kuato781/spirit-wave-stand/documentation/product-images/01-components.jpg

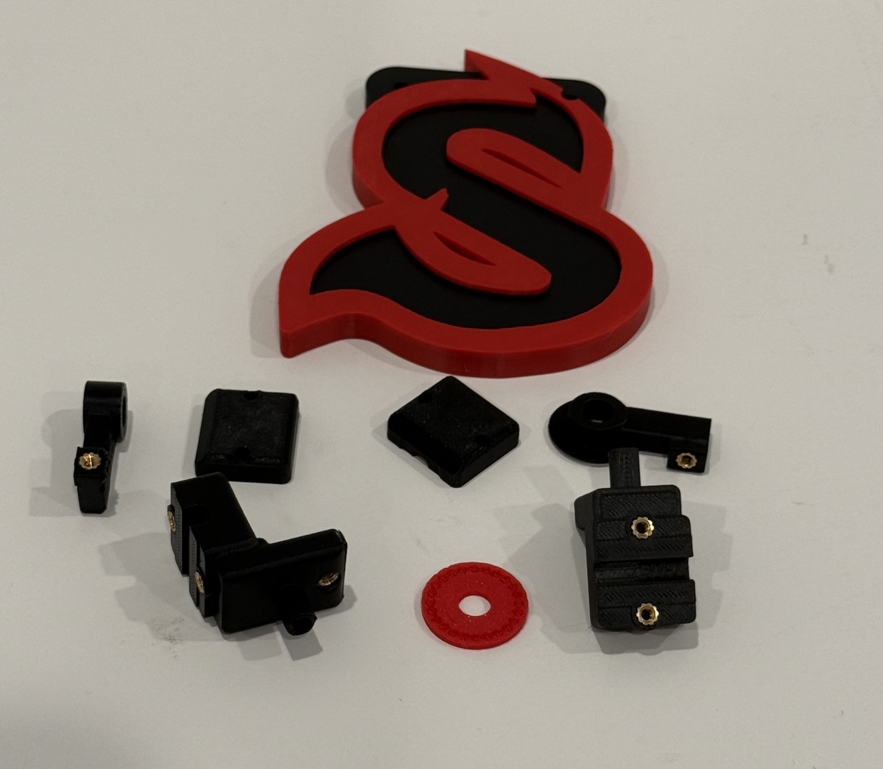
documentation/product-images/01-components.jpg
