kuato781/spirit-wave-stand/stl-scad/stand/SpiritWave-RED-LOWER.scad

module red_lower_2d() {
  union() {
    polygon(points=[[-44.12985,-99.23666], [-44.06508,-99.32389], [-43.99628,-99.40856], [-43.92369,-99.49047], [-43.84755,-99.56939], [-43.76811,-99.64512], [-43.68559,-99.71743], [-43.60024,-99.78611], [-43.51230,-99.85095], [-43.42201,-99.91172], [-43.32960,-99.96821], [-43.23531,-100.02021], [-43.13938,-100.06749], [-43.04206,-100.10985], [-42.94358,-100.14706], [-42.84417,-100.17892], [-42.74409,-100.20519], [-42.64356,-100.22568], [-42.54282,-100.24016], [-42.44212,-100.24841], [-42.34170,-100.25022], [-42.24178,-100.24537], [-42.14261,-100.23368], [-42.04425,-100.21529], [-41.94667,-100.19057], [-41.84984,-100.15990], [-41.75373,-100.12367], [-41.65830,-100.08225], [-41.56353,-100.03602], [-41.46937,-99.98537], [-41.37581,-99.93066], [-41.28280,-99.87229], [-41.19031,-99.81063], [-41.09831,-99.74607], [-41.00677,-99.67897], [-40.91565,-99.60973], [-40.82493,-99.53871], [-40.73457,-99.46631], [-40.64453,-99.39289], [-40.55479,-99.31885], [-40.46531,-99.24456], [-40.37606,-99.17039], [-40.28701,-99.09665], [-40.19815,-99.02337], [-40.10945,-98.95055], [-40.02092,-98.87817], [-39.93253,-98.80622], [-39.84426,-98.73471], [-39.75612,-98.66362], [-39.66807,-98.59294], [-39.58011,-98.52267], [-39.49223,-98.45280], [-39.40440,-98.38332], [-39.31662,-98.31422], [-39.22887,-98.24549], [-39.14114,-98.17713], [-39.05342,-98.10913], [-38.96568,-98.04148], [-38.87792,-97.97417], [-38.79012,-97.90719], [-38.70226,-97.84055], [-38.61435,-97.77422], [-38.52635,-97.70820], [-38.43826,-97.64248], [-38.35006,-97.57706], [-38.26173,-97.51193], [-38.17328,-97.44708], [-38.08467,-97.38249], [-37.99590,-97.31817], [-37.90695,-97.25411], [-37.81781,-97.19029], [-37.72846,-97.12671], [-37.63889,-97.06337], [-37.54909,-97.00024], [-37.45905,-96.93733], [-37.36874,-96.87463], [-37.27815,-96.81213], [-37.18728,-96.74983], [-37.09610,-96.68770], [-37.00461,-96.62575], [-36.91278,-96.56397], [-36.82063,-96.50235], [-36.72816,-96.44088], [-36.63539,-96.37957], [-36.54234,-96.31839], [-36.44901,-96.25735], [-36.35543,-96.19643], [-36.26160,-96.13564], [-36.16754,-96.07496], [-36.07326,-96.01439], [-35.97879,-95.95392], [-35.88412,-95.89355], [-35.78928,-95.83327], [-35.69429,-95.77307], [-35.59915,-95.71294], [-35.50387,-95.65289], [-35.40848,-95.59289], [-35.31299,-95.53295], [-35.21741,-95.47307], [-35.12176,-95.41322], [-35.02604,-95.35341], [-34.93028,-95.29363], [-34.83449,-95.23388], [-34.73867,-95.17414], [-34.64286,-95.11441], [-34.54705,-95.05469], [-34.45127,-94.99496], [-34.35553,-94.93522], [-34.25984,-94.87547], [-34.16422,-94.81569], [-34.06868,-94.75589], [-33.97323,-94.69605], [-33.87790,-94.63616], [-33.78268,-94.57623], [-33.68761,-94.51625], [-33.59268,-94.45620], [-33.49792,-94.39608], [-33.40335,-94.33589], [-33.30896,-94.27562], [-33.21476,-94.21528], [-33.12072,-94.15490], [-33.02681,-94.09452], [-32.93301,-94.03416], [-32.83930,-93.97386], [-32.74564,-93.91364], [-32.65202,-93.85353], [-32.55841,-93.79357], [-32.46477,-93.73377], [-32.37110,-93.67419], [-32.27736,-93.61483], [-32.18352,-93.55574], [-32.08957,-93.49694], [-31.99547,-93.43846], [-31.90120,-93.38034], [-31.80674,-93.32259], [-31.71206,-93.26527], [-31.61713,-93.20838], [-31.52194,-93.15197], [-31.42644,-93.09606], [-31.33063,-93.04068], [-31.23447,-92.98586], [-31.13794,-92.93164], [-31.04101,-92.87804], [-30.94366,-92.82509], [-30.84586,-92.77283], [-30.74759,-92.72127], [-30.64883,-92.67046], [-30.54953,-92.62042], [-30.44969,-92.57118], [-30.34928,-92.52278], [-30.24827,-92.47524], [-30.14663,-92.42859], [-30.04434,-92.38286], [-29.94138,-92.33808], [-29.83772,-92.29429], [-29.73333,-92.25150], [-29.62819,-92.20976], [-29.52232,-92.16908], [-29.41573,-92.12947], [-29.30846,-92.09093], [-29.20052,-92.05350], [-29.09196,-92.01717], [-28.98279,-91.98196], [-28.87303,-91.94788], [-28.76273,-91.91494], [-28.65189,-91.88315], [-28.54055,-91.85254], [-28.42874,-91.82310], [-28.31648,-91.79485], [-28.20379,-91.76780], [-28.09071,-91.74197], [-27.97726,-91.71736], [-27.86346,-91.69400], [-27.74935,-91.67188], [-27.63494,-91.65102], [-27.52027,-91.63144], [-27.40536,-91.61315], [-27.29024,-91.59615], [-27.17493,-91.58046], [-27.05946,-91.56610], [-26.94385,-91.55307], [-26.82814,-91.54138], [-26.71235,-91.53105], [-26.59650,-91.52210], [-26.48063,-91.51452], [-26.36475,-91.50834], [-26.24889,-91.50356], [-26.13309,-91.50021], [-26.01736,-91.49828], [-25.90173,-91.49779], [-25.78624,-91.49876], [-25.67090,-91.50120], [-25.55574,-91.50511], [-25.44078,-91.51051], [-25.32607,-91.51741], [-25.21161,-91.52583], [-25.09743,-91.53576], [-24.98354,-91.54718], [-24.86995,-91.56009], [-24.75667,-91.57446], [-24.64371,-91.59027], [-24.53108,-91.60750], [-24.41878,-91.62615], [-24.30683,-91.64618], [-24.19524,-91.66758], [-24.08401,-91.69034], [-23.97315,-91.71444], [-23.86268,-91.73985], [-23.75261,-91.76657], [-23.64294,-91.79457], [-23.53368,-91.82383], [-23.42485,-91.85434], [-23.31644,-91.88608], [-23.20848,-91.91904], [-23.10097,-91.95318], [-22.99392,-91.98851], [-22.88733,-92.02499], [-22.78123,-92.06261], [-22.67562,-92.10136], [-22.57050,-92.14121], [-22.46590,-92.18215], [-22.36181,-92.22415], [-22.25824,-92.26721], [-22.15522,-92.31130], [-22.05273,-92.35641], [-21.95081,-92.40252], [-21.84944,-92.44961], [-21.74866,-92.49766], [-21.64845,-92.54665], [-21.54884,-92.59657], [-21.44983,-92.64740], [-21.35143,-92.69913], [-21.25366,-92.75172], [-21.15651,-92.80517], [-21.06000,-92.85946], [-20.96413,-92.91457], [-20.86886,-92.97045], [-20.77416,-93.02709], [-20.68001,-93.08444], [-20.58639,-93.14249], [-20.49326,-93.20120], [-20.40061,-93.26053], [-20.30839,-93.32046], [-20.21659,-93.38096], [-20.12518,-93.44199], [-20.03413,-93.50352], [-19.94342,-93.56553], [-19.85301,-93.62799], [-19.76289,-93.69085], [-19.67302,-93.75409], [-19.58337,-93.81769], [-19.49393,-93.88160], [-19.40466,-93.94581], [-19.31554,-94.01026], [-19.22653,-94.07495], [-19.13763,-94.13983], [-19.04878,-94.20488], [-18.95998,-94.27006], [-18.87119,-94.33534], [-18.78238,-94.40069], [-18.69353,-94.46609], [-18.60462,-94.53150], [-18.51560,-94.59688], [-18.42647,-94.66221], [-18.33719,-94.72746], [-18.24773,-94.79260], [-18.15807,-94.85760], [-18.06818,-94.92241], [-17.97804,-94.98703], [-17.88761,-95.05140], [-17.79687,-95.11551], [-17.70579,-95.17932], [-17.61435,-95.24280], [-17.52253,-95.30592], [-17.43033,-95.36870], [-17.33777,-95.43112], [-17.24484,-95.49320], [-17.15157,-95.55494], [-17.05796,-95.61633], [-16.96402,-95.67739], [-16.86976,-95.73811], [-16.77518,-95.79850], [-16.68030,-95.85856], [-16.58513,-95.91829], [-16.48967,-95.97771], [-16.39394,-96.03680], [-16.29794,-96.09557], [-16.20169,-96.15403], [-16.10518,-96.21218], [-16.00844,-96.27002], [-15.91147,-96.32756], [-15.81427,-96.38479], [-15.71687,-96.44173], [-15.61927,-96.49837], [-15.52147,-96.55471], [-15.42348,-96.61077], [-15.32533,-96.66653], [-15.22701,-96.72202], [-15.12853,-96.77722], [-15.02990,-96.83214], [-14.93114,-96.88679], [-14.83225,-96.94117], [-14.73324,-96.99527], [-14.63411,-97.04911], [-14.53489,-97.10269], [-14.43558,-97.15600], [-14.33618,-97.20906], [-14.23671,-97.26186], [-14.13717,-97.31441], [-14.03758,-97.36671], [-13.93794,-97.41877], [-13.83827,-97.47058], [-13.73854,-97.52214], [-13.63877,-97.57346], [-13.53895,-97.62454], [-13.43908,-97.67536], [-13.33914,-97.72594], [-13.23915,-97.77627], [-13.13908,-97.82634], [-13.03895,-97.87617], [-12.93875,-97.92574], [-12.83847,-97.97506], [-12.73811,-98.02412], [-12.63767,-98.07293], [-12.53714,-98.12149], [-12.43652,-98.16978], [-12.33581,-98.21782], [-12.23500,-98.26560], [-12.13409,-98.31311], [-12.03307,-98.36037], [-11.93195,-98.40736], [-11.83071,-98.45410], [-11.72936,-98.50056], [-11.62789,-98.54677], [-11.52630,-98.59270], [-11.42458,-98.63837], [-11.32273,-98.68377], [-11.22075,-98.72891], [-11.11863,-98.77377], [-11.01638,-98.81836], [-10.91397,-98.86269], [-10.81143,-98.90673], [-10.70873,-98.95051], [-10.60587,-98.99401], [-10.50286,-99.03724], [-10.39969,-99.08019], [-10.29635,-99.12286], [-10.19284,-99.16525], [-10.08916,-99.20737], [-9.98531,-99.24920], [-9.88129,-99.29076], [-9.77710,-99.33203], [-9.67275,-99.37303], [-9.56824,-99.41374], [-9.46357,-99.45417], [-9.35875,-99.49433], [-9.25378,-99.53420], [-9.14866,-99.57379], [-9.04340,-99.61310], [-8.93799,-99.65212], [-8.83245,-99.69087], [-8.72677,-99.72933], [-8.62096,-99.76752], [-8.51503,-99.80542], [-8.40896,-99.84303], [-8.30278,-99.88037], [-8.19648,-99.91742], [-8.09006,-99.95419], [-7.98353,-99.99067], [-7.87688,-100.02688], [-7.77014,-100.06280], [-7.66329,-100.09843], [-7.55634,-100.13379], [-7.44929,-100.16885], [-7.34215,-100.20364], [-7.23492,-100.23814], [-7.12760,-100.27235], [-7.02019,-100.30628], [-6.91271,-100.33993], [-6.80515,-100.37329], [-6.69751,-100.40637], [-6.58980,-100.43916], [-6.48203,-100.47166], [-6.37419,-100.50388], [-6.26628,-100.53581], [-6.15832,-100.56746], [-6.05030,-100.59882], [-5.94223,-100.62989], [-5.83410,-100.66067], [-5.72590,-100.69115], [-5.61763,-100.72133], [-5.50929,-100.75120], [-5.40087,-100.78076], [-5.29237,-100.81000], [-5.18378,-100.83891], [-5.07509,-100.86750], [-4.96632,-100.89576], [-4.85744,-100.92367], [-4.74845,-100.95125], [-4.63936,-100.97847], [-4.53015,-101.00535], [-4.42083,-101.03186], [-4.31137,-101.05802], [-4.20180,-101.08380], [-4.09208,-101.10922], [-3.98224,-101.13425], [-3.87225,-101.15890], [-3.76211,-101.18317], [-3.65182,-101.20704], [-3.54138,-101.23052], [-3.43078,-101.25359], [-3.32001,-101.27626], [-3.20908,-101.29851], [-3.09797,-101.32035], [-2.98669,-101.34176], [-2.87522,-101.36275], [-2.76357,-101.38330], [-2.65172,-101.40342], [-2.53968,-101.42309], [-2.42744,-101.44232], [-2.31499,-101.46110], [-2.20233,-101.47942], [-2.08946,-101.49727], [-1.97637,-101.51467], [-1.86306,-101.53158], [-1.74952,-101.54803], [-1.63575,-101.56399], [-1.52177,-101.57949], [-1.40757,-101.59453], [-1.29316,-101.60912], [-1.17854,-101.62325], [-1.06373,-101.63695], [-0.94873,-101.65022], [-0.83354,-101.66307], [-0.71818,-101.67549], [-0.60264,-101.68751], [-0.48693,-101.69912], [-0.37106,-101.71034], [-0.25504,-101.72117], [-0.13887,-101.73162], [-0.02255,-101.74170], [0.09391,-101.75141], [0.21049,-101.76076], [0.32721,-101.76976], [0.44404,-101.77841], [0.56099,-101.78673], [0.67804,-101.79471], [0.79520,-101.80238], [0.91246,-101.80973], [1.02980,-101.81677], [1.14723,-101.82351], [1.26474,-101.82995], [1.38232,-101.83611], [1.49997,-101.84199], [1.61768,-101.84760], [1.73545,-101.85295], [1.85326,-101.85803], [1.97112,-101.86287], [2.08902,-101.86747], [2.20694,-101.87182], [2.32490,-101.87595], [2.44287,-101.87986], [2.56086,-101.88356], [2.67885,-101.88705], [2.79684,-101.89034], [2.91484,-101.89344], [3.03282,-101.89634], [3.15080,-101.89905], [3.26876,-101.90155], [3.38672,-101.90386], [3.50465,-101.90596], [3.62257,-101.90785], [3.74047,-101.90952], [3.85835,-101.91098], [3.97620,-101.91223], [4.09402,-101.91325], [4.21182,-101.91404], [4.32958,-101.91461], [4.44732,-101.91494], [4.56501,-101.91504], [4.68267,-101.91491], [4.80029,-101.91453], [4.91787,-101.91391], [5.03540,-101.91303], [5.15289,-101.91191], [5.27033,-101.91054], [5.38772,-101.90891], [5.50505,-101.90701], [5.62233,-101.90486], [5.73955,-101.90244], [5.85671,-101.89974], [5.97381,-101.89678], [6.09085,-101.89354], [6.20782,-101.89002], [6.32472,-101.88621], [6.44155,-101.88212], [6.55831,-101.87775], [6.67499,-101.87308], [6.79160,-101.86811], [6.90813,-101.86285], [7.02457,-101.85728], [7.14093,-101.85141], [7.25721,-101.84523], [7.37339,-101.83874], [7.48949,-101.83194], [7.60549,-101.82482], [7.72140,-101.81738], [7.83721,-101.80961], [7.95293,-101.80152], [8.06854,-101.79309], [8.18404,-101.78433], [8.29945,-101.77524], [8.41474,-101.76581], [8.52992,-101.75603], [8.64499,-101.74591], [8.75995,-101.73543], [8.87479,-101.72461], [8.98951,-101.71343], [9.10411,-101.70189], [9.21858,-101.68998], [9.33293,-101.67772], [9.44715,-101.66508], [9.56124,-101.65207], [9.67520,-101.63869], [9.78903,-101.62493], [9.90272,-101.61079], [10.01627,-101.59626], [10.12968,-101.58134], [10.24294,-101.56604], [10.35606,-101.55034], [10.46903,-101.53424], [10.58185,-101.51774], [10.69452,-101.50084], [10.80704,-101.48354], [10.91940,-101.46582], [11.03160,-101.44769], [11.14364,-101.42914], [11.25551,-101.41017], [11.36723,-101.39078], [11.47877,-101.37097], [11.59014,-101.35072], [11.70135,-101.33005], [11.81237,-101.30893], [11.92322,-101.28738], [12.03390,-101.26539], [12.14439,-101.24295], [12.25470,-101.22007], [12.36484,-101.19677], [12.47482,-101.17305], [12.58463,-101.14893], [12.69429,-101.12443], [12.80381,-101.09956], [12.91318,-101.07434], [13.02242,-101.04877], [13.13153,-101.02288], [13.24053,-100.99668], [13.34941,-100.97018], [13.45818,-100.94339], [13.56685,-100.91634], [13.67542,-100.88903], [13.78391,-100.86148], [13.89232,-100.83371], [14.00065,-100.80572], [14.10892,-100.77754], [14.21712,-100.74917], [14.32527,-100.72064], [14.43337,-100.69195], [14.54143,-100.66312], [14.64945,-100.63417], [14.75745,-100.60511], [14.86542,-100.57595], [14.97338,-100.54671], [15.08132,-100.51740], [15.18927,-100.48804], [15.29722,-100.45864], [15.40518,-100.42921], [15.51316,-100.39978], [15.62116,-100.37035], [15.72919,-100.34093], [15.83726,-100.31155], [15.94537,-100.28222], [16.05353,-100.25295], [16.16175,-100.22376], [16.27003,-100.19465], [16.37838,-100.16565], [16.48680,-100.13675], [16.59529,-100.10795], [16.70384,-100.07924], [16.81246,-100.05061], [16.92113,-100.02205], [17.02986,-99.99356], [17.13865,-99.96513], [17.24748,-99.93675], [17.35637,-99.90841], [17.46531,-99.88010], [17.57429,-99.85183], [17.68331,-99.82357], [17.79237,-99.79533], [17.90146,-99.76709], [18.01059,-99.73885], [18.11976,-99.71061], [18.22895,-99.68234], [18.33817,-99.65405], [18.44741,-99.62573], [18.55668,-99.59736], [18.66596,-99.56895], [18.77526,-99.54048], [18.88458,-99.51195], [18.99390,-99.48336], [19.10324,-99.45468], [19.21258,-99.42591], [19.32192,-99.39706], [19.43127,-99.36810], [19.54061,-99.33904], [19.64996,-99.30986], [19.75929,-99.28055], [19.86862,-99.25112], [19.97793,-99.22155], [20.08723,-99.19183], [20.19652,-99.16195], [20.30578,-99.13192], [20.41503,-99.10172], [20.52425,-99.07134], [20.63344,-99.04078], [20.74261,-99.01002], [20.85174,-98.97907], [20.96084,-98.94791], [21.06989,-98.91655], [21.17890,-98.88498], [21.28787,-98.85321], [21.39677,-98.82123], [21.50562,-98.78903], [21.61440,-98.75663], [21.72312,-98.72401], [21.83176,-98.69118], [21.94032,-98.65813], [22.04879,-98.62487], [22.15718,-98.59138], [22.26547,-98.55768], [22.37366,-98.52376], [22.48176,-98.48961], [22.58974,-98.45524], [22.69761,-98.42064], [22.80536,-98.38582], [22.91299,-98.35077], [23.02048,-98.31549], [23.12785,-98.27998], [23.23508,-98.24424], [23.34217,-98.20826], [23.44911,-98.17205], [23.55590,-98.13560], [23.66253,-98.09892], [23.76900,-98.06199], [23.87530,-98.02483], [23.98143,-97.98742], [24.08738,-97.94977], [24.19315,-97.91187], [24.29874,-97.87373], [24.40413,-97.83535], [24.50933,-97.79671], [24.61433,-97.75782], [24.71912,-97.71868], [24.82371,-97.67929], [24.92807,-97.63965], [25.03223,-97.59975], [25.13618,-97.55959], [25.23992,-97.51917], [25.34347,-97.47849], [25.44683,-97.43755], [25.55000,-97.39635], [25.65300,-97.35488], [25.75581,-97.31314], [25.85846,-97.27114], [25.96094,-97.22886], [26.06326,-97.18631], [26.16543,-97.14349], [26.26744,-97.10039], [26.36932,-97.05702], [26.47105,-97.01337], [26.57265,-96.96944], [26.67412,-96.92522], [26.77547,-96.88073], [26.87670,-96.83594], [26.97782,-96.79088], [27.07883,-96.74552], [27.17974,-96.69987], [27.28055,-96.65394], [27.38127,-96.60771], [27.48191,-96.56118], [27.58246,-96.51436], [27.68293,-96.46724], [27.78334,-96.41983], [27.88368,-96.37211], [27.98396,-96.32408], [28.08418,-96.27576], [28.18436,-96.22713], [28.28449,-96.17819], [28.38458,-96.12894], [28.48463,-96.07938], [28.58466,-96.02951], [28.68466,-95.97932], [28.78465,-95.92882], [28.88461,-95.87801], [28.98455,-95.82688], [29.08446,-95.77543], [29.18433,-95.72368], [29.28415,-95.67162], [29.38392,-95.61926], [29.48363,-95.56659], [29.58327,-95.51361], [29.68284,-95.46034], [29.78233,-95.40677], [29.88173,-95.35290], [29.98104,-95.29874], [30.08025,-95.24428], [30.17935,-95.18953], [30.27833,-95.13450], [30.37719,-95.07917], [30.47592,-95.02356], [30.57452,-94.96767], [30.67298,-94.91150], [30.77128,-94.85505], [30.86943,-94.79831], [30.96742,-94.74131], [31.06523,-94.68403], [31.16287,-94.62647], [31.26033,-94.56865], [31.35759,-94.51056], [31.45466,-94.45220], [31.55152,-94.39358], [31.64817,-94.33470], [31.74460,-94.27555], [31.84081,-94.21615], [31.93679,-94.15649], [32.03252,-94.09657], [32.12801,-94.03640], [32.22325,-93.97598], [32.31823,-93.91531], [32.41294,-93.85440], [32.50738,-93.79324], [32.60155,-93.73182], [32.69545,-93.67016], [32.78909,-93.60824], [32.88247,-93.54605], [32.97559,-93.48360], [33.06846,-93.42087], [33.16109,-93.35787], [33.25347,-93.29459], [33.34561,-93.23103], [33.43751,-93.16718], [33.52918,-93.10303], [33.62062,-93.03859], [33.71184,-92.97384], [33.80284,-92.90878], [33.89362,-92.84342], [33.98418,-92.77774], [34.07454,-92.71174], [34.16469,-92.64542], [34.25464,-92.57876], [34.34439,-92.51178], [34.43394,-92.44445], [34.52331,-92.37678], [34.61249,-92.30877], [34.70149,-92.24041], [34.79030,-92.17169], [34.87895,-92.10261], [34.96742,-92.03317], [35.05572,-91.96335], [35.14386,-91.89317], [35.23184,-91.82261], [35.31967,-91.75166], [35.40734,-91.68033], [35.49486,-91.60861], [35.58224,-91.53649], [35.66948,-91.46398], [35.75658,-91.39106], [35.84355,-91.31773], [35.93039,-91.24399], [36.01709,-91.16984], [36.10364,-91.09530], [36.19003,-91.02036], [36.27624,-90.94503], [36.36228,-90.86933], [36.44812,-90.79326], [36.53376,-90.71683], [36.61919,-90.64003], [36.70439,-90.56289], [36.78935,-90.48541], [36.87407,-90.40759], [36.95854,-90.32944], [37.04273,-90.25097], [37.12665,-90.17219], [37.21028,-90.09310], [37.29361,-90.01371], [37.37663,-89.93403], [37.45932,-89.85407], [37.54169,-89.77382], [37.62372,-89.69331], [37.70539,-89.61253], [37.78669,-89.53149], [37.86763,-89.45020], [37.94818,-89.36867], [38.02833,-89.28691], [38.10808,-89.20491], [38.18741,-89.12270], [38.26631,-89.04027], [38.34477,-88.95763], [38.42278,-88.87480], [38.50034,-88.79177], [38.57742,-88.70855], [38.65402,-88.62516], [38.73013,-88.54159], [38.80574,-88.45786], [38.88084,-88.37398], [38.95541,-88.28994], [39.02944,-88.20576], [39.10296,-88.12143], [39.17596,-88.03695], [39.24845,-87.95232], [39.32046,-87.86753], [39.39197,-87.78258], [39.46302,-87.69747], [39.53360,-87.61218], [39.60373,-87.52673], [39.67342,-87.44110], [39.74268,-87.35529], [39.81152,-87.26930], [39.87995,-87.18313], [39.94798,-87.09676], [40.01562,-87.01020], [40.08288,-86.92345], [40.14977,-86.83649], [40.21631,-86.74933], [40.28249,-86.66196], [40.34834,-86.57439], [40.41387,-86.48659], [40.47907,-86.39858], [40.54397,-86.31035], [40.60858,-86.22189], [40.67290,-86.13320], [40.73695,-86.04428], [40.80073,-85.95512], [40.86426,-85.86573], [40.92754,-85.77609], [40.99059,-85.68620], [41.05342,-85.59606], [41.11604,-85.50567], [41.17846,-85.41502], [41.24068,-85.32411], [41.30273,-85.23293], [41.36460,-85.14148], [41.42632,-85.04977], [41.48788,-84.95777], [41.54931,-84.86550], [41.61061,-84.77294], [41.67177,-84.68010], [41.73279,-84.58698], [41.79364,-84.49359], [41.85433,-84.39991], [41.91483,-84.30596], [41.97514,-84.21174], [42.03523,-84.11724], [42.09511,-84.02248], [42.15475,-83.92745], [42.21415,-83.83216], [42.27328,-83.73660], [42.33215,-83.64078], [42.39073,-83.54470], [42.44902,-83.44837], [42.50700,-83.35178], [42.56466,-83.25493], [42.62198,-83.15784], [42.67896,-83.06049], [42.73558,-82.96290], [42.79183,-82.86506], [42.84770,-82.76698], [42.90317,-82.66866], [42.95823,-82.57010], [43.01287,-82.47130], [43.06708,-82.37227], [43.12085,-82.27300], [43.17416,-82.17350], [43.22699,-82.07377], [43.27935,-81.97381], [43.33121,-81.87363], [43.38256,-81.77323], [43.43339,-81.67260], [43.48369,-81.57175], [43.53344,-81.47069], [43.58264,-81.36940], [43.63127,-81.26791], [43.67932,-81.16620], [43.72678,-81.06429], [43.77367,-80.96219], [43.82002,-80.85991], [43.86586,-80.75748], [43.91121,-80.65492], [43.95608,-80.55224], [44.00052,-80.44946], [44.04453,-80.34660], [44.08816,-80.24368], [44.13141,-80.14071], [44.17431,-80.03772], [44.21690,-79.93471], [44.25919,-79.83172], [44.30121,-79.72876], [44.34298,-79.62584], [44.38452,-79.52298], [44.42587,-79.42021], [44.46705,-79.31754], [44.50807,-79.21499], [44.54895,-79.11256], [44.58967,-79.01020], [44.63019,-78.90788], [44.67048,-78.80556], [44.71052,-78.70318], [44.75027,-78.60071], [44.78971,-78.49810], [44.82880,-78.39531], [44.86752,-78.29229], [44.90583,-78.18901], [44.94370,-78.08541], [44.98112,-77.98145], [45.01803,-77.87710], [45.05443,-77.77230], [45.09027,-77.66701], [45.12552,-77.56119], [45.16017,-77.45480], [45.19417,-77.34779], [45.22749,-77.24012], [45.26013,-77.13176], [45.29209,-77.02276], [45.32340,-76.91318], [45.35409,-76.80311], [45.38418,-76.69260], [45.41372,-76.58173], [45.44271,-76.47056], [45.47120,-76.35917], [45.49921,-76.24761], [45.52677,-76.13597], [45.55390,-76.02430], [45.58064,-75.91269], [45.60700,-75.80118], [45.63303,-75.68986], [45.65874,-75.57880], [45.68417,-75.46806], [45.70935,-75.35770], [45.73429,-75.24781], [45.75903,-75.13844], [45.78360,-75.02967], [45.80800,-74.92147], [45.83220,-74.81378], [45.85619,-74.70655], [45.87995,-74.59969], [45.90346,-74.49314], [45.92671,-74.38685], [45.94968,-74.28073], [45.97234,-74.17474], [45.99469,-74.06879], [46.01669,-73.96282], [46.03834,-73.85678], [46.05962,-73.75058], [46.08050,-73.64417], [46.10097,-73.53747], [46.12101,-73.43043], [46.14061,-73.32298], [46.15974,-73.21505], [46.17838,-73.10657], [46.19652,-72.99748], [46.21415,-72.88773], [46.23126,-72.77733], [46.24785,-72.66630], [46.26393,-72.55468], [46.27948,-72.44247], [46.29452,-72.32971], [46.30904,-72.21641], [46.32305,-72.10260], [46.33654,-71.98831], [46.34951,-71.87355], [46.36197,-71.75836], [46.37391,-71.64274], [46.38534,-71.52673], [46.39625,-71.41035], [46.40665,-71.29362], [46.41653,-71.17656], [46.42590,-71.05921], [46.43476,-70.94157], [46.44310,-70.82368], [46.45093,-70.70555], [46.45825,-70.58721], [46.46506,-70.46869], [46.47135,-70.35000], [46.47714,-70.23118], [46.48241,-70.11223], [46.48717,-69.99319], [46.49142,-69.87408], [46.49516,-69.75492], [46.49839,-69.63574], [46.50111,-69.51655], [46.50332,-69.39739], [46.50502,-69.27827], [46.50622,-69.15921], [46.50690,-69.04025], [46.50708,-68.92140], [46.50675,-68.80268], [46.50591,-68.68413], [46.50456,-68.56576], [46.50271,-68.44759], [46.50035,-68.32965], [46.49749,-68.21196], [46.49412,-68.09452], [46.49025,-67.97732], [46.48588,-67.86036], [46.48102,-67.74364], [46.47566,-67.62715], [46.46982,-67.51089], [46.46348,-67.39485], [46.45667,-67.27904], [46.44936,-67.16344], [46.44158,-67.04805], [46.43333,-66.93287], [46.42459,-66.81789], [46.41539,-66.70312], [46.40572,-66.58854], [46.39558,-66.47416], [46.38497,-66.35996], [46.37391,-66.24595], [46.36239,-66.13212], [46.35041,-66.01847], [46.33798,-65.90499], [46.32510,-65.79168], [46.31177,-65.67853], [46.29799,-65.56555], [46.28377,-65.45272], [46.26912,-65.34005], [46.25402,-65.22753], [46.23849,-65.11515], [46.22253,-65.00291], [46.20614,-64.89082], [46.18933,-64.77885], [46.17209,-64.66702], [46.15442,-64.55531], [46.13634,-64.44372], [46.11785,-64.33225], [46.09894,-64.22090], [46.07962,-64.10966], [46.05989,-63.99852], [46.03975,-63.88748], [46.01922,-63.77655], [45.99828,-63.66571], [45.97693,-63.55498], [45.95518,-63.44436], [45.93301,-63.33385], [45.91043,-63.22345], [45.88744,-63.11318], [45.86402,-63.00304], [45.84019,-62.89302], [45.81593,-62.78314], [45.79125,-62.67339], [45.76614,-62.56379], [45.74060,-62.45434], [45.71463,-62.34503], [45.68822,-62.23588], [45.66137,-62.12689], [45.63409,-62.01807], [45.60636,-61.90941], [45.57818,-61.80092], [45.54956,-61.69261], [45.52049,-61.58448], [45.49096,-61.47653], [45.46098,-61.36877], [45.43055,-61.26121], [45.39965,-61.15384], [45.36829,-61.04667], [45.33647,-60.93971], [45.30418,-60.83296], [45.27142,-60.72643], [45.23819,-60.62011], [45.20449,-60.51401], [45.17030,-60.40814], [45.13564,-60.30250], [45.10050,-60.19710], [45.06487,-60.09194], [45.02876,-59.98702], [44.99216,-59.88234], [44.95506,-59.77792], [44.91747,-59.67376], [44.87939,-59.56985], [44.84081,-59.46621], [44.80173,-59.36282], [44.76216,-59.25969], [44.72209,-59.15681], [44.68153,-59.05419], [44.64048,-58.95181], [44.59894,-58.84967], [44.55690,-58.74778], [44.51438,-58.64612], [44.47136,-58.54470], [44.42786,-58.44352], [44.38387,-58.34257], [44.33939,-58.24184], [44.29443,-58.14134], [44.24898,-58.04106], [44.20305,-57.94101], [44.15663,-57.84117], [44.10974,-57.74154], [44.06236,-57.64213], [44.01450,-57.54293], [43.96616,-57.44393], [43.91734,-57.34514], [43.86805,-57.24655], [43.81827,-57.14815], [43.76802,-57.04995], [43.71730,-56.95195], [43.66610,-56.85413], [43.61443,-56.75651], [43.56228,-56.65906], [43.50966,-56.56180], [43.45657,-56.46472], [43.40301,-56.36782], [43.34899,-56.27109], [43.29449,-56.17453], [43.23952,-56.07814], [43.18409,-55.98191], [43.12819,-55.88585], [43.07183,-55.78995], [43.01500,-55.69421], [42.95771,-55.59863], [42.89996,-55.50323], [42.84174,-55.40799], [42.78306,-55.31294], [42.72391,-55.21807], [42.66430,-55.12339], [42.60423,-55.02891], [42.54370,-54.93462], [42.48270,-54.84053], [42.42124,-54.74666], [42.35932,-54.65299], [42.29694,-54.55955], [42.23410,-54.46632], [42.17079,-54.37333], [42.10703,-54.28056], [42.04280,-54.18803], [41.97812,-54.09575], [41.91297,-54.00371], [41.84736,-53.91192], [41.78130,-53.82038], [41.71477,-53.72911], [41.64779,-53.63810], [41.58034,-53.54736], [41.51244,-53.45690], [41.44408,-53.36672], [41.37526,-53.27682], [41.30599,-53.18721], [41.23625,-53.09789], [41.16606,-53.00888], [41.09541,-52.92016], [41.02431,-52.83176], [40.95274,-52.74367], [40.88072,-52.65589], [40.80825,-52.56844], [40.73532,-52.48132], [40.66193,-52.39453], [40.58808,-52.30807], [40.51379,-52.22196], [40.43905,-52.13618], [40.36388,-52.05074], [40.28828,-51.96564], [40.21227,-51.88087], [40.13584,-51.79644], [40.05902,-51.71234], [39.98181,-51.62858], [39.90422,-51.54515], [39.82625,-51.46205], [39.74793,-51.37928], [39.66924,-51.29684], [39.59021,-51.21473], [39.51085,-51.13295], [39.43116,-51.05149], [39.35115,-50.97036], [39.27082,-50.88955], [39.19020,-50.80907], [39.10929,-50.72891], [39.02809,-50.64908], [38.94661,-50.56956], [38.86488,-50.49037], [38.78288,-50.41149], [38.70064,-50.33294], [38.61815,-50.25470], [38.53544,-50.17677], [38.45251,-50.09917], [38.36936,-50.02187], [38.28601,-49.94490], [38.20247,-49.86823], [38.11874,-49.79188], [38.03483,-49.71584], [37.95076,-49.64010], [37.86652,-49.56468], [37.78214,-49.48957], [37.69762,-49.41476], [37.61296,-49.34026], [37.52818,-49.26607], [37.44328,-49.19218], [37.35827,-49.11859], [37.27314,-49.04530], [37.18787,-48.97232], [37.10248,-48.89962], [37.01694,-48.82722], [36.93125,-48.75511], [36.84540,-48.68329], [36.75939,-48.61175], [36.67322,-48.54050], [36.58686,-48.46953], [36.50032,-48.39883], [36.41359,-48.32841], [36.32666,-48.25827], [36.23953,-48.18839], [36.15218,-48.11878], [36.06462,-48.04944], [35.97683,-47.98036], [35.88881,-47.91155], [35.80055,-47.84299], [35.71205,-47.77468], [35.62329,-47.70663], [35.53427,-47.63883], [35.44498,-47.57128], [35.35542,-47.50397], [35.26558,-47.43691], [35.17546,-47.37008], [35.08504,-47.30350], [34.99431,-47.23715], [34.90328,-47.17103], [34.81193,-47.10515], [34.72026,-47.03949], [34.62826,-46.97406], [34.53593,-46.90885], [34.44325,-46.84387], [34.35023,-46.77910], [34.25684,-46.71455], [34.16310,-46.65021], [34.06898,-46.58608], [33.97448,-46.52216], [33.87960,-46.45845], [33.78436,-46.39492], [33.68930,-46.33131], [33.59543,-46.26710], [33.50376,-46.20180], [33.41532,-46.13487], [33.33111,-46.06583], [33.25216,-45.99414], [33.17948,-45.91930], [33.11410,-45.84081], [33.05670,-45.75829], [33.00704,-45.67179], [32.96474,-45.58144], [32.92940,-45.48736], [32.90063,-45.38966], [32.87803,-45.28846], [32.86123,-45.18388], [32.84981,-45.07605], [32.84340,-44.96507], [32.84160,-44.85108], [32.84402,-44.73419], [32.85028,-44.61464], [32.86010,-44.49310], [32.87319,-44.37037], [32.88929,-44.24724], [32.90812,-44.12448], [32.92940,-44.00289], [32.95285,-43.88326], [32.97821,-43.76636], [33.00520,-43.65290], [33.03355,-43.54282], [33.06302,-43.43567], [33.09334,-43.33101], [33.12426,-43.22837], [33.15553,-43.12733], [33.18689,-43.02742], [33.21809,-42.92819], [33.24887,-42.82920], [33.27897,-42.73000], [33.30814,-42.63013], [33.33614,-42.52917], [33.36286,-42.42691], [33.38835,-42.32340], [33.41267,-42.21871], [33.43587,-42.11288], [33.45801,-42.00597], [33.47914,-41.89803], [33.49932,-41.78913], [33.51859,-41.67931], [33.53702,-41.56864], [33.55466,-41.45717], [33.57156,-41.34495], [33.58778,-41.23204], [33.60337,-41.11849], [33.61839,-41.00437], [33.63289,-40.88973], [33.64692,-40.77461], [33.66054,-40.65909], [33.67381,-40.54321], [33.68677,-40.42703], [33.69949,-40.31060], [33.71201,-40.19399], [33.72440,-40.07724], [33.73670,-39.96042], [33.74897,-39.84357], [33.76127,-39.72676], [33.77365,-39.61003], [33.78616,-39.49346], [33.79886,-39.37708], [33.81180,-39.26096], [33.82504,-39.14515], [33.83863,-39.02970], [33.85262,-38.91468], [33.86708,-38.80015], [33.88205,-38.68614], [33.89759,-38.57273], [33.91375,-38.45996], [33.93059,-38.34789], [33.94817,-38.23658], [33.96653,-38.12608], [33.98572,-38.01644], [34.00568,-37.90760], [34.02635,-37.79949], [34.04764,-37.69203], [34.06946,-37.58514], [34.09175,-37.47873], [34.11442,-37.37274], [34.13740,-37.26708], [34.16060,-37.16166], [34.18394,-37.05642], [34.20735,-36.95127], [34.23074,-36.84614], [34.25404,-36.74093], [34.27717,-36.63559], [34.30004,-36.53001], [34.32258,-36.42413], [34.34472,-36.31787], [34.36636,-36.21115], [34.38743,-36.10388], [34.40785,-35.99599], [34.42759,-35.88744], [34.44665,-35.77826], [34.46508,-35.66847], [34.48290,-35.55813], [34.50015,-35.44725], [34.51686,-35.33588], [34.53305,-35.22405], [34.54876,-35.11181], [34.56401,-34.99917], [34.57885,-34.88618], [34.59329,-34.77287], [34.60737,-34.65929], [34.62113,-34.54545], [34.63458,-34.43141], [34.64777,-34.31719], [34.66072,-34.20282], [34.67346,-34.08836], [34.68603,-33.97382], [34.69845,-33.85925], [34.71076,-33.74467], [34.72297,-33.63013], [34.73510,-33.51560], [34.74713,-33.40110], [34.75907,-33.28662], [34.77092,-33.17215], [34.78268,-33.05769], [34.79434,-32.94324], [34.80591,-32.82879], [34.81738,-32.71434], [34.82875,-32.59988], [34.84002,-32.48541], [34.85120,-32.37093], [34.86228,-32.25643], [34.87325,-32.14191], [34.88412,-32.02736], [34.89490,-31.91278], [34.90556,-31.79817], [34.91612,-31.68353], [34.92658,-31.56884], [34.93693,-31.45411], [34.94717,-31.33933], [34.95731,-31.22450], [34.96733,-31.10961], [34.97725,-30.99466], [34.98705,-30.87964], [34.99674,-30.76456], [35.00632,-30.64940], [35.01579,-30.53417], [35.02514,-30.41886], [35.03437,-30.30347], [35.04349,-30.18798], [35.05249,-30.07241], [35.06137,-29.95674], [35.07013,-29.84097], [35.07878,-29.72509], [35.08730,-29.60911], [35.09570,-29.49302], [35.10397,-29.37681], [35.11212,-29.26049], [35.12015,-29.14404], [35.12805,-29.02746], [35.13582,-28.91077], [35.14345,-28.79395], [35.15095,-28.67703], [35.15829,-28.55999], [35.16550,-28.44285], [35.17254,-28.32561], [35.17943,-28.20828], [35.18616,-28.09085], [35.19272,-27.97333], [35.19911,-27.85573], [35.20533,-27.73805], [35.21136,-27.62030], [35.21722,-27.50247], [35.22288,-27.38458], [35.22835,-27.26662], [35.23362,-27.14861], [35.23869,-27.03054], [35.24356,-26.91242], [35.24821,-26.79425], [35.25265,-26.67604], [35.25687,-26.55779], [35.26086,-26.43951], [35.26463,-26.32120], [35.26816,-26.20287], [35.27146,-26.08451], [35.27451,-25.96614], [35.27732,-25.84775], [35.27988,-25.72936], [35.28218,-25.61096], [35.28422,-25.49256], [35.28600,-25.37416], [35.28751,-25.25577], [35.28875,-25.13740], [35.28971,-25.01904], [35.29039,-24.90070], [35.29078,-24.78238], [35.29088,-24.66410], [35.29069,-24.54584], [35.29019,-24.42763], [35.28940,-24.30945], [35.28829,-24.19133], [35.28688,-24.07325], [35.28514,-23.95522], [35.28308,-23.83725], [35.28070,-23.71935], [35.27799,-23.60151], [35.27494,-23.48374], [35.27155,-23.36605], [35.26782,-23.24843], [35.26374,-23.13090], [35.25931,-23.01346], [35.25452,-22.89611], [35.24937,-22.77885], [35.24386,-22.66169], [35.23797,-22.54464], [35.23171,-22.42769], [35.22507,-22.31086], [35.21804,-22.19414], [35.21063,-22.07755], [35.20282,-21.96108], [35.19462,-21.84473], [35.18602,-21.72852], [35.17701,-21.61245], [35.16759,-21.49652], [35.15776,-21.38074], [35.14750,-21.26510], [35.13682,-21.14962], [35.12572,-21.03430], [35.11418,-20.91914], [35.10221,-20.80414], [35.08979,-20.68932], [35.07693,-20.57467], [35.06362,-20.46020], [35.04985,-20.34592], [35.03563,-20.23182], [35.02094,-20.11791], [35.00578,-20.00420], [34.99015,-19.89069], [34.97404,-19.77738], [34.95746,-19.66428], [34.94039,-19.55138], [34.92284,-19.43869], [34.90482,-19.32620], [34.88631,-19.21391], [34.86733,-19.10182], [34.84787,-18.98992], [34.82793,-18.87822], [34.80751,-18.76671], [34.78662,-18.65538], [34.76525,-18.54425], [34.74341,-18.43330], [34.72109,-18.32253], [34.69830,-18.21195], [34.67503,-18.10154], [34.65129,-17.99132], [34.62708,-17.88126], [34.60239,-17.77138], [34.57723,-17.66168], [34.55160,-17.55214], [34.52550,-17.44277], [34.49893,-17.33356], [34.47189,-17.22452], [34.44437,-17.11563], [34.41639,-17.00691], [34.38794,-16.89835], [34.35903,-16.78993], [34.32964,-16.68168], [34.29979,-16.57357], [34.26947,-16.46561], [34.23868,-16.35780], [34.20743,-16.25013], [34.17572,-16.14261], [34.14354,-16.03523], [34.11089,-15.92798], [34.07778,-15.82088], [34.04421,-15.71390], [34.01018,-15.60707], [33.97568,-15.50036], [33.94072,-15.39378], [33.90530,-15.28733], [33.86943,-15.18102], [33.83310,-15.07486], [33.79632,-14.96884], [33.75910,-14.86296], [33.72143,-14.75724], [33.68331,-14.65168], [33.64476,-14.54627], [33.60577,-14.44104], [33.56634,-14.33596], [33.52649,-14.23107], [33.48620,-14.12634], [33.44549,-14.02180], [33.40435,-13.91744], [33.36279,-13.81327], [33.32081,-13.70929], [33.27842,-13.60550], [33.23561,-13.50191], [33.19239,-13.39853], [33.14877,-13.29535], [33.10474,-13.19239], [33.06031,-13.08964], [33.01547,-12.98710], [32.97024,-12.88479], [32.92462,-12.78271], [32.87860,-12.68085], [32.83220,-12.57923], [32.78541,-12.47785], [32.73823,-12.37671], [32.69068,-12.27581], [32.64274,-12.17516], [32.59443,-12.07477], [32.54575,-11.97463], [32.49670,-11.87476], [32.44727,-11.77515], [32.39749,-11.67581], [32.34734,-11.57674], [32.29683,-11.47794], [32.24597,-11.37940], [32.19477,-11.28110], [32.14323,-11.18303], [32.09136,-11.08516], [32.03917,-10.98748], [31.98666,-10.88996], [31.93385,-10.79260], [31.88074,-10.69537], [31.82734,-10.59826], [31.77365,-10.50124], [31.71969,-10.40431], [31.66546,-10.30743], [31.61097,-10.21060], [31.55623,-10.11379], [31.50124,-10.01699], [31.44601,-9.92018], [31.39055,-9.82334], [31.33487,-9.72645], [31.27898,-9.62950], [31.22288,-9.53247], [31.16658,-9.43534], [31.11008,-9.33809], [31.05340,-9.24070], [30.99655,-9.14316], [30.93952,-9.04544], [30.88234,-8.94754], [30.82500,-8.84943], [30.76751,-8.75109], [30.70988,-8.65251], [30.65213,-8.55366], [30.59424,-8.45454], [30.53625,-8.35511], [30.47814,-8.25538], [30.41994,-8.15530], [30.36164,-8.05488], [30.30325,-7.95408], [30.24479,-7.85291], [30.18595,-7.75199], [30.12576,-7.65357], [30.06310,-7.56005], [29.99691,-7.47390], [29.92607,-7.39753], [29.84952,-7.33338], [29.76614,-7.28389], [29.67489,-7.25147], [29.57600,-7.23695], [29.47163,-7.23892], [29.36404,-7.25579], [29.25553,-7.28597], [29.14839,-7.32786], [29.04490,-7.37989], [28.94734,-7.44046], [28.85800,-7.50798], [28.77917,-7.58087], [28.71314,-7.65752], [28.66159,-7.73664], [28.62411,-7.81790], [28.59987,-7.90117], [28.58799,-7.98635], [28.58763,-8.07332], [28.59792,-8.16196], [28.61801,-8.25217], [28.64705,-8.34383], [28.68418,-8.43681], [28.72853,-8.53102], [28.77926,-8.62632], [28.83552,-8.72262], [28.89643,-8.81979], [28.96115,-8.91772], [29.02882,-9.01629], [29.09859,-9.11539], [29.16959,-9.21491], [29.24098,-9.31473], [29.31189,-9.41473], [29.38181,-9.51486], [29.45072,-9.61509], [29.51862,-9.71544], [29.58555,-9.81590], [29.65153,-9.91648], [29.71658,-10.01717], [29.78071,-10.11799], [29.84395,-10.21893], [29.90632,-10.31998], [29.96784,-10.42117], [30.02854,-10.52248], [30.08843,-10.62391], [30.14753,-10.72548], [30.20587,-10.82717], [30.26346,-10.92899], [30.32033,-11.03095], [30.37650,-11.13305], [30.43199,-11.23528], [30.48682,-11.33764], [30.54101,-11.44015], [30.59459,-11.54280], [30.64757,-11.64558], [30.69997,-11.74852], [30.75182,-11.85159], [30.80314,-11.95482], [30.85394,-12.05819], [30.90426,-12.16171], [30.95410,-12.26539], [31.00350,-12.36922], [31.05246,-12.47320], [31.10102,-12.57733], [31.14920,-12.68163], [31.19701,-12.78608], [31.24448,-12.89069], [31.29162,-12.99547], [31.33847,-13.10041], [31.38503,-13.20551], [31.43134,-13.31078], [31.47740,-13.41622], [31.52321,-13.52183], [31.56876,-13.62760], [31.61404,-13.73354], [31.65905,-13.83964], [31.70377,-13.94591], [31.74820,-14.05235], [31.79233,-14.15895], [31.83614,-14.26571], [31.87964,-14.37264], [31.92282,-14.47974], [31.96565,-14.58699], [32.00814,-14.69441], [32.05028,-14.80199], [32.09206,-14.90974], [32.13347,-15.01764], [32.17450,-15.12571], [32.21514,-15.23393], [32.25538,-15.34232], [32.29523,-15.45087], [32.33465,-15.55958], [32.37366,-15.66844], [32.41224,-15.77747], [32.45038,-15.88665], [32.48807,-15.99599], [32.52531,-16.10549], [32.56208,-16.21515], [32.59838,-16.32496], [32.63420,-16.43493], [32.66953,-16.54505], [32.70435,-16.65533], [32.73868,-16.76577], [32.77249,-16.87636], [32.80577,-16.98710], [32.83852,-17.09800], [32.87073,-17.20905], [32.90239,-17.32025], [32.93349,-17.43161], [32.96403,-17.54312], [32.99399,-17.65478], [33.02340,-17.76659], [33.05225,-17.87854], [33.08054,-17.99064], [33.10828,-18.10288], [33.13546,-18.21525], [33.16210,-18.32777], [33.18820,-18.44042], [33.21376,-18.55320], [33.23878,-18.66612], [33.26326,-18.77916], [33.28722,-18.89233], [33.31065,-19.00562], [33.33356,-19.11904], [33.35594,-19.23257], [33.37781,-19.34623], [33.39916,-19.46000], [33.42000,-19.57388], [33.44034,-19.68787], [33.46017,-19.80197], [33.47950,-19.91618], [33.49833,-20.03049], [33.51666,-20.14491], [33.53451,-20.25942], [33.55187,-20.37404], [33.56874,-20.48875], [33.58513,-20.60355], [33.60104,-20.71844], [33.61648,-20.83343], [33.63145,-20.94850], [33.64594,-21.06365], [33.65998,-21.17889], [33.67355,-21.29421], [33.68666,-21.40961], [33.69931,-21.52508], [33.71152,-21.64063], [33.72327,-21.75625], [33.73458,-21.87193], [33.74544,-21.98769], [33.75587,-22.10351], [33.76586,-22.21940], [33.77542,-22.33534], [33.78455,-22.45134], [33.79325,-22.56741], [33.80153,-22.68352], [33.80939,-22.79969], [33.81683,-22.91590], [33.82386,-23.03217], [33.83048,-23.14848], [33.83669,-23.26483], [33.84250,-23.38123], [33.84791,-23.49766], [33.85292,-23.61413], [33.85754,-23.73064], [33.86177,-23.84717], [33.86561,-23.96374], [33.86907,-24.08034], [33.87214,-24.19696], [33.87484,-24.31361], [33.87716,-24.43028], [33.87912,-24.54696], [33.88070,-24.66367], [33.88192,-24.78039], [33.88278,-24.89712], [33.88329,-25.01386], [33.88343,-25.13061], [33.88323,-25.24737], [33.88268,-25.36413], [33.88178,-25.48090], [33.88054,-25.59766], [33.87897,-25.71442], [33.87705,-25.83118], [33.87481,-25.94793], [33.87224,-26.06467], [33.86934,-26.18140], [33.86612,-26.29811], [33.86258,-26.41481], [33.85872,-26.53150], [33.85456,-26.64816], [33.85008,-26.76480], [33.84530,-26.88142], [33.84022,-26.99802], [33.83484,-27.11459], [33.82917,-27.23114], [33.82321,-27.34767], [33.81697,-27.46417], [33.81045,-27.58065], [33.80365,-27.69710], [33.79658,-27.81353], [33.78925,-27.92992], [33.78164,-28.04630], [33.77378,-28.16264], [33.76567,-28.27895], [33.75730,-28.39524], [33.74869,-28.51150], [33.73983,-28.62773], [33.73074,-28.74392], [33.72141,-28.86009], [33.71185,-28.97622], [33.70206,-29.09232], [33.69205,-29.20839], [33.68182,-29.32443], [33.67138,-29.44043], [33.66073,-29.55640], [33.64987,-29.67234], [33.63881,-29.78824], [33.62755,-29.90410], [33.61610,-30.01993], [33.60446,-30.13572], [33.59264,-30.25147], [33.58063,-30.36718], [33.56844,-30.48286], [33.55609,-30.59850], [33.54356,-30.71410], [33.53087,-30.82965], [33.51802,-30.94517], [33.50501,-31.06065], [33.49185,-31.17608], [33.47854,-31.29148], [33.46509,-31.40683], [33.45150,-31.52214], [33.43777,-31.63740], [33.42391,-31.75262], [33.40992,-31.86779], [33.39581,-31.98292], [33.38158,-32.09801], [33.36723,-32.21304], [33.35277,-32.32803], [33.33821,-32.44298], [33.32354,-32.55787], [33.30877,-32.67272], [33.29391,-32.78752], [33.27896,-32.90227], [33.26392,-33.01696], [33.24879,-33.13161], [33.23359,-33.24621], [33.21832,-33.36075], [33.20298,-33.47524], [33.18756,-33.58968], [33.17209,-33.70407], [33.15656,-33.81840], [33.14098,-33.93268], [33.12534,-34.04691], [33.10967,-34.16108], [33.09395,-34.27519], [33.07819,-34.38924], [33.06240,-34.50324], [33.04658,-34.61718], [33.03073,-34.73107], [33.01487,-34.84489], [32.99899,-34.95866], [32.98309,-35.07237], [32.96719,-35.18601], [32.95128,-35.29960], [32.93538,-35.41312], [32.91947,-35.52659], [32.90358,-35.63999], [32.88770,-35.75332], [32.87183,-35.86660], [32.85598,-35.97981], [32.84016,-36.09296], [32.82436,-36.20604], [32.80858,-36.31906], [32.79281,-36.43202], [32.77702,-36.54493], [32.76122,-36.65778], [32.74538,-36.77059], [32.72951,-36.88335], [32.71358,-36.99606], [32.69759,-37.10874], [32.68152,-37.22137], [32.66536,-37.33398], [32.64911,-37.44655], [32.63275,-37.55909], [32.61627,-37.67161], [32.59966,-37.78410], [32.58290,-37.89658], [32.56599,-38.00904], [32.54892,-38.12148], [32.53167,-38.23392], [32.51423,-38.34634], [32.49659,-38.45877], [32.47874,-38.57119], [32.46066,-38.68361], [32.44236,-38.79603], [32.42381,-38.90847], [32.40500,-39.02091], [32.38593,-39.13337], [32.36657,-39.24584], [32.34693,-39.35834], [32.32699,-39.47085], [32.30673,-39.58339], [32.28616,-39.69596], [32.26524,-39.80856], [32.24398,-39.92119], [32.22236,-40.03386], [32.20038,-40.14658], [32.17801,-40.25933], [32.15525,-40.37213], [32.13209,-40.48498], [32.10852,-40.59789], [32.08455,-40.71084], [32.06023,-40.82385], [32.03562,-40.93692], [32.01079,-41.05003], [31.98579,-41.16320], [31.96068,-41.27642], [31.93551,-41.38970], [31.91035,-41.50302], [31.88526,-41.61640], [31.86028,-41.72983], [31.83549,-41.84331], [31.81094,-41.95684], [31.78668,-42.07042], [31.76279,-42.18405], [31.73930,-42.29773], [31.71629,-42.41146], [31.69381,-42.52524], [31.67192,-42.63906], [31.65068,-42.75294], [31.63015,-42.86686], [31.61038,-42.98083], [31.59144,-43.09485], [31.57337,-43.20891], [31.55625,-43.32303], [31.54013,-43.43718], [31.52506,-43.55139], [31.51111,-43.66563], [31.49833,-43.77993], [31.48679,-43.89427], [31.47653,-44.00865], [31.46763,-44.12308], [31.46013,-44.23755], [31.45410,-44.35207], [31.44960,-44.46663], [31.44667,-44.58123], [31.44539,-44.69588], [31.44581,-44.81056], [31.44799,-44.92529], [31.45198,-45.04006], [31.45785,-45.15487], [31.46572,-45.26958], [31.47570,-45.38406], [31.48793,-45.49814], [31.50255,-45.61166], [31.51968,-45.72445], [31.53945,-45.83638], [31.56200,-45.94726], [31.58746,-46.05694], [31.61595,-46.16527], [31.64761,-46.27209], [31.68256,-46.37723], [31.72095,-46.48053], [31.76289,-46.58185], [31.80853,-46.68101], [31.85799,-46.77786], [31.91140,-46.87223], [31.96890,-46.96398], [32.03061,-47.05294], [32.09666,-47.13894], [32.16708,-47.22194], [32.24164,-47.30209], [32.32006,-47.37959], [32.40206,-47.45464], [32.48739,-47.52745], [32.57576,-47.59820], [32.66690,-47.66710], [32.76055,-47.73434], [32.85642,-47.80013], [32.95426,-47.86467], [33.05378,-47.92814], [33.15471,-47.99076], [33.25679,-48.05272], [33.35974,-48.11421], [33.46328,-48.17544], [33.56716,-48.23661], [33.67108,-48.29791], [33.77479,-48.35955], [33.87802,-48.42172], [33.98049,-48.48461], [34.08211,-48.54830], [34.18289,-48.61277], [34.28284,-48.67801], [34.38200,-48.74400], [34.48037,-48.81074], [34.57797,-48.87819], [34.67483,-48.94635], [34.77095,-49.01519], [34.86636,-49.08472], [34.96108,-49.15490], [35.05512,-49.22573], [35.14850,-49.29718], [35.24124,-49.36925], [35.33335,-49.44191], [35.42486,-49.51516], [35.51578,-49.58897], [35.60614,-49.66333], [35.69594,-49.73822], [35.78521,-49.81364], [35.87396,-49.88956], [35.96221,-49.96596], [36.04999,-50.04284], [36.13730,-50.12018], [36.22417,-50.19795], [36.31062,-50.27615], [36.39666,-50.35477], [36.48230,-50.43377], [36.56758,-50.51316], [36.65250,-50.59290], [36.73709,-50.67300], [36.82136,-50.75343], [36.90533,-50.83417], [36.98901,-50.91522], [37.07243,-50.99655], [37.15561,-51.07815], [37.23856,-51.16000], [37.32130,-51.24209], [37.40384,-51.32441], [37.48622,-51.40693], [37.56843,-51.48965], [37.65048,-51.57256], [37.73237,-51.65566], [37.81408,-51.73897], [37.89560,-51.82247], [37.97694,-51.90618], [38.05808,-51.99009], [38.13902,-52.07421], [38.21975,-52.15855], [38.30026,-52.24310], [38.38054,-52.32787], [38.46060,-52.41285], [38.54041,-52.49807], [38.61997,-52.58350], [38.69928,-52.66917], [38.77833,-52.75507], [38.85711,-52.84120], [38.93561,-52.92757], [39.01383,-53.01418], [39.09176,-53.10103], [39.16940,-53.18813], [39.24672,-53.27548], [39.32374,-53.36308], [39.40044,-53.45093], [39.47681,-53.53904], [39.55284,-53.62741], [39.62854,-53.71605], [39.70388,-53.80495], [39.77888,-53.89411], [39.85350,-53.98355], [39.92776,-54.07326], [40.00164,-54.16325], [40.07514,-54.25352], [40.14825,-54.34407], [40.22095,-54.43490], [40.29326,-54.52603], [40.36514,-54.61744], [40.43661,-54.70915], [40.50765,-54.80116], [40.57825,-54.89346], [40.64842,-54.98607], [40.71813,-55.07898], [40.78739,-55.17219], [40.85618,-55.26572], [40.92450,-55.35957], [40.99234,-55.45372], [41.05970,-55.54820], [41.12657,-55.64300], [41.19293,-55.73812], [41.25879,-55.83357], [41.32413,-55.92936], [41.38896,-56.02547], [41.45325,-56.12192], [41.51701,-56.21871], [41.58022,-56.31584], [41.64288,-56.41331], [41.70499,-56.51113], [41.76653,-56.60930], [41.82750,-56.70783], [41.88789,-56.80671], [41.94769,-56.90594], [42.00690,-57.00554], [42.06551,-57.10550], [42.12351,-57.20583], [42.18089,-57.30653], [42.23765,-57.40760], [42.29378,-57.50905], [42.34928,-57.61087], [42.40413,-57.71308], [42.45832,-57.81567], [42.51186,-57.91864], [42.56473,-58.02201], [42.61693,-58.12576], [42.66845,-58.22991], [42.71928,-58.33446], [42.76942,-58.43941], [42.81885,-58.54476], [42.86758,-58.65052], [42.91559,-58.75669], [42.96288,-58.86326], [43.00946,-58.97023], [43.05535,-59.07759], [43.10054,-59.18532], [43.14506,-59.29341], [43.18891,-59.40185], [43.23210,-59.51063], [43.27464,-59.61975], [43.31655,-59.72918], [43.35782,-59.83893], [43.39848,-59.94897], [43.43852,-60.05929], [43.47797,-60.16990], [43.51682,-60.28076], [43.55510,-60.39188], [43.59280,-60.50325], [43.62995,-60.61484], [43.66655,-60.72666], [43.70260,-60.83869], [43.73813,-60.95092], [43.77313,-61.06333], [43.80762,-61.17592], [43.84161,-61.28868], [43.87511,-61.40160], [43.90813,-61.51465], [43.94068,-61.62785], [43.97276,-61.74116], [44.00439,-61.85459], [44.03558,-61.96812], [44.06634,-62.08174], [44.09668,-62.19543], [44.12660,-62.30920], [44.15612,-62.42302], [44.18525,-62.53689], [44.21400,-62.65079], [44.24237,-62.76472], [44.27037,-62.87867], [44.29803,-62.99261], [44.32533,-63.10656], [44.35227,-63.22050], [44.37884,-63.33444], [44.40503,-63.44839], [44.43084,-63.56235], [44.45626,-63.67631], [44.48128,-63.79027], [44.50589,-63.90425], [44.53008,-64.01823], [44.55385,-64.13223], [44.57719,-64.24624], [44.60009,-64.36027], [44.62255,-64.47431], [44.64455,-64.58837], [44.66609,-64.70245], [44.68716,-64.81655], [44.70775,-64.93067], [44.72786,-65.04482], [44.74747,-65.15899], [44.76658,-65.27319], [44.78519,-65.38742], [44.80328,-65.50168], [44.82084,-65.61596], [44.83787,-65.73028], [44.85437,-65.84464], [44.87031,-65.95903], [44.88570,-66.07346], [44.90053,-66.18793], [44.91479,-66.30243], [44.92847,-66.41698], [44.94156,-66.53157], [44.95406,-66.64621], [44.96596,-66.76089], [44.97724,-66.87562], [44.98792,-66.99040], [44.99796,-67.10523], [45.00738,-67.22011], [45.01615,-67.33505], [45.02428,-67.45004], [45.03175,-67.56509], [45.03858,-67.68018], [45.04476,-67.79533], [45.05029,-67.91053], [45.05519,-68.02577], [45.05945,-68.14105], [45.06307,-68.25637], [45.06606,-68.37173], [45.06842,-68.48712], [45.07016,-68.60254], [45.07127,-68.71800], [45.07176,-68.83348], [45.07163,-68.94899], [45.07089,-69.06451], [45.06954,-69.18006], [45.06757,-69.29562], [45.06500,-69.41120], [45.06182,-69.52679], [45.05804,-69.64239], [45.05367,-69.75799], [45.04869,-69.87360], [45.04313,-69.98921], [45.03697,-70.10482], [45.03023,-70.22042], [45.02290,-70.33602], [45.01499,-70.45161], [45.00649,-70.56719], [44.99743,-70.68275], [44.98779,-70.79830], [44.97757,-70.91383], [44.96679,-71.02933], [44.95545,-71.14482], [44.94354,-71.26027], [44.93107,-71.37570], [44.91805,-71.49109], [44.90447,-71.60645], [44.89034,-71.72178], [44.87566,-71.83706], [44.86043,-71.95230], [44.84466,-72.06750], [44.82835,-72.18265], [44.81150,-72.29775], [44.79412,-72.41280], [44.77621,-72.52780], [44.75776,-72.64273], [44.73879,-72.75761], [44.71930,-72.87242], [44.69929,-72.98717], [44.67875,-73.10186], [44.65770,-73.21647], [44.63614,-73.33101], [44.61407,-73.44547], [44.59149,-73.55986], [44.56841,-73.67416], [44.54483,-73.78839], [44.52074,-73.90252], [44.49616,-74.01658], [44.47109,-74.13053], [44.44553,-74.24440], [44.41948,-74.35817], [44.39294,-74.47185], [44.36593,-74.58542], [44.33843,-74.69889], [44.31046,-74.81225], [44.28201,-74.92551], [44.25309,-75.03865], [44.22371,-75.15168], [44.19385,-75.26460], [44.16354,-75.37739], [44.13276,-75.49007], [44.10153,-75.60262], [44.06985,-75.71505], [44.03771,-75.82734], [44.00512,-75.93951], [43.97209,-76.05154], [43.93862,-76.16344], [43.90470,-76.27519], [43.87035,-76.38681], [43.83556,-76.49828], [43.80034,-76.60960], [43.76468,-76.72078], [43.72860,-76.83181], [43.69208,-76.94268], [43.65514,-77.05340], [43.61776,-77.16396], [43.57996,-77.27437], [43.54172,-77.38462], [43.50307,-77.49470], [43.46398,-77.60462], [43.42447,-77.71437], [43.38454,-77.82396], [43.34418,-77.93338], [43.30339,-78.04262], [43.26219,-78.15169], [43.22056,-78.26059], [43.17852,-78.36930], [43.13605,-78.47784], [43.09316,-78.58620], [43.04986,-78.69437], [43.00613,-78.80235], [42.96199,-78.91015], [42.91744,-79.01776], [42.87247,-79.12518], [42.82708,-79.23240], [42.78128,-79.33943], [42.73506,-79.44626], [42.68844,-79.55290], [42.64140,-79.65933], [42.59395,-79.76555], [42.54609,-79.87158], [42.49782,-79.97739], [42.44915,-80.08300], [42.40006,-80.18839], [42.35057,-80.29357], [42.30067,-80.39854], [42.25037,-80.50329], [42.19966,-80.60782], [42.14855,-80.71213], [42.09703,-80.81621], [42.04511,-80.92007], [41.99279,-81.02371], [41.94007,-81.12711], [41.88695,-81.23029], [41.83343,-81.33323], [41.77951,-81.43594], [41.72519,-81.53841], [41.67048,-81.64064], [41.61537,-81.74263], [41.55986,-81.84438], [41.50396,-81.94588], [41.44766,-82.04714], [41.39097,-82.14814], [41.33389,-82.24890], [41.27642,-82.34941], [41.21856,-82.44966], [41.16030,-82.54965], [41.10166,-82.64939], [41.04262,-82.74886], [40.98320,-82.84808], [40.92340,-82.94703], [40.86320,-83.04571], [40.80262,-83.14412], [40.74166,-83.24227], [40.68031,-83.34014], [40.61857,-83.43774], [40.55646,-83.53506], [40.49396,-83.63210], [40.43108,-83.72887], [40.36783,-83.82535], [40.30419,-83.92155], [40.24017,-84.01746], [40.17578,-84.11308], [40.11100,-84.20842], [40.04585,-84.30346], [39.98033,-84.39821], [39.91443,-84.49266], [39.84816,-84.58682], [39.78152,-84.68068], [39.71451,-84.77424], [39.64714,-84.86751], [39.57940,-84.96048], [39.51131,-85.05314], [39.44285,-85.14551], [39.37404,-85.23758], [39.30488,-85.32935], [39.23536,-85.42081], [39.16550,-85.51198], [39.09529,-85.60284], [39.02473,-85.69340], [38.95383,-85.78365], [38.88260,-85.87360], [38.81103,-85.96325], [38.73912,-86.05258], [38.66688,-86.14162], [38.59431,-86.23034], [38.52141,-86.31876], [38.44819,-86.40687], [38.37464,-86.49467], [38.30077,-86.58216], [38.22659,-86.66935], [38.15209,-86.75622], [38.07727,-86.84278], [38.00215,-86.92903], [37.92671,-87.01496], [37.85097,-87.10059], [37.77492,-87.18590], [37.69858,-87.27089], [37.62193,-87.35557], [37.54498,-87.43994], [37.46774,-87.52399], [37.39021,-87.60772], [37.31239,-87.69113], [37.23428,-87.77423], [37.15588,-87.85701], [37.07720,-87.93947], [36.99824,-88.02161], [36.91899,-88.10343], [36.83946,-88.18494], [36.75965,-88.26613], [36.67955,-88.34701], [36.59916,-88.42757], [36.51848,-88.50783], [36.43751,-88.58777], [36.35625,-88.66740], [36.27470,-88.74672], [36.19286,-88.82573], [36.11072,-88.90444], [36.02829,-88.98285], [35.94557,-89.06094], [35.86255,-89.13874], [35.77923,-89.21624], [35.69561,-89.29343], [35.61169,-89.37032], [35.52747,-89.44692], [35.44295,-89.52322], [35.35813,-89.59922], [35.27300,-89.67492], [35.18757,-89.75034], [35.10183,-89.82546], [35.01579,-89.90028], [34.92944,-89.97482], [34.84278,-90.04907], [34.75581,-90.12303], [34.66853,-90.19670], [34.58094,-90.27009], [34.49303,-90.34319], [34.40481,-90.41601], [34.31628,-90.48854], [34.22743,-90.56079], [34.13827,-90.63277], [34.04879,-90.70446], [33.95898,-90.77588], [33.86886,-90.84702], [33.77842,-90.91788], [33.68766,-90.98847], [33.59658,-91.05878], [33.50518,-91.12881], [33.41347,-91.19857], [33.32146,-91.26804], [33.22913,-91.33724], [33.13651,-91.40616], [33.04358,-91.47479], [32.95036,-91.54314], [32.85684,-91.61121], [32.76304,-91.67899], [32.66894,-91.74649], [32.57456,-91.81369], [32.47990,-91.88061], [32.38496,-91.94725], [32.28974,-92.01359], [32.19426,-92.07964], [32.09850,-92.14539], [32.00247,-92.21086], [31.90619,-92.27603], [31.80964,-92.34090], [31.71283,-92.40548], [31.61578,-92.46976], [31.51847,-92.53374], [31.42091,-92.59743], [31.32310,-92.66081], [31.22506,-92.72389], [31.12677,-92.78667], [31.02825,-92.84915], [30.92950,-92.91132], [30.83052,-92.97319], [30.73131,-93.03475], [30.63187,-93.09600], [30.53222,-93.15694], [30.43235,-93.21758], [30.33226,-93.27790], [30.23196,-93.33791], [30.13146,-93.39761], [30.03074,-93.45700], [29.92983,-93.51607], [29.82872,-93.57483], [29.72741,-93.63327], [29.62590,-93.69139], [29.52421,-93.74920], [29.42233,-93.80668], [29.32026,-93.86385], [29.21802,-93.92069], [29.11559,-93.97721], [29.01299,-94.03340], [28.91022,-94.08928], [28.80728,-94.14482], [28.70418,-94.20004], [28.60091,-94.25493], [28.49748,-94.30950], [28.39389,-94.36373], [28.29016,-94.41763], [28.18627,-94.47120], [28.08223,-94.52444], [27.97805,-94.57735], [27.87373,-94.62992], [27.76926,-94.68215], [27.66467,-94.73405], [27.55994,-94.78561], [27.45508,-94.83683], [27.35009,-94.88771], [27.24499,-94.93825], [27.13976,-94.98845], [27.03441,-95.03831], [26.92895,-95.08782], [26.82338,-95.13698], [26.71771,-95.18581], [26.61192,-95.23428], [26.50604,-95.28241], [26.40005,-95.33018], [26.29398,-95.37761], [26.18780,-95.42469], [26.08154,-95.47141], [25.97519,-95.51778], [25.86876,-95.56380], [25.76225,-95.60946], [25.65566,-95.65477], [25.54899,-95.69973], [25.44224,-95.74435], [25.33541,-95.78862], [25.22851,-95.83255], [25.12153,-95.87615], [25.01448,-95.91943], [24.90735,-95.96237], [24.80014,-96.00500], [24.69286,-96.04730], [24.58551,-96.08929], [24.47808,-96.13098], [24.37058,-96.17235], [24.26300,-96.21343], [24.15536,-96.25421], [24.04764,-96.29469], [23.93985,-96.33488], [23.83199,-96.37479], [23.72406,-96.41441], [23.61606,-96.45376], [23.50798,-96.49283], [23.39984,-96.53164], [23.29163,-96.57017], [23.18336,-96.60845], [23.07501,-96.64646], [22.96660,-96.68423], [22.85812,-96.72174], [22.74957,-96.75900], [22.64096,-96.79603], [22.53228,-96.83281], [22.42354,-96.86936], [22.31473,-96.90568], [22.20586,-96.94178], [22.09692,-96.97765], [21.98792,-97.01330], [21.87886,-97.04874], [21.76974,-97.08397], [21.66055,-97.11899], [21.55131,-97.15381], [21.44200,-97.18843], [21.33263,-97.22286], [21.22320,-97.25709], [21.11371,-97.29114], [21.00416,-97.32501], [20.89456,-97.35869], [20.78489,-97.39221], [20.67517,-97.42555], [20.56539,-97.45872], [20.45555,-97.49173], [20.34566,-97.52459], [20.23571,-97.55729], [20.12570,-97.58984], [20.01564,-97.62224], [19.90553,-97.65449], [19.79536,-97.68661], [19.68514,-97.71860], [19.57486,-97.75045], [19.46453,-97.78218], [19.35415,-97.81378], [19.24372,-97.84526], [19.13323,-97.87663], [19.02270,-97.90789], [18.91211,-97.93904], [18.80147,-97.97009], [18.69079,-98.00104], [18.58005,-98.03189], [18.46927,-98.06265], [18.35844,-98.09332], [18.24756,-98.12392], [18.13663,-98.15443], [18.02565,-98.18486], [17.91463,-98.21523], [17.80357,-98.24553], [17.69246,-98.27576], [17.58130,-98.30593], [17.47010,-98.33605], [17.35885,-98.36612], [17.24756,-98.39614], [17.13623,-98.42610], [17.02487,-98.45600], [16.91346,-98.48584], [16.80203,-98.51561], [16.69056,-98.54531], [16.57907,-98.57494], [16.46755,-98.60449], [16.35601,-98.63396], [16.24445,-98.66334], [16.13287,-98.69263], [16.02127,-98.72182], [15.90966,-98.75092], [15.79804,-98.77992], [15.68641,-98.80881], [15.57478,-98.83759], [15.46314,-98.86626], [15.35151,-98.89481], [15.23987,-98.92324], [15.12824,-98.95154], [15.01662,-98.97972], [14.90500,-99.00776], [14.79340,-99.03566], [14.68181,-99.06343], [14.57023,-99.09105], [14.45868,-99.11852], [14.34715,-99.14584], [14.23564,-99.17300], [14.12416,-99.20001], [14.01271,-99.22684], [13.90129,-99.25351], [13.78990,-99.28001], [13.67855,-99.30634], [13.56724,-99.33248], [13.45597,-99.35844], [13.34474,-99.38421], [13.23356,-99.40979], [13.12243,-99.43518], [13.01135,-99.46036], [12.90032,-99.48535], [12.78933,-99.51014], [12.67837,-99.53473], [12.56745,-99.55913], [12.45655,-99.58333], [12.34567,-99.60734], [12.23480,-99.63115], [12.12394,-99.65478], [12.01308,-99.67821], [11.90221,-99.70146], [11.79134,-99.72452], [11.68044,-99.74739], [11.56952,-99.77008], [11.45858,-99.79259], [11.34760,-99.81491], [11.23657,-99.83705], [11.12551,-99.85901], [11.01439,-99.88079], [10.90321,-99.90240], [10.79196,-99.92383], [10.68065,-99.94508], [10.56926,-99.96616], [10.45779,-99.98707], [10.34623,-100.00780], [10.23457,-100.02837], [10.12282,-100.04876], [10.01096,-100.06899], [9.89899,-100.08906], [9.78690,-100.10895], [9.67469,-100.12868], [9.56234,-100.14825], [9.44987,-100.16766], [9.33725,-100.18691], [9.22448,-100.20600], [9.11157,-100.22493], [8.99849,-100.24370], [8.88525,-100.26232], [8.77183,-100.28078], [8.65825,-100.29909], [8.54448,-100.31725], [8.43054,-100.33522], [8.31643,-100.35301], [8.20216,-100.37058], [8.08774,-100.38792], [7.97317,-100.40502], [7.85846,-100.42186], [7.74361,-100.43841], [7.62863,-100.45467], [7.51352,-100.47061], [7.39830,-100.48622], [7.28297,-100.50147], [7.16753,-100.51636], [7.05199,-100.53086], [6.93636,-100.54496], [6.82064,-100.55863], [6.70483,-100.57187], [6.58896,-100.58465], [6.47301,-100.59696], [6.35700,-100.60877], [6.24093,-100.62007], [6.12482,-100.63085], [6.00865,-100.64108], [5.89245,-100.65075], [5.77621,-100.65984], [5.65995,-100.66833], [5.54367,-100.67621], [5.42737,-100.68346], [5.31107,-100.69005], [5.19476,-100.69598], [5.07846,-100.70122], [4.96216,-100.70576], [4.84588,-100.70958], [4.72963,-100.71266], [4.61340,-100.71499], [4.49720,-100.71654], [4.38105,-100.71730], [4.26494,-100.71725], [4.14889,-100.71638], [4.03289,-100.71466], [3.91695,-100.71210], [3.80108,-100.70871], [3.68527,-100.70453], [3.56953,-100.69956], [3.45385,-100.69383], [3.33823,-100.68737], [3.22269,-100.68020], [3.10720,-100.67234], [2.99179,-100.66380], [2.87644,-100.65463], [2.76115,-100.64483], [2.64594,-100.63442], [2.53079,-100.62344], [2.41572,-100.61191], [2.30071,-100.59983], [2.18577,-100.58725], [2.07091,-100.57418], [1.95611,-100.56064], [1.84139,-100.54665], [1.72673,-100.53225], [1.61215,-100.51744], [1.49765,-100.50226], [1.38322,-100.48672], [1.26886,-100.47084], [1.15457,-100.45466], [1.04036,-100.43819], [0.92623,-100.42145], [0.81217,-100.40447], [0.69819,-100.38726], [0.58429,-100.36986], [0.47046,-100.35228], [0.35671,-100.33455], [0.24304,-100.31668], [0.12945,-100.29870], [0.01594,-100.28064], [-0.09749,-100.26251], [-0.21085,-100.24434], [-0.32412,-100.22615], [-0.43730,-100.20796], [-0.55041,-100.18979], [-0.66343,-100.17165], [-0.77638,-100.15352], [-0.88924,-100.13538], [-1.00201,-100.11723], [-1.11471,-100.09905], [-1.22732,-100.08082], [-1.33986,-100.06252], [-1.45231,-100.04415], [-1.56468,-100.02569], [-1.67696,-100.00712], [-1.78917,-99.98843], [-1.90129,-99.96960], [-2.01333,-99.95063], [-2.12529,-99.93149], [-2.23717,-99.91217], [-2.34897,-99.89265], [-2.46069,-99.87292], [-2.57232,-99.85297], [-2.68388,-99.83279], [-2.79535,-99.81234], [-2.90674,-99.79163], [-3.01806,-99.77064], [-3.12929,-99.74935], [-3.24044,-99.72775], [-3.35151,-99.70582], [-3.46249,-99.68354], [-3.57340,-99.66092], [-3.68423,-99.63792], [-3.79497,-99.61453], [-3.90564,-99.59074], [-4.01623,-99.56654], [-4.12673,-99.54191], [-4.23715,-99.51683], [-4.34750,-99.49129], [-4.45776,-99.46528], [-4.56795,-99.43878], [-4.67805,-99.41178], [-4.78808,-99.38426], [-4.89802,-99.35620], [-5.00788,-99.32760], [-5.11767,-99.29846], [-5.22737,-99.26880], [-5.33699,-99.23861], [-5.44652,-99.20791], [-5.55597,-99.17671], [-5.66533,-99.14501], [-5.77461,-99.11283], [-5.88379,-99.08017], [-5.99289,-99.04704], [-6.10190,-99.01346], [-6.21081,-98.97943], [-6.31964,-98.94496], [-6.42837,-98.91006], [-6.53700,-98.87473], [-6.64554,-98.83899], [-6.75398,-98.80285], [-6.86233,-98.76631], [-6.97057,-98.72939], [-7.07872,-98.69209], [-7.18676,-98.65442], [-7.29470,-98.61640], [-7.40254,-98.57802], [-7.51028,-98.53930], [-7.61791,-98.50025], [-7.72543,-98.46087], [-7.83285,-98.42118], [-7.94016,-98.38119], [-8.04735,-98.34090], [-8.15444,-98.30032], [-8.26142,-98.25946], [-8.36828,-98.21834], [-8.47503,-98.17695], [-8.58167,-98.13531], [-8.68819,-98.09343], [-8.79459,-98.05132], [-8.90088,-98.00898], [-9.00704,-97.96642], [-9.11309,-97.92366], [-9.21901,-97.88070], [-9.32482,-97.83754], [-9.43050,-97.79418], [-9.53606,-97.75061], [-9.64150,-97.70683], [-9.74681,-97.66284], [-9.85200,-97.61863], [-9.95707,-97.57421], [-10.06202,-97.52957], [-10.16684,-97.48470], [-10.27154,-97.43961], [-10.37612,-97.39429], [-10.48057,-97.34874], [-10.58489,-97.30295], [-10.68909,-97.25693], [-10.79317,-97.21066], [-10.89712,-97.16416], [-11.00094,-97.11740], [-11.10464,-97.07040], [-11.20821,-97.02315], [-11.31166,-96.97564], [-11.41498,-96.92788], [-11.51817,-96.87985], [-11.62123,-96.83156], [-11.72417,-96.78301], [-11.82698,-96.73418], [-11.92966,-96.68509], [-12.03221,-96.63572], [-12.13463,-96.58607], [-12.23693,-96.53615], [-12.33909,-96.48594], [-12.44113,-96.43544], [-12.54303,-96.38466], [-12.64480,-96.33358], [-12.74645,-96.28221], [-12.84796,-96.23055], [-12.94934,-96.17858], [-13.05060,-96.12631], [-13.15171,-96.07373], [-13.25270,-96.02085], [-13.35356,-95.96765], [-13.45428,-95.91414], [-13.55487,-95.86032], [-13.65533,-95.80617], [-13.75565,-95.75170], [-13.85584,-95.69690], [-13.95590,-95.64178], [-14.05582,-95.58632], [-14.15561,-95.53053], [-14.25527,-95.47441], [-14.35479,-95.41794], [-14.45417,-95.36113], [-14.55342,-95.30397], [-14.65253,-95.24647], [-14.75151,-95.18861], [-14.85035,-95.13040], [-14.94905,-95.07183], [-15.04762,-95.01291], [-15.14605,-94.95362], [-15.24434,-94.89396], [-15.34250,-94.83394], [-15.44051,-94.77354], [-15.53839,-94.71277], [-15.63613,-94.65162], [-15.73373,-94.59010], [-15.83120,-94.52819], [-15.92852,-94.46589], [-16.02570,-94.40321], [-16.12275,-94.34013], [-16.21965,-94.27666], [-16.31642,-94.21280], [-16.41304,-94.14853], [-16.50952,-94.08386], [-16.60586,-94.01879], [-16.70206,-93.95331], [-16.79812,-93.88741], [-16.89403,-93.82111], [-16.98981,-93.75438], [-17.08545,-93.68726], [-17.18097,-93.61980], [-17.27640,-93.55201], [-17.37174,-93.48396], [-17.46701,-93.41567], [-17.56223,-93.34720], [-17.65742,-93.27857], [-17.75259,-93.20983], [-17.84776,-93.14103], [-17.94294,-93.07219], [-18.03816,-93.00337], [-18.13342,-92.93460], [-18.22874,-92.86592], [-18.32414,-92.79737], [-18.41964,-92.72900], [-18.51525,-92.66084], [-18.61099,-92.59294], [-18.70688,-92.52533], [-18.80293,-92.45806], [-18.89915,-92.39117], [-18.99557,-92.32469], [-19.09220,-92.25867], [-19.18905,-92.19314], [-19.28615,-92.12816], [-19.38351,-92.06375], [-19.48114,-91.99997], [-19.57906,-91.93684], [-19.67730,-91.87442], [-19.77585,-91.81273], [-19.87475,-91.75183], [-19.97401,-91.69175], [-20.07363,-91.63253], [-20.17365,-91.57421], [-20.27408,-91.51684], [-20.37493,-91.46046], [-20.47621,-91.40509], [-20.57795,-91.35080], [-20.68017,-91.29760], [-20.78286,-91.24555], [-20.88604,-91.19465], [-20.98969,-91.14489], [-21.09381,-91.09626], [-21.19839,-91.04878], [-21.30343,-91.00243], [-21.40890,-90.95721], [-21.51481,-90.91312], [-21.62116,-90.87015], [-21.72792,-90.82831], [-21.83510,-90.78759], [-21.94269,-90.74799], [-22.05068,-90.70950], [-22.15906,-90.67212], [-22.26782,-90.63585], [-22.37696,-90.60069], [-22.48648,-90.56663], [-22.59635,-90.53367], [-22.70658,-90.50181], [-22.81716,-90.47104], [-22.92808,-90.44136], [-23.03933,-90.41278], [-23.15091,-90.38527], [-23.26281,-90.35886], [-23.37501,-90.33352], [-23.48753,-90.30926], [-23.60033,-90.28607], [-23.71343,-90.26396], [-23.82680,-90.24291], [-23.94045,-90.22293], [-24.05437,-90.20401], [-24.16854,-90.18616], [-24.28297,-90.16936], [-24.39764,-90.15362], [-24.51255,-90.13892], [-24.62768,-90.12528], [-24.74304,-90.11268], [-24.85861,-90.10113], [-24.97439,-90.09061], [-25.09037,-90.08114], [-25.20653,-90.07270], [-25.32285,-90.06531], [-25.43931,-90.05897], [-25.55590,-90.05369], [-25.67260,-90.04946], [-25.78938,-90.04629], [-25.90624,-90.04419], [-26.02315,-90.04316], [-26.14009,-90.04320], [-26.25705,-90.04432], [-26.37400,-90.04652], [-26.49093,-90.04980], [-26.60783,-90.05418], [-26.72466,-90.05965], [-26.84142,-90.06621], [-26.95808,-90.07388], [-27.07463,-90.08266], [-27.19104,-90.09254], [-27.30730,-90.10354], [-27.42340,-90.11565], [-27.53931,-90.12889], [-27.65501,-90.14325], [-27.77048,-90.15874], [-27.88572,-90.17537], [-28.00069,-90.19313], [-28.11538,-90.21204], [-28.22978,-90.23209], [-28.34386,-90.25329], [-28.45760,-90.27565], [-28.57099,-90.29916], [-28.68400,-90.32383], [-28.79663,-90.34967], [-28.90885,-90.37669], [-29.02064,-90.40487], [-29.13198,-90.43423], [-29.24286,-90.46478], [-29.35326,-90.49651], [-29.46316,-90.52943], [-29.57254,-90.56354], [-29.68139,-90.59885], [-29.78972,-90.63531], [-29.89755,-90.67290], [-30.00489,-90.71161], [-30.11176,-90.75138], [-30.21816,-90.79221], [-30.32411,-90.83405], [-30.42962,-90.87689], [-30.53471,-90.92068], [-30.63939,-90.96542], [-30.74368,-91.01106], [-30.84757,-91.05757], [-30.95110,-91.10494], [-31.05427,-91.15313], [-31.15710,-91.20211], [-31.25960,-91.25186], [-31.36177,-91.30234], [-31.46365,-91.35353], [-31.56523,-91.40540], [-31.66653,-91.45792], [-31.76757,-91.51107], [-31.86836,-91.56481], [-31.96891,-91.61911], [-32.06924,-91.67396], [-32.16935,-91.72931], [-32.26926,-91.78515], [-32.36899,-91.84144], [-32.46855,-91.89815], [-32.56795,-91.95527], [-32.66720,-92.01274], [-32.76632,-92.07056], [-32.86532,-92.12870], [-32.96421,-92.18711], [-33.06301,-92.24578], [-33.16173,-92.30468], [-33.26039,-92.36377], [-33.35899,-92.42304], [-33.45755,-92.48244], [-33.55609,-92.54196], [-33.65461,-92.60158], [-33.75310,-92.66129], [-33.85158,-92.72110], [-33.95003,-92.78101], [-34.04845,-92.84103], [-34.14684,-92.90114], [-34.24520,-92.96136], [-34.34352,-93.02169], [-34.44181,-93.08213], [-34.54005,-93.14269], [-34.63826,-93.20335], [-34.73641,-93.26414], [-34.83453,-93.32504], [-34.93259,-93.38606], [-35.03060,-93.44720], [-35.12855,-93.50847], [-35.22645,-93.56987], [-35.32429,-93.63139], [-35.42206,-93.69305], [-35.51977,-93.75484], [-35.61742,-93.81676], [-35.71499,-93.87882], [-35.81249,-93.94101], [-35.90992,-94.00335], [-36.00727,-94.06584], [-36.10454,-94.12846], [-36.20173,-94.19124], [-36.29884,-94.25416], [-36.39586,-94.31723], [-36.49279,-94.38046], [-36.58962,-94.44384], [-36.68637,-94.50738], [-36.78301,-94.57108], [-36.87956,-94.63494], [-36.97601,-94.69897], [-37.07235,-94.76316], [-37.16859,-94.82752], [-37.26471,-94.89204], [-37.36073,-94.95674], [-37.45663,-95.02161], [-37.55242,-95.08666], [-37.64808,-95.15189], [-37.74363,-95.21729], [-37.83905,-95.28288], [-37.93435,-95.34865], [-38.02951,-95.41461], [-38.12455,-95.48076], [-38.21945,-95.54709], [-38.31422,-95.61362], [-38.40884,-95.68034], [-38.50333,-95.74726], [-38.59767,-95.81438], [-38.69187,-95.88170], [-38.78592,-95.94922], [-38.87982,-96.01694], [-38.97356,-96.08487], [-39.06715,-96.15301], [-39.16058,-96.22136], [-39.25386,-96.28992], [-39.34696,-96.35870], [-39.43990,-96.42769], [-39.53268,-96.49691], [-39.62528,-96.56634], [-39.71771,-96.63600], [-39.80997,-96.70588], [-39.90204,-96.77599], [-39.99394,-96.84633], [-40.08565,-96.91689], [-40.17718,-96.98770], [-40.26852,-97.05873], [-40.35967,-97.13001], [-40.45063,-97.20152], [-40.54139,-97.27328], [-40.63196,-97.34527], [-40.72232,-97.41752], [-40.81249,-97.49001], [-40.90244,-97.56275], [-40.99219,-97.63574], [-41.08181,-97.70891], [-41.17150,-97.78203], [-41.26149,-97.85486], [-41.35201,-97.92719], [-41.44327,-97.99876], [-41.53549,-98.06934], [-41.62892,-98.13870], [-41.72375,-98.20661], [-41.82015,-98.27255], [-41.91762,-98.33405], [-42.01542,-98.38779], [-42.11281,-98.43043], [-42.20903,-98.45864], [-42.30334,-98.46909], [-42.39502,-98.46032], [-42.48339,-98.43462], [-42.56778,-98.39474], [-42.64752,-98.34339], [-42.72193,-98.28332], [-42.79061,-98.21665], [-42.85376,-98.14397], [-42.91170,-98.06562], [-42.96473,-97.98197], [-43.01316,-97.89337], [-43.05730,-97.80018], [-43.09746,-97.70277], [-43.13394,-97.60147], [-43.16705,-97.49666], [-43.19711,-97.38869], [-43.22442,-97.27791], [-43.24928,-97.16469], [-43.27201,-97.04937], [-43.29291,-96.93232], [-43.31230,-96.81389], [-43.33048,-96.69445], [-43.34776,-96.57434], [-43.36444,-96.45392], [-43.38084,-96.33355], [-43.39726,-96.21359], [-43.41384,-96.09419], [-43.43059,-95.97535], [-43.44751,-95.85704], [-43.46459,-95.73924], [-43.48181,-95.62194], [-43.49919,-95.50512], [-43.51670,-95.38875], [-43.53436,-95.27282], [-43.55214,-95.15730], [-43.57005,-95.04218], [-43.58808,-94.92743], [-43.60622,-94.81303], [-43.62448,-94.69897], [-43.64283,-94.58523], [-43.66129,-94.47178], [-43.67983,-94.35860], [-43.69847,-94.24568], [-43.71719,-94.13299], [-43.73598,-94.02052], [-43.75485,-93.90825], [-43.77378,-93.79614], [-43.79277,-93.68420], [-43.81182,-93.57238], [-43.83091,-93.46068], [-43.85005,-93.34908], [-43.86923,-93.23755], [-43.88844,-93.12607], [-43.90768,-93.01463], [-43.92694,-92.90320], [-43.94622,-92.79177], [-43.96551,-92.68031], [-43.98481,-92.56881], [-44.00410,-92.45724], [-44.02340,-92.34558], [-44.04268,-92.23382], [-44.06194,-92.12194], [-44.08119,-92.00990], [-44.10041,-91.89770], [-44.11959,-91.78532], [-44.13874,-91.67273], [-44.15784,-91.55995], [-44.17689,-91.44697], [-44.19586,-91.33381], [-44.21476,-91.22047], [-44.23357,-91.10695], [-44.25228,-90.99328], [-44.27089,-90.87945], [-44.28937,-90.76547], [-44.30773,-90.65134], [-44.32595,-90.53709], [-44.34402,-90.42270], [-44.36193,-90.30819], [-44.37967,-90.19357], [-44.39723,-90.07884], [-44.41461,-89.96401], [-44.43178,-89.84909], [-44.44875,-89.73409], [-44.46549,-89.61900], [-44.48201,-89.50384], [-44.49829,-89.38862], [-44.51431,-89.27334], [-44.53008,-89.15802], [-44.54558,-89.04264], [-44.56079,-88.92724], [-44.57572,-88.81180], [-44.59034,-88.69634], [-44.60466,-88.58087], [-44.61865,-88.46539], [-44.63231,-88.34991], [-44.64564,-88.23443], [-44.65861,-88.11897], [-44.67122,-88.00353], [-44.68345,-87.88812], [-44.69531,-87.77274], [-44.70677,-87.65740], [-44.71784,-87.54212], [-44.72849,-87.42689], [-44.73872,-87.31172], [-44.74852,-87.19663], [-44.75791,-87.08160], [-44.76698,-86.96664], [-44.77579,-86.85174], [-44.78441,-86.73690], [-44.79293,-86.62211], [-44.80140,-86.50737], [-44.80991,-86.39267], [-44.81854,-86.27800], [-44.82734,-86.16336], [-44.83640,-86.04875], [-44.84579,-85.93415], [-44.85558,-85.81957], [-44.86585,-85.70500], [-44.87667,-85.59043], [-44.88811,-85.47587], [-44.90024,-85.36129], [-44.91315,-85.24670], [-44.92689,-85.13210], [-44.94156,-85.01748], [-44.95720,-84.90282], [-44.97378,-84.78814], [-44.99116,-84.67344], [-45.00922,-84.55871], [-45.02782,-84.44396], [-45.04684,-84.32920], [-45.06615,-84.21442], [-45.08562,-84.09963], [-45.10511,-83.98484], [-45.12451,-83.87003], [-45.14368,-83.75523], [-45.16248,-83.64042], [-45.18080,-83.52562], [-45.19851,-83.41083], [-45.21546,-83.29604], [-45.23154,-83.18126], [-45.24661,-83.06650], [-45.26055,-82.95175], [-45.27323,-82.83703], [-45.28451,-82.72232], [-45.29429,-82.60764], [-45.30257,-82.49299], [-45.30939,-82.37836], [-45.31478,-82.26376], [-45.31877,-82.14918], [-45.32140,-82.03463], [-45.32270,-81.92010], [-45.32272,-81.80561], [-45.32148,-81.69113], [-45.31902,-81.57669], [-45.31538,-81.46227], [-45.31059,-81.34787], [-45.30469,-81.23351], [-45.29770,-81.11917], [-45.28967,-81.00486], [-45.28064,-80.89057], [-45.27063,-80.77632], [-45.25968,-80.66209], [-45.24782,-80.54788], [-45.23510,-80.43371], [-45.22155,-80.31956], [-45.20720,-80.20544], [-45.19208,-80.09135], [-45.17624,-79.97729], [-45.15970,-79.86326], [-45.14251,-79.74925], [-45.12469,-79.63527], [-45.10628,-79.52132], [-45.08733,-79.40741], [-45.06785,-79.29352], [-45.04790,-79.17965], [-45.02749,-79.06582], [-45.00668,-78.95202], [-44.98548,-78.83825], [-44.96395,-78.72450], [-44.94211,-78.61079], [-44.91999,-78.49711], [-44.89765,-78.38345], [-44.87509,-78.26983], [-44.85238,-78.15624], [-44.82952,-78.04268], [-44.80651,-77.92915], [-44.78335,-77.81566], [-44.76002,-77.70221], [-44.73652,-77.58881], [-44.71283,-77.47546], [-44.68895,-77.36216], [-44.66486,-77.24892], [-44.64056,-77.13574], [-44.61603,-77.02263], [-44.59126,-76.90958], [-44.56625,-76.79660], [-44.54099,-76.68370], [-44.51546,-76.57088], [-44.48966,-76.45815], [-44.46357,-76.34550], [-44.43719,-76.23294], [-44.41050,-76.12047], [-44.38351,-76.00811], [-44.35618,-75.89584], [-44.32853,-75.78368], [-44.30053,-75.67163], [-44.27218,-75.55970], [-44.24346,-75.44788], [-44.21437,-75.33618], [-44.18490,-75.22461], [-44.15504,-75.11316], [-44.12477,-75.00184], [-44.09409,-74.89067], [-44.06299,-74.77963], [-44.03146,-74.66873], [-43.99949,-74.55798], [-43.96706,-74.44738], [-43.93417,-74.33694], [-43.90081,-74.22665], [-43.86697,-74.11653], [-43.83264,-74.00657], [-43.79781,-73.89678], [-43.76247,-73.78716], [-43.72661,-73.67772], [-43.69024,-73.56845], [-43.65335,-73.45937], [-43.61596,-73.35046], [-43.57806,-73.24173], [-43.53966,-73.13318], [-43.50076,-73.02481], [-43.46137,-72.91662], [-43.42147,-72.80861], [-43.38109,-72.70079], [-43.34021,-72.59315], [-43.29885,-72.48570], [-43.25700,-72.37843], [-43.21467,-72.27135], [-43.17186,-72.16446], [-43.12857,-72.05775], [-43.08481,-71.95124], [-43.04057,-71.84491], [-42.99587,-71.73878], [-42.95070,-71.63284], [-42.90507,-71.52709], [-42.85897,-71.42153], [-42.81242,-71.31617], [-42.76541,-71.21100], [-42.71795,-71.10603], [-42.67004,-71.00126], [-42.62167,-70.89668], [-42.57286,-70.79231], [-42.52361,-70.68813], [-42.47392,-70.58415], [-42.42379,-70.48037], [-42.37323,-70.37680], [-42.32223,-70.27343], [-42.27080,-70.17026], [-42.21894,-70.06730], [-42.16666,-69.96454], [-42.11396,-69.86199], [-42.06084,-69.75965], [-42.00730,-69.65751], [-41.95334,-69.55558], [-41.89898,-69.45386], [-41.84420,-69.35236], [-41.78902,-69.25106], [-41.73343,-69.14998], [-41.67744,-69.04911], [-41.62106,-68.94845], [-41.56427,-68.84801], [-41.50710,-68.74778], [-41.44953,-68.64777], [-41.39157,-68.54798], [-41.33323,-68.44841], [-41.27450,-68.34905], [-41.21540,-68.24992], [-41.15591,-68.15100], [-41.09605,-68.05231], [-41.03582,-67.95384], [-40.97521,-67.85559], [-40.91424,-67.75757], [-40.85291,-67.65977], [-40.79121,-67.56220], [-40.72915,-67.46485], [-40.66673,-67.36773], [-40.60396,-67.27084], [-40.54084,-67.17418], [-40.47737,-67.07775], [-40.41355,-66.98155], [-40.34939,-66.88558], [-40.28488,-66.78985], [-40.22004,-66.69435], [-40.15486,-66.59908], [-40.08934,-66.50405], [-40.02350,-66.40925], [-39.95732,-66.31469], [-39.89082,-66.22037], [-39.82400,-66.12629], [-39.75685,-66.03244], [-39.68939,-65.93884], [-39.62161,-65.84548], [-39.55352,-65.75235], [-39.48511,-65.65947], [-39.41640,-65.56682], [-39.34737,-65.47441], [-39.27804,-65.38224], [-39.20841,-65.29030], [-39.13847,-65.19860], [-39.06823,-65.10713], [-38.99769,-65.01590], [-38.92685,-64.92489], [-38.85571,-64.83412], [-38.78428,-64.74358], [-38.71256,-64.65327], [-38.64055,-64.56318], [-38.56825,-64.47333], [-38.49566,-64.38370], [-38.42278,-64.29429], [-38.34963,-64.20511], [-38.27619,-64.11616], [-38.20247,-64.02743], [-38.12847,-63.93892], [-38.05419,-63.85063], [-37.97965,-63.76257], [-37.90482,-63.67472], [-37.82973,-63.58709], [-37.75437,-63.49969], [-37.67874,-63.41249], [-37.60284,-63.32552], [-37.52669,-63.23876], [-37.45026,-63.15222], [-37.37358,-63.06588], [-37.29664,-62.97977], [-37.21945,-62.89386], [-37.14199,-62.80817], [-37.06429,-62.72268], [-36.98633,-62.63741], [-36.90813,-62.55234], [-36.82967,-62.46748], [-36.75098,-62.38283], [-36.67203,-62.29839], [-36.59285,-62.21415], [-36.51342,-62.13011], [-36.43375,-62.04628], [-36.35385,-61.96265], [-36.27372,-61.87922], [-36.19334,-61.79600], [-36.11274,-61.71297], [-36.03191,-61.63014], [-35.95085,-61.54752], [-35.86956,-61.46508], [-35.78805,-61.38285], [-35.70632,-61.30081], [-35.62436,-61.21897], [-35.54219,-61.13731], [-35.45980,-61.05586], [-35.37719,-60.97459], [-35.29437,-60.89352], [-35.21134,-60.81264], [-35.12810,-60.73194], [-35.04465,-60.65144], [-34.96099,-60.57112], [-34.87713,-60.49099], [-34.79307,-60.41105], [-34.70880,-60.33129], [-34.62433,-60.25172], [-34.53967,-60.17233], [-34.45481,-60.09312], [-34.36976,-60.01409], [-34.28452,-59.93525], [-34.19908,-59.85658], [-34.11346,-59.77810], [-34.02765,-59.69979], [-33.94165,-59.62166], [-33.85547,-59.54371], [-33.76911,-59.46594], [-33.68257,-59.38833], [-33.59586,-59.31091], [-33.50896,-59.23365], [-33.42189,-59.15657], [-33.33465,-59.07966], [-33.24724,-59.00293], [-33.15965,-58.92638], [-33.07190,-58.85000], [-32.98397,-58.77381], [-32.89588,-58.69779], [-32.80762,-58.62196], [-32.71919,-58.54631], [-32.63060,-58.47084], [-32.54184,-58.39556], [-32.45292,-58.32047], [-32.36384,-58.24557], [-32.27460,-58.17086], [-32.18519,-58.09633], [-32.09563,-58.02201], [-32.00591,-57.94787], [-31.91603,-57.87393], [-31.82600,-57.80019], [-31.73581,-57.72665], [-31.64547,-57.65330], [-31.55497,-57.58016], [-31.46432,-57.50721], [-31.37352,-57.43447], [-31.28257,-57.36194], [-31.19147,-57.28961], [-31.10023,-57.21749], [-31.00883,-57.14558], [-30.91729,-57.07388], [-30.82561,-57.00239], [-30.73378,-56.93111], [-30.64181,-56.86004], [-30.54970,-56.78919], [-30.45745,-56.71856], [-30.36505,-56.64815], [-30.27252,-56.57795], [-30.17985,-56.50797], [-30.08704,-56.43822], [-29.99410,-56.36869], [-29.90102,-56.29939], [-29.80781,-56.23031], [-29.71447,-56.16145], [-29.62099,-56.09283], [-29.52739,-56.02443], [-29.43365,-55.95627], [-29.33979,-55.88834], [-29.24580,-55.82064], [-29.15168,-55.75318], [-29.05744,-55.68596], [-28.96307,-55.61897], [-28.86858,-55.55222], [-28.77396,-55.48571], [-28.67923,-55.41944], [-28.58437,-55.35342], [-28.48940,-55.28764], [-28.39430,-55.22211], [-28.29909,-55.15682], [-28.20376,-55.09178], [-28.10832,-55.02699], [-28.01276,-54.96246], [-27.91709,-54.89817],
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
