kuato781/spirit-wave-stand/stl-scad/stand/SpiritWave-RED-RAISED.scad

module red_raised_2d() {
  union() {
    polygon(points=[[-44.55184,-98.22127], [-44.53260,-98.29275], [-44.51286,-98.36372], [-44.49251,-98.43404], [-44.47145,-98.50357], [-44.44958,-98.57219], [-44.42679,-98.63975], [-44.40298,-98.70613], [-44.37805,-98.77118], [-44.35189,-98.83478], [-44.32440,-98.89678], [-44.29548,-98.95706], [-44.26503,-99.01552], [-44.23298,-99.07232], [-44.19929,-99.12768], [-44.16388,-99.18184], [-44.12670,-99.23502], [-44.08770,-99.28746], [-44.04682,-99.33938], [-44.00400,-99.39103], [-43.95918,-99.44262], [-43.91232,-99.49439], [-43.86334,-99.54657], [-43.81223,-99.59928], [-43.75908,-99.65230], [-43.70401,-99.70531], [-43.64711,-99.75803], [-43.58851,-99.81015], [-43.52832,-99.86136], [-43.46665,-99.91137], [-43.40362,-99.95987], [-43.33933,-100.00657], [-43.27391,-100.05115], [-43.20745,-100.09332], [-43.14008,-100.13278], [-43.07192,-100.16922], [-43.00306,-100.20234], [-42.93362,-100.23185], [-42.86372,-100.25743], [-42.79347,-100.27879], [-42.72299,-100.29563], [-42.65238,-100.30764], [-42.58174,-100.31460], [-42.51113,-100.31667], [-42.44059,-100.31410], [-42.37014,-100.30715], [-42.29983,-100.29607], [-42.22968,-100.28111], [-42.15975,-100.26253], [-42.09006,-100.24059], [-42.02065,-100.21554], [-41.95155,-100.18763], [-41.88280,-100.15712], [-41.81444,-100.12426], [-41.74651,-100.08931], [-41.67903,-100.05253], [-41.61205,-100.01416], [-41.54560,-99.97447], [-41.47972,-99.93370], [-41.41444,-99.89212], [-41.34980,-99.84997], [-41.28584,-99.80750], [-41.22253,-99.76483], [-41.15984,-99.72195], [-41.09772,-99.67888], [-41.03612,-99.63561], [-40.97499,-99.59215], [-40.91429,-99.54851], [-40.85396,-99.50469], [-40.79397,-99.46068], [-40.73426,-99.41651], [-40.67479,-99.37216], [-40.61551,-99.32764], [-40.55637,-99.28297], [-40.49733,-99.23813], [-40.43834,-99.19314], [-40.37935,-99.14800], [-40.32031,-99.10272], [-40.26119,-99.05729], [-40.20192,-99.01172], [-40.14246,-98.96601], [-40.08278,-98.92018], [-40.02288,-98.87422], [-39.96275,-98.82815], [-39.90242,-98.78197], [-39.84188,-98.73569], [-39.78116,-98.68931], [-39.72026,-98.64286], [-39.65920,-98.59633], [-39.59797,-98.54973], [-39.53660,-98.50307], [-39.47508,-98.45635], [-39.41344,-98.40960], [-39.35168,-98.36280], [-39.28982,-98.31598], [-39.22785,-98.26914], [-39.16580,-98.22229], [-39.10366,-98.17543], [-39.04146,-98.12857], [-38.97920,-98.08173], [-38.91689,-98.03490], [-38.85454,-97.98810], [-38.79216,-97.94134], [-38.72977,-97.89462], [-38.66736,-97.84795], [-38.60496,-97.80134], [-38.54256,-97.75480], [-38.48019,-97.70833], [-38.41785,-97.66194], [-38.35555,-97.61564], [-38.29330,-97.56944], [-38.23111,-97.52335], [-38.16899,-97.47737], [-38.10696,-97.43152], [-38.04501,-97.38579], [-37.98317,-97.34021], [-37.92143,-97.29476], [-37.85982,-97.24948], [-37.79833,-97.20435], [-37.73698,-97.15939], [-37.67576,-97.11460], [-37.61465,-97.06997], [-37.55364,-97.02549], [-37.49272,-96.98117], [-37.43188,-96.93700], [-37.37109,-96.89298], [-37.31036,-96.84910], [-37.24966,-96.80537], [-37.18900,-96.76177], [-37.12834,-96.71830], [-37.06768,-96.67496], [-37.00701,-96.63175], [-36.94632,-96.58867], [-36.88558,-96.54570], [-36.82480,-96.50285], [-36.76396,-96.46011], [-36.70304,-96.41748], [-36.64203,-96.37495], [-36.58092,-96.33253], [-36.51970,-96.29020], [-36.45835,-96.24797], [-36.39686,-96.20584], [-36.33523,-96.16379], [-36.27343,-96.12182], [-36.21145,-96.07994], [-36.14929,-96.03813], [-36.08693,-95.99640], [-36.02435,-95.95473], [-35.96154,-95.91314], [-35.89850,-95.87160], [-35.83521,-95.83013], [-35.77165,-95.78872], [-35.70781,-95.74735], [-35.64369,-95.70604], [-35.57927,-95.66477], [-35.51453,-95.62355], [-35.44946,-95.58236], [-35.38406,-95.54121], [-35.31833,-95.50010], [-35.25232,-95.45903], [-35.18604,-95.41803], [-35.11954,-95.37709], [-35.05285,-95.33623], [-34.98601,-95.29545], [-34.91904,-95.25477], [-34.85198,-95.21419], [-34.78486,-95.17372], [-34.71773,-95.13337], [-34.65061,-95.09316], [-34.58353,-95.05308], [-34.51653,-95.01316], [-34.44964,-94.97339], [-34.38290,-94.93379], [-34.31634,-94.89437], [-34.25000,-94.85513], [-34.18390,-94.81608], [-34.11808,-94.77724], [-34.05254,-94.73858], [-33.98726,-94.70007], [-33.92224,-94.66168], [-33.85745,-94.62337], [-33.79289,-94.58512], [-33.72854,-94.54689], [-33.66439,-94.50864], [-33.60042,-94.47036], [-33.53663,-94.43200], [-33.47299,-94.39354], [-33.40949,-94.35494], [-33.34613,-94.31617], [-33.28288,-94.27720], [-33.21974,-94.23799], [-33.15669,-94.19852], [-33.09371,-94.15875], [-33.03080,-94.11865], [-32.96794,-94.07819], [-32.90511,-94.03734], [-32.84230,-93.99612], [-32.77950,-93.95459], [-32.71669,-93.91279], [-32.65386,-93.87079], [-32.59098,-93.82864], [-32.52805,-93.78640], [-32.46504,-93.74413], [-32.40195,-93.70187], [-32.33875,-93.65969], [-32.27543,-93.61764], [-32.21197,-93.57578], [-32.14837,-93.53417], [-32.08459,-93.49285], [-32.02064,-93.45189], [-31.95648,-93.41134], [-31.89211,-93.37126], [-31.82751,-93.33170], [-31.76267,-93.29272], [-31.69756,-93.25437], [-31.63220,-93.21665], [-31.56658,-93.17954], [-31.50072,-93.14298], [-31.43462,-93.10697], [-31.36830,-93.07144], [-31.30177,-93.03638], [-31.23504,-93.00175], [-31.16811,-92.96752], [-31.10099,-92.93364], [-31.03370,-92.90009], [-30.96624,-92.86683], [-30.89862,-92.83383], [-30.83086,-92.80106], [-30.76296,-92.76847], [-30.69493,-92.73604], [-30.62678,-92.70373], [-30.55852,-92.67151], [-30.49016,-92.63934], [-30.42171,-92.60719], [-30.35317,-92.57504], [-30.28453,-92.54293], [-30.21580,-92.51086], [-30.14695,-92.47887], [-30.07799,-92.44699], [-30.00891,-92.41522], [-29.93969,-92.38361], [-29.87033,-92.35217], [-29.80082,-92.32092], [-29.73116,-92.28990], [-29.66134,-92.25912], [-29.59135,-92.22861], [-29.52119,-92.19839], [-29.45083,-92.16849], [-29.38029,-92.13893], [-29.30955,-92.10974], [-29.23860,-92.08094], [-29.16744,-92.05255], [-29.09605,-92.02460], [-29.02444,-91.99711], [-28.95259,-91.97010], [-28.88049,-91.94361], [-28.80814,-91.91765], [-28.73554,-91.89225], [-28.66267,-91.86743], [-28.58952,-91.84322], [-28.51609,-91.81964], [-28.44238,-91.79672], [-28.36836,-91.77447], [-28.29405,-91.75293], [-28.21942,-91.73211], [-28.14447,-91.71205], [-28.06920,-91.69276], [-27.99359,-91.67427], [-27.91764,-91.65660], [-27.84135,-91.63978], [-27.76469,-91.62383], [-27.68768,-91.60878], [-27.61029,-91.59465], [-27.53256,-91.58142], [-27.45448,-91.56909], [-27.37610,-91.55764], [-27.29741,-91.54707], [-27.21845,-91.53737], [-27.13922,-91.52851], [-27.05974,-91.52050], [-26.98004,-91.51333], [-26.90013,-91.50697], [-26.82004,-91.50143], [-26.73976,-91.49668], [-26.65934,-91.49272], [-26.57877,-91.48954], [-26.49809,-91.48712], [-26.41731,-91.48547], [-26.33644,-91.48455], [-26.25551,-91.48437], [-26.17453,-91.48491], [-26.09353,-91.48617], [-26.01251,-91.48813], [-25.93150,-91.49077], [-25.85052,-91.49410], [-25.76957,-91.49809], [-25.68869,-91.50274], [-25.60789,-91.50804], [-25.52718,-91.51398], [-25.44659,-91.52054], [-25.36614,-91.52771], [-25.28583,-91.53549], [-25.20569,-91.54386], [-25.12574,-91.55281], [-25.04600,-91.56233], [-24.96647,-91.57241], [-24.88719,-91.58304], [-24.80817,-91.59421], [-24.72942,-91.60590], [-24.65097,-91.61811], [-24.57283,-91.63083], [-24.49502,-91.64404], [-24.41755,-91.65774], [-24.34041,-91.67192], [-24.26360,-91.68658], [-24.18711,-91.70173], [-24.11094,-91.71736], [-24.03507,-91.73346], [-23.95952,-91.75003], [-23.88426,-91.76708], [-23.80931,-91.78460], [-23.73464,-91.80258], [-23.66026,-91.82104], [-23.58615,-91.83995], [-23.51233,-91.85932], [-23.43877,-91.87916], [-23.36547,-91.89945], [-23.29244,-91.92019], [-23.21966,-91.94138], [-23.14712,-91.96303], [-23.07483,-91.98512], [-23.00278,-92.00766], [-22.93096,-92.03064], [-22.85937,-92.05407], [-22.78800,-92.07793], [-22.71685,-92.10223], [-22.64591,-92.12696], [-22.57518,-92.15212], [-22.50465,-92.17772], [-22.43431,-92.20374], [-22.36416,-92.23019], [-22.29420,-92.25706], [-22.22442,-92.28435], [-22.15482,-92.31206], [-22.08538,-92.34019], [-22.01611,-92.36873], [-21.94700,-92.39768], [-21.87804,-92.42704], [-21.80923,-92.45682], [-21.74057,-92.48699], [-21.67204,-92.51757], [-21.60366,-92.54857], [-21.53544,-92.58000], [-21.46740,-92.61189], [-21.39957,-92.64428], [-21.33198,-92.67719], [-21.26463,-92.71066], [-21.19756,-92.74469], [-21.13079,-92.77934], [-21.06434,-92.81462], [-20.99823,-92.85056], [-20.93248,-92.88718], [-20.86712,-92.92453], [-20.80217,-92.96262], [-20.73765,-93.00148], [-20.67359,-93.04115], [-20.61000,-93.08164], [-20.54691,-93.12299], [-20.48433,-93.16522], [-20.42231,-93.20837], [-20.36082,-93.25242], [-20.29983,-93.29731], [-20.23929,-93.34295], [-20.17914,-93.38928], [-20.11935,-93.43621], [-20.05985,-93.48366], [-20.00060,-93.53157], [-19.94154,-93.57983], [-19.88264,-93.62839], [-19.82383,-93.67716], [-19.76508,-93.72607], [-19.70632,-93.77503], [-19.64750,-93.82397], [-19.58859,-93.87281], [-19.52953,-93.92147], [-19.47026,-93.96987], [-19.41074,-94.01794], [-19.35093,-94.06560], [-19.29076,-94.11277], [-19.23019,-94.15938], [-19.16924,-94.20544], [-19.10792,-94.25096], [-19.04625,-94.29598], [-18.98424,-94.34050], [-18.92191,-94.38456], [-18.85929,-94.42816], [-18.79637,-94.47135], [-18.73320,-94.51412], [-18.66977,-94.55652], [-18.60612,-94.59855], [-18.54225,-94.64024], [-18.47819,-94.68162], [-18.41395,-94.72269], [-18.34954,-94.76349], [-18.28500,-94.80403], [-18.22033,-94.84434], [-18.15555,-94.88444], [-18.09069,-94.92434], [-18.02575,-94.96408], [-17.96075,-95.00367], [-17.89572,-95.04313], [-17.83067,-95.08248], [-17.76561,-95.12175], [-17.70057,-95.16096], [-17.63556,-95.20012], [-17.57061,-95.23927], [-17.50572,-95.27841], [-17.44091,-95.31758], [-17.37621,-95.35679], [-17.31163,-95.39607], [-17.24718,-95.43543], [-17.18290,-95.47490], [-17.11878,-95.51450], [-17.05486,-95.55425], [-16.99114,-95.59418], [-16.92765,-95.63429], [-16.86440,-95.67462], [-16.80141,-95.71518], [-16.73867,-95.75597], [-16.67615,-95.79695], [-16.61383,-95.83810], [-16.55168,-95.87939], [-16.48968,-95.92080], [-16.42781,-95.96230], [-16.36604,-96.00386], [-16.30435,-96.04546], [-16.24271,-96.08707], [-16.18110,-96.12866], [-16.11950,-96.17021], [-16.05787,-96.21169], [-15.99620,-96.25307], [-15.93446,-96.29434], [-15.87263,-96.33545], [-15.81067,-96.37639], [-15.74858,-96.41712], [-15.68632,-96.45763], [-15.62387,-96.49788], [-15.56121,-96.53786], [-15.49835,-96.57757], [-15.43528,-96.61701], [-15.37200,-96.65618], [-15.30851,-96.69507], [-15.24480,-96.73369], [-15.18088,-96.77203], [-15.11675,-96.81011], [-15.05240,-96.84790], [-14.98783,-96.88542], [-14.92305,-96.92266], [-14.85804,-96.95963], [-14.79281,-96.99632], [-14.72736,-97.03273], [-14.66168,-97.06886], [-14.59578,-97.10471], [-14.52966,-97.14029], [-14.46330,-97.17558], [-14.39671,-97.21059], [-14.32990,-97.24533], [-14.26287,-97.27980], [-14.19564,-97.31402], [-14.12821,-97.34800], [-14.06059,-97.38176], [-13.99281,-97.41531], [-13.92486,-97.44865], [-13.85676,-97.48182], [-13.78852,-97.51481], [-13.72016,-97.54764], [-13.65167,-97.58033], [-13.58308,-97.61289], [-13.51440,-97.64533], [-13.44563,-97.67766], [-13.37678,-97.70990], [-13.30787,-97.74207], [-13.23892,-97.77417], [-13.16992,-97.80621], [-13.10089,-97.83822], [-13.03184,-97.87020], [-12.96279,-97.90217], [-12.89374,-97.93414], [-12.82470,-97.96613], [-12.75569,-97.99814], [-12.68672,-98.03020], [-12.61780,-98.06230], [-12.54893,-98.09448], [-12.48013,-98.12674], [-12.41141,-98.15909], [-12.34279,-98.19155], [-12.27427,-98.22412], [-12.20586,-98.25684], [-12.13758,-98.28970], [-12.06943,-98.32272], [-12.00143,-98.35591], [-11.93358,-98.38929], [-11.86591,-98.42288], [-11.79841,-98.45667], [-11.73110,-98.49068], [-11.66394,-98.52487], [-11.59689,-98.55918], [-11.52992,-98.59356], [-11.46299,-98.62797], [-11.39606,-98.66237], [-11.32910,-98.69669], [-11.26206,-98.73089], [-11.19492,-98.76493], [-11.12764,-98.79875], [-11.06017,-98.83230], [-10.99249,-98.86554], [-10.92454,-98.89841], [-10.85631,-98.93088], [-10.78775,-98.96288], [-10.71882,-98.99437], [-10.64949,-99.02531], [-10.57971,-99.05564], [-10.50946,-99.08531], [-10.43871,-99.11429], [-10.36747,-99.14259], [-10.29579,-99.17024], [-10.22367,-99.19727], [-10.15116,-99.22370], [-10.07828,-99.24956], [-10.00507,-99.27488], [-9.93155,-99.29967], [-9.85775,-99.32398], [-9.78370,-99.34781], [-9.70942,-99.37121], [-9.63496,-99.39420], [-9.56034,-99.41679], [-9.48558,-99.43903], [-9.41071,-99.46093], [-9.33577,-99.48253], [-9.26079,-99.50384], [-9.18579,-99.52489], [-9.11080,-99.54572], [-9.03587,-99.56637], [-8.96116,-99.58703], [-8.88691,-99.60798], [-8.81333,-99.62949], [-8.74066,-99.65183], [-8.66912,-99.67527], [-8.59893,-99.70009], [-8.53033,-99.72655], [-8.46352,-99.75491], [-8.39843,-99.78512], [-8.33474,-99.81681], [-8.27210,-99.84965], [-8.21018,-99.88325], [-8.14863,-99.91728], [-8.08712,-99.95137], [-8.02531,-99.98515], [-7.96286,-100.01828], [-7.89943,-100.05040], [-7.83467,-100.08114], [-7.76828,-100.11015], [-7.70016,-100.13737], [-7.63045,-100.16291], [-7.55928,-100.18692], [-7.48680,-100.20953], [-7.41314,-100.23090], [-7.33844,-100.25115], [-7.26284,-100.27044], [-7.18648,-100.28890], [-7.10949,-100.30667], [-7.03202,-100.32389], [-6.95419,-100.34071], [-6.87616,-100.35726], [-6.79806,-100.37368], [-6.72002,-100.39012], [-6.64219,-100.40672], [-6.56470,-100.42362], [-6.48769,-100.44095], [-6.41130,-100.45886], [-6.33567,-100.47749], [-6.26090,-100.49695], [-6.18696,-100.51719], [-6.11379,-100.53815], [-6.04131,-100.55974], [-5.96945,-100.58190], [-5.89816,-100.60455], [-5.82736,-100.62761], [-5.75699,-100.65102], [-5.68698,-100.67469], [-5.61725,-100.69855], [-5.54776,-100.72254], [-5.47841,-100.74657], [-5.40916,-100.77057], [-5.33993,-100.79447], [-5.27065,-100.81819], [-5.20126,-100.84166], [-5.13169,-100.86480], [-5.06188,-100.88754], [-4.99175,-100.90981], [-4.92124,-100.93153], [-4.85032,-100.95268], [-4.77903,-100.97329], [-4.70735,-100.99336], [-4.63532,-101.01293], [-4.56294,-101.03200], [-4.49022,-101.05060], [-4.41718,-101.06875], [-4.34384,-101.08646], [-4.27020,-101.10375], [-4.19629,-101.12065], [-4.12211,-101.13717], [-4.04767,-101.15332], [-3.97299,-101.16914], [-3.89809,-101.18464], [-3.82298,-101.19983], [-3.74767,-101.21474], [-3.67217,-101.22939], [-3.59650,-101.24379], [-3.52067,-101.25796], [-3.44470,-101.27192], [-3.36860,-101.28570], [-3.29238,-101.29930], [-3.21605,-101.31275], [-3.13961,-101.32604], [-3.06306,-101.33917], [-2.98641,-101.35214], [-2.90966,-101.36496], [-2.83281,-101.37763], [-2.75586,-101.39013], [-2.67880,-101.40249], [-2.60165,-101.41468], [-2.52441,-101.42673], [-2.44706,-101.43861], [-2.36963,-101.45035], [-2.29210,-101.46193], [-2.21448,-101.47336], [-2.13677,-101.48463], [-2.05897,-101.49576], [-1.98109,-101.50673], [-1.90312,-101.51754], [-1.82506,-101.52821], [-1.74693,-101.53873], [-1.66871,-101.54909], [-1.59041,-101.55931], [-1.51203,-101.56937], [-1.43357,-101.57929], [-1.35504,-101.58905], [-1.27643,-101.59867], [-1.19775,-101.60814], [-1.11900,-101.61746], [-1.04017,-101.62663], [-0.96128,-101.63566], [-0.88232,-101.64453], [-0.80329,-101.65326], [-0.72419,-101.66185], [-0.64504,-101.67028], [-0.56581,-101.67857], [-0.48653,-101.68672], [-0.40719,-101.69472], [-0.32778,-101.70258], [-0.24832,-101.71029], [-0.16881,-101.71785], [-0.08924,-101.72528], [-0.00961,-101.73256], [0.07006,-101.73969], [0.14979,-101.74669], [0.22957,-101.75354], [0.30939,-101.76025], [0.38926,-101.76681], [0.46918,-101.77324], [0.54914,-101.77953], [0.62915,-101.78567], [0.70919,-101.79167], [0.78928,-101.79754], [0.86940,-101.80326], [0.94957,-101.80885], [1.02976,-101.81429], [1.11000,-101.81960], [1.19026,-101.82477], [1.27056,-101.82980], [1.35089,-101.83469], [1.43125,-101.83945], [1.51163,-101.84407], [1.59205,-101.84855], [1.67249,-101.85289], [1.75295,-101.85710], [1.83343,-101.86118], [1.91394,-101.86512], [1.99447,-101.86892], [2.07501,-101.87259], [2.15557,-101.87613], [2.23615,-101.87953], [2.31674,-101.88280], [2.39735,-101.88593], [2.47797,-101.88894], [2.55860,-101.89181], [2.63923,-101.89454], [2.71988,-101.89715], [2.80053,-101.89963], [2.88119,-101.90197], [2.96185,-101.90418], [3.04252,-101.90627], [3.12318,-101.90822], [3.20385,-101.91004], [3.28452,-101.91173], [3.36519,-101.91329], [3.44586,-101.91473], [3.52652,-101.91603], [3.60719,-101.91720], [3.68785,-101.91824], [3.76852,-101.91915], [3.84917,-101.91993], [3.92983,-101.92059], [4.01048,-101.92111], [4.09112,-101.92150], [4.17176,-101.92177], [4.25240,-101.92190], [4.33302,-101.92191], [4.41364,-101.92178], [4.49425,-101.92153], [4.57486,-101.92115], [4.65545,-101.92064], [4.73604,-101.91999], [4.81661,-101.91922], [4.89717,-101.91833], [4.97773,-101.91730], [5.05827,-101.91614], [5.13879,-101.91486], [5.21931,-101.91344], [5.29981,-101.91190], [5.38030,-101.91023], [5.46077,-101.90843], [5.54122,-101.90650], [5.62166,-101.90445], [5.70209,-101.90226], [5.78249,-101.89995], [5.86288,-101.89751], [5.94325,-101.89494], [6.02360,-101.89225], [6.10394,-101.88942], [6.18425,-101.88647], [6.26454,-101.88339], [6.34481,-101.88018], [6.42505,-101.87684], [6.50528,-101.87338], [6.58548,-101.86979], [6.66566,-101.86607], [6.74581,-101.86223], [6.82594,-101.85825], [6.90605,-101.85415], [6.98612,-101.84992], [7.06618,-101.84557], [7.14620,-101.84109], [7.22620,-101.83648], [7.30617,-101.83174], [7.38610,-101.82688], [7.46601,-101.82189], [7.54589,-101.81677], [7.62574,-101.81153], [7.70556,-101.80616], [7.78535,-101.80066], [7.86510,-101.79504], [7.94482,-101.78929], [8.02451,-101.78342], [8.10416,-101.77741], [8.18378,-101.77129], [8.26336,-101.76503], [8.34291,-101.75865], [8.42242,-101.75214], [8.50189,-101.74551], [8.58133,-101.73875], [8.66073,-101.73187], [8.74009,-101.72486], [8.81941,-101.71772], [8.89869,-101.71046], [8.97793,-101.70307], [9.05712,-101.69556], [9.13628,-101.68792], [9.21539,-101.68016], [9.29446,-101.67227], [9.37349,-101.66425], [9.45247,-101.65611], [9.53141,-101.64784], [9.61029,-101.63944], [9.68913,-101.63090], [9.76790,-101.62222], [9.84662,-101.61339], [9.92527,-101.60442], [10.00386,-101.59529], [10.08237,-101.58600], [10.16082,-101.57656], [10.23919,-101.56695], [10.31748,-101.55717], [10.39569,-101.54721], [10.47382,-101.53709], [10.55185,-101.52678], [10.62980,-101.51628], [10.70766,-101.50560], [10.78541,-101.49473], [10.86307,-101.48366], [10.94062,-101.47238], [11.01807,-101.46091], [11.09541,-101.44923], [11.17263,-101.43733], [11.24974,-101.42522], [11.32673,-101.41289], [11.40360,-101.40033], [11.48034,-101.38755], [11.55696,-101.37453], [11.63344,-101.36128], [11.70979,-101.34779], [11.78601,-101.33406], [11.86208,-101.32008], [11.93801,-101.30585], [12.01379,-101.29136], [12.08942,-101.27661], [12.16490,-101.26160], [12.24022,-101.24632], [12.31539,-101.23077], [12.39039,-101.21495], [12.46522,-101.19884], [12.53989,-101.18246], [12.61438,-101.16579], [12.68869,-101.14883], [12.76282,-101.13157], [12.83675,-101.11402], [12.91050,-101.09617], [12.98404,-101.07802], [13.05737,-101.05956], [13.13050,-101.04080], [13.20340,-101.02172], [13.27609,-101.00232], [13.34856,-100.98260], [13.42079,-100.96257], [13.49278,-100.94220], [13.56454,-100.92151], [13.63605,-100.90048], [13.70731,-100.87911], [13.77831,-100.85741], [13.84905,-100.83536], [13.91955,-100.81300], [13.98985,-100.79037], [14.06000,-100.76754], [14.13006,-100.74458], [14.20007,-100.72155], [14.27009,-100.69852], [14.34017,-100.67554], [14.41037,-100.65268], [14.48072,-100.63002], [14.55128,-100.60760], [14.62211,-100.58549], [14.69325,-100.56377], [14.76476,-100.54248], [14.83669,-100.52170], [14.90908,-100.50149], [14.98200,-100.48192], [15.05548,-100.46304], [15.12959,-100.44493], [15.20437,-100.42763], [15.27987,-100.41123], [15.35606,-100.39568], [15.43288,-100.38088], [15.51022,-100.36673], [15.58800,-100.35312], [15.66614,-100.33995], [15.74456,-100.32711], [15.82316,-100.31449], [15.90186,-100.30200], [15.98059,-100.28952], [16.05924,-100.27695], [16.13774,-100.26418], [16.21600,-100.25111], [16.29394,-100.23763], [16.37147,-100.22364], [16.44851,-100.20903], [16.52497,-100.19369], [16.60076,-100.17753], [16.67580,-100.16043], [16.75001,-100.14229], [16.82334,-100.12306], [16.89585,-100.10280], [16.96761,-100.08160], [17.03870,-100.05956], [17.10919,-100.03677], [17.17916,-100.01332], [17.24869,-99.98930], [17.31784,-99.96480], [17.38670,-99.93992], [17.45534,-99.91474], [17.52383,-99.88936], [17.59225,-99.86387], [17.66068,-99.83835], [17.72919,-99.81291], [17.79785,-99.78762], [17.86674,-99.76259], [17.93594,-99.73791], [18.00552,-99.71366], [18.07555,-99.68993], [18.14611,-99.66682], [18.21719,-99.64432], [18.28877,-99.62241], [18.36082,-99.60105], [18.43332,-99.58022], [18.50623,-99.55989], [18.57954,-99.54003], [18.65320,-99.52061], [18.72721,-99.50161], [18.80152,-99.48298], [18.87612,-99.46470], [18.95098,-99.44675], [19.02606,-99.42910], [19.10134,-99.41170], [19.17680,-99.39455], [19.25240,-99.37760], [19.32813,-99.36083], [19.40395,-99.34420], [19.47983,-99.32769], [19.55576,-99.31128], [19.63169,-99.29492], [19.70762,-99.27860], [19.78350,-99.26227], [19.85931,-99.24592], [19.93503,-99.22952], [20.01062,-99.21303], [20.08606,-99.19642], [20.16133,-99.17967], [20.23639,-99.16274], [20.31122,-99.14561], [20.38580,-99.12826], [20.46009,-99.11063], [20.53407,-99.09272], [20.60770,-99.07449], [20.68098,-99.05592], [20.75386,-99.03696], [20.82632,-99.01759], [20.89833,-98.99779], [20.96987,-98.97753], [21.04091,-98.95677], [21.11148,-98.93554], [21.18162,-98.91387], [21.25139,-98.89179], [21.32082,-98.86935], [21.38997,-98.84658], [21.45889,-98.82350], [21.52761,-98.80017], [21.59620,-98.77662], [21.66469,-98.75287], [21.73313,-98.72897], [21.80158,-98.70496], [21.87007,-98.68087], [21.93866,-98.65673], [22.00740,-98.63258], [22.07632,-98.60846], [22.14548,-98.58441], [22.21493,-98.56045], [22.28471,-98.53663], [22.35487,-98.51297], [22.42544,-98.48951], [22.49639,-98.46623], [22.56770,-98.44310], [22.63933,-98.42009], [22.71126,-98.39720], [22.78346,-98.37438], [22.85589,-98.35163], [22.92853,-98.32892], [23.00134,-98.30623], [23.07431,-98.28353], [23.14739,-98.26079], [23.22055,-98.23801], [23.29378,-98.21515], [23.36703,-98.19220], [23.44028,-98.16913], [23.51350,-98.14591], [23.58666,-98.12253], [23.65972,-98.09896], [23.73267,-98.07518], [23.80546,-98.05117], [23.87809,-98.02691], [23.95055,-98.00242], [24.02286,-97.97769], [24.09501,-97.95274], [24.16700,-97.92756], [24.23885,-97.90216], [24.31055,-97.87655], [24.38210,-97.85073], [24.45351,-97.82470], [24.52478,-97.79847], [24.59592,-97.77205], [24.66693,-97.74544], [24.73781,-97.71864], [24.80856,-97.69167], [24.87919,-97.66452], [24.94970,-97.63719], [25.02009,-97.60971], [25.09037,-97.58206], [25.16054,-97.55425], [25.23061,-97.52629], [25.30057,-97.49819], [25.37043,-97.46995], [25.44019,-97.44157], [25.50986,-97.41306], [25.57943,-97.38442], [25.64892,-97.35566], [25.71832,-97.32678], [25.78764,-97.29779], [25.85689,-97.26869], [25.92605,-97.23949], [25.99515,-97.21019], [26.06417,-97.18080], [26.13313,-97.15132], [26.20202,-97.12176], [26.27086,-97.09212], [26.33963,-97.06241], [26.40836,-97.03263], [26.47703,-97.00278], [26.54565,-96.97288], [26.61423,-96.94291], [26.68275,-96.91287], [26.75123,-96.88277], [26.81966,-96.85260], [26.88804,-96.82236], [26.95637,-96.79205], [27.02465,-96.76166], [27.09288,-96.73119], [27.16106,-96.70064], [27.22919,-96.67001], [27.29726,-96.63929], [27.36529,-96.60848], [27.43326,-96.57759], [27.50119,-96.54660], [27.56906,-96.51552], [27.63688,-96.48434], [27.70464,-96.45306], [27.77236,-96.42169], [27.84002,-96.39020], [27.90763,-96.35862], [27.97518,-96.32692], [28.04268,-96.29512], [28.11013,-96.26320], [28.17753,-96.23116], [28.24486,-96.19901], [28.31215,-96.16674], [28.37938,-96.13435], [28.44655,-96.10183], [28.51367,-96.06919], [28.58074,-96.03642], [28.64775,-96.00352], [28.71470,-95.97048], [28.78160,-95.93731], [28.84844,-95.90400], [28.91522,-95.87055], [28.98195,-95.83696], [29.04861,-95.80322], [29.11523,-95.76934], [29.18178,-95.73531], [29.24827,-95.70113], [29.31471,-95.66681], [29.38108,-95.63234], [29.44739,-95.59772], [29.51364,-95.56296], [29.57983,-95.52805], [29.64595,-95.49300], [29.71200,-95.45781], [29.77798,-95.42248], [29.84390,-95.38701], [29.90975,-95.35139], [29.97553,-95.31563], [30.04123,-95.27974], [30.10687,-95.24370], [30.17243,-95.20753], [30.23791,-95.17122], [30.30332,-95.13477], [30.36866,-95.09819], [30.43391,-95.06147], [30.49909,-95.02462], [30.56419,-94.98763], [30.62921,-94.95051], [30.69415,-94.91325], [30.75900,-94.87587], [30.82377,-94.83835], [30.88846,-94.80070], [30.95306,-94.76292], [31.01757,-94.72501], [31.08199,-94.68697], [31.14633,-94.64880], [31.21058,-94.61050], [31.27473,-94.57208], [31.33880,-94.53353], [31.40277,-94.49485], [31.46665,-94.45605], [31.53043,-94.41712], [31.59412,-94.37808], [31.65770,-94.33890], [31.72120,-94.29961], [31.78459,-94.26019], [31.84789,-94.22064], [31.91109,-94.18098], [31.97420,-94.14119], [32.03720,-94.10129], [32.10011,-94.06126], [32.16292,-94.02110], [32.22564,-93.98083], [32.28825,-93.94044], [32.35077,-93.89992], [32.41319,-93.85929], [32.47552,-93.81854], [32.53774,-93.77766], [32.59987,-93.73667], [32.66190,-93.69555], [32.72383,-93.65432], [32.78566,-93.61297], [32.84739,-93.57150], [32.90903,-93.52991], [32.97056,-93.48820], [33.03200,-93.44637], [33.09334,-93.40443], [33.15458,-93.36237], [33.21572,-93.32019], [33.27676,-93.27790], [33.33770,-93.23549], [33.39855,-93.19296], [33.45929,-93.15031], [33.51994,-93.10755], [33.58048,-93.06468], [33.64093,-93.02168], [33.70128,-92.97858], [33.76153,-92.93535], [33.82167,-92.89202], [33.88172,-92.84857], [33.94167,-92.80500], [34.00152,-92.76132], [34.06127,-92.71752], [34.12092,-92.67361], [34.18049,-92.62956], [34.23997,-92.58538], [34.29937,-92.54105], [34.35870,-92.49657], [34.41797,-92.45193], [34.47717,-92.40712], [34.53632,-92.36213], [34.59542,-92.31697], [34.65447,-92.27160], [34.71349,-92.22604], [34.77247,-92.18027], [34.83142,-92.13429], [34.89035,-92.08808], [34.94927,-92.04164], [35.00817,-91.99497], [35.06707,-91.94804], [35.12596,-91.90086], [35.18487,-91.85342], [35.24378,-91.80572], [35.30269,-91.75777], [35.36160,-91.70958], [35.42050,-91.66117], [35.47938,-91.61255], [35.53824,-91.56374], [35.59708,-91.51474], [35.65589,-91.46557], [35.71466,-91.41625], [35.77339,-91.36678], [35.83208,-91.31719], [35.89071,-91.26747], [35.94928,-91.21766], [36.00779,-91.16775], [36.06623,-91.11776], [36.12460,-91.06772], [36.18289,-91.01762], [36.24109,-90.96749], [36.29921,-90.91733], [36.35722,-90.86716], [36.41514,-90.81697], [36.47295,-90.76676], [36.53065,-90.71652], [36.58823,-90.66623], [36.64568,-90.61589], [36.70301,-90.56548], [36.76021,-90.51500], [36.81727,-90.46443], [36.87418,-90.41377], [36.93095,-90.36300], [36.98756,-90.31212], [37.04401,-90.26111], [37.10029,-90.20996], [37.15640,-90.15867], [37.21234,-90.10722], [37.26809,-90.05561], [37.32366,-90.00382], [37.37903,-89.95184], [37.43421,-89.89967], [37.48918,-89.84729], [37.54395,-89.79469], [37.59850,-89.74187], [37.65283,-89.68880], [37.70694,-89.63549], [37.76081,-89.58192], [37.81445,-89.52809], [37.86785,-89.47398], [37.92101,-89.41957], [37.97391,-89.36487], [38.02655,-89.30987], [38.07894,-89.25454], [38.13105,-89.19888], [38.18289,-89.14289], [38.23445,-89.08654], [38.28573,-89.02984], [38.33672,-88.97277], [38.38741,-88.91532], [38.43781,-88.85748], [38.48790,-88.79924], [38.53773,-88.74066], [38.58731,-88.68178], [38.63669,-88.62264], [38.68589,-88.56329], [38.73495,-88.50378], [38.78391,-88.44416], [38.83279,-88.38448], [38.88163,-88.32478], [38.93046,-88.26511], [38.97931,-88.20553], [39.02821,-88.14607], [39.07721,-88.08678], [39.12633,-88.02772], [39.17560,-87.96893], [39.22506,-87.91046], [39.27474,-87.85235], [39.32467,-87.79466], [39.37489,-87.73744], [39.42542,-87.68071], [39.47624,-87.62445], [39.52729,-87.56861], [39.57852,-87.51313], [39.62989,-87.45795], [39.68135,-87.40301], [39.73284,-87.34825], [39.78432,-87.29362], [39.83574,-87.23906], [39.88705,-87.18450], [39.93819,-87.12991], [39.98913,-87.07521], [40.03980,-87.02034], [40.09017,-86.96526], [40.14017,-86.90990], [40.18977,-86.85421], [40.23890,-86.79812], [40.28753,-86.74159], [40.33560,-86.68454], [40.38306,-86.62694], [40.42987,-86.56870], [40.47597,-86.50979], [40.52131,-86.45015], [40.56590,-86.38975], [40.60976,-86.32865], [40.65297,-86.26691], [40.69557,-86.20458], [40.73761,-86.14172], [40.77915,-86.07838], [40.82025,-86.01462], [40.86095,-85.95048], [40.90131,-85.88604], [40.94138,-85.82134], [40.98121,-85.75643], [41.02087,-85.69137], [41.06039,-85.62623], [41.09984,-85.56104], [41.13927,-85.49587], [41.17872,-85.43078], [41.21827,-85.36581], [41.25795,-85.30102], [41.29782,-85.23648], [41.33792,-85.17221], [41.37825,-85.10821], [41.41877,-85.04445], [41.45947,-84.98090], [41.50032,-84.91753], [41.54129,-84.85430], [41.58236,-84.79119], [41.62350,-84.72817], [41.66468,-84.66520], [41.70589,-84.60226], [41.74709,-84.53932], [41.78826,-84.47634], [41.82938,-84.41330], [41.87041,-84.35017], [41.91134,-84.28691], [41.95214,-84.22349], [41.99278,-84.15989], [42.03324,-84.09607], [42.07349,-84.03201], [42.11351,-83.96768], [42.15330,-83.90308], [42.19288,-83.83822], [42.23224,-83.77313], [42.27141,-83.70781], [42.31039,-83.64227], [42.34918,-83.57654], [42.38780,-83.51063], [42.42626,-83.44454], [42.46456,-83.37829], [42.50272,-83.31190], [42.54074,-83.24538], [42.57863,-83.17874], [42.61641,-83.11199], [42.65407,-83.04516], [42.69164,-82.97825], [42.72912,-82.91127], [42.76651,-82.84425], [42.80384,-82.77719], [42.84110,-82.71010], [42.87830,-82.64301], [42.91546,-82.57592], [42.95259,-82.50886], [42.98968,-82.44182], [43.02676,-82.37483], [43.06384,-82.30790], [43.10091,-82.24104], [43.13799,-82.17426], [43.17509,-82.10759], [43.21222,-82.04103], [43.24939,-81.97459], [43.28660,-81.90830], [43.32386,-81.84216], [43.36120,-81.77619], [43.39860,-81.71040], [43.43609,-81.64480], [43.47367,-81.57941], [43.51135,-81.51425], [43.54912,-81.44930], [43.58692,-81.38451], [43.62467,-81.31983], [43.66231,-81.25518], [43.69976,-81.19052], [43.73697,-81.12578], [43.77384,-81.06090], [43.81032,-80.99581], [43.84634,-80.93047], [43.88183,-80.86480], [43.91670,-80.79875], [43.95091,-80.73226], [43.98437,-80.66527], [44.01701,-80.59771], [44.04877,-80.52952], [44.07957,-80.46066], [44.10935,-80.39104], [44.13803,-80.32062], [44.16554,-80.24933], [44.19188,-80.17717], [44.21713,-80.10420], [44.24141,-80.03053], [44.26483,-79.95624], [44.28751,-79.88144], [44.30955,-79.80620], [44.33106,-79.73062], [44.35216,-79.65481], [44.37296,-79.57883], [44.39357,-79.50280], [44.41410,-79.42680], [44.43467,-79.35093], [44.45538,-79.27528], [44.47635,-79.19993], [44.49768,-79.12499], [44.51950,-79.05054], [44.54190,-78.97667], [44.56501,-78.90349], [44.58893,-78.83108], [44.61376,-78.75951], [44.63943,-78.68875], [44.66590,-78.61872], [44.69306,-78.54935], [44.72085,-78.48059], [44.74918,-78.41235], [44.77799,-78.34457], [44.80719,-78.27718], [44.83671,-78.21011], [44.86646,-78.14330], [44.89637,-78.07667], [44.92637,-78.01015], [44.95637,-77.94368], [44.98629,-77.87719], [45.01607,-77.81060], [45.04562,-77.74386], [45.07487,-77.67689], [45.10373,-77.60961], [45.13213,-77.54197], [45.16000,-77.47390], [45.18730,-77.40536], [45.21402,-77.33636], [45.24016,-77.26690], [45.26571,-77.19698], [45.29068,-77.12659], [45.31506,-77.05574], [45.33884,-76.98443], [45.36203,-76.91266], [45.38460,-76.84042], [45.40658,-76.76773], [45.42794,-76.69458], [45.44868,-76.62097], [45.46881,-76.54689], [45.48831,-76.47236], [45.50719,-76.39738], [45.52543,-76.32193], [45.54304,-76.24603], [45.56001,-76.16967], [45.57634,-76.09285], [45.59203,-76.01559], [45.60714,-75.93795], [45.62173,-75.85997], [45.63586,-75.78173], [45.64958,-75.70328], [45.66295,-75.62470], [45.67603,-75.54603], [45.68889,-75.46733], [45.70157,-75.38868], [45.71415,-75.31014], [45.72667,-75.23175], [45.73920,-75.15359], [45.75179,-75.07572], [45.76451,-74.99819], [45.77741,-74.92107], [45.79055,-74.84443], [45.80399,-74.76831], [45.81779,-74.69279], [45.83201,-74.61792], [45.84670,-74.54377], [45.86190,-74.47034], [45.87757,-74.39758], [45.89371,-74.32542], [45.91027,-74.25382], [45.92725,-74.18271], [45.94462,-74.11203], [45.96235,-74.04173], [45.98043,-73.97173], [45.99882,-73.90199], [46.01746,-73.83242], [46.03624,-73.76296], [46.05509,-73.69353], [46.07390,-73.62406], [46.09259,-73.55446], [46.11107,-73.48467], [46.12924,-73.41461], [46.14701,-73.34419], [46.16429,-73.27336], [46.18099,-73.20202], [46.19703,-73.13013], [46.21241,-73.05766], [46.22713,-72.98465], [46.24122,-72.91110], [46.25468,-72.83704], [46.26754,-72.76248], [46.27982,-72.68743], [46.29151,-72.61192], [46.30266,-72.53597], [46.31326,-72.45958], [46.32333,-72.38278], [46.33290,-72.30558], [46.34197,-72.22800], [46.35056,-72.15006], [46.35869,-72.07177], [46.36637,-71.99316], [46.37362,-71.91423], [46.38046,-71.83501], [46.38690,-71.75551], [46.39295,-71.67575], [46.39863,-71.59575], [46.40397,-71.51551], [46.40897,-71.43507], [46.41364,-71.35444], [46.41802,-71.27363], [46.42210,-71.19266], [46.42591,-71.11156], [46.42946,-71.03032], [46.43278,-70.94898], [46.43586,-70.86755], [46.43874,-70.78605], [46.44142,-70.70448], [46.44393,-70.62288], [46.44627,-70.54126], [46.44846,-70.45963], [46.45053,-70.37801], [46.45248,-70.29642], [46.45433,-70.21488], [46.45609,-70.13340], [46.45779,-70.05200], [46.45944,-69.97069], [46.46102,-69.88947], [46.46254,-69.80833], [46.46400,-69.72728], [46.46540,-69.64630], [46.46672,-69.56538], [46.46796,-69.48454], [46.46913,-69.40375], [46.47022,-69.32302], [46.47122,-69.24233], [46.47214,-69.16170], [46.47296,-69.08110], [46.47369,-69.00054], [46.47432,-68.92001], [46.47485,-68.83950], [46.47527,-68.75902], [46.47559,-68.67855], [46.47579,-68.59809], [46.47588,-68.51764], [46.47585,-68.43719], [46.47570,-68.35674], [46.47542,-68.27627], [46.47501,-68.19580], [46.47447,-68.11530], [46.47380,-68.03478], [46.47299,-67.95424], [46.47203,-67.87366], [46.47093,-67.79304], [46.46968,-67.71238], [46.46828,-67.63167], [46.46672,-67.55091], [46.46500,-67.47010], [46.46312,-67.38922], [46.46107,-67.30827], [46.45885,-67.22725], [46.45646,-67.14615], [46.45390,-67.06497], [46.45115,-66.98371], [46.44822,-66.90235], [46.44511,-66.82090], [46.44180,-66.73935], [46.43827,-66.65774], [46.43450,-66.57611], [46.43046,-66.49449], [46.42613,-66.41293], [46.42147,-66.33147], [46.41645,-66.25014], [46.41106,-66.16899], [46.40526,-66.08805], [46.39903,-66.00737], [46.39234,-65.92698], [46.38517,-65.84692], [46.37748,-65.76724], [46.36925,-65.68797], [46.36046,-65.60915], [46.35107,-65.53082], [46.34106,-65.45302], [46.33040,-65.37580], [46.31907,-65.29918], [46.30703,-65.22322], [46.29430,-65.14791], [46.28090,-65.07322], [46.26689,-64.99911], [46.25231,-64.92553], [46.23721,-64.85244], [46.22164,-64.77979], [46.20563,-64.70756], [46.18923,-64.63568], [46.17250,-64.56412], [46.15547,-64.49283], [46.13819,-64.42178], [46.12070,-64.35091], [46.10306,-64.28020], [46.08531,-64.20958], [46.06749,-64.13902], [46.04964,-64.06848], [46.03182,-63.99791], [46.01408,-63.92728], [45.99644,-63.85653], [45.97896,-63.78563], [45.96165,-63.71454], [45.94452,-63.64326], [45.92757,-63.57176], [45.91080,-63.50002], [45.89421,-63.42802], [45.87783,-63.35573], [45.86164,-63.28314], [45.84565,-63.21023], [45.82987,-63.13697], [45.81431,-63.06335], [45.79896,-62.98934], [45.78383,-62.91493], [45.76893,-62.84009], [45.75427,-62.76480], [45.73984,-62.68904], [45.72565,-62.61280], [45.71170,-62.53604], [45.69801,-62.45875], [45.68457,-62.38092], [45.67138,-62.30252], [45.65837,-62.22365], [45.64545,-62.14440], [45.63255,-62.06486], [45.61959,-61.98512], [45.60647,-61.90527], [45.59313,-61.82542], [45.57947,-61.74566], [45.56542,-61.66608], [45.55089,-61.58677], [45.53581,-61.50783], [45.52009,-61.42936], [45.50364,-61.35144], [45.48639,-61.27418], [45.46826,-61.19766], [45.44916,-61.12198], [45.42901,-61.04724], [45.40773,-60.97352], [45.38524,-60.90093], [45.36145,-60.82955], [45.33640,-60.75937], [45.31021,-60.69027], [45.28299,-60.62213], [45.25488,-60.55483], [45.22601,-60.48824], [45.19649,-60.42225], [45.16645,-60.35672], [45.13602,-60.29155], [45.10533,-60.22661], [45.07449,-60.16178], [45.04364,-60.09693], [45.01291,-60.03195], [44.98241,-59.96671], [44.95228,-59.90109], [44.92263,-59.83497], [44.89360,-59.76822], [44.86531,-59.70074], [44.83788,-59.63238], [44.81145,-59.56305], [44.78603,-59.49269], [44.76151,-59.42141], [44.73777,-59.34930], [44.71469,-59.27646], [44.69214,-59.20300], [44.67000,-59.12900], [44.64814,-59.05458], [44.62645,-58.97983], [44.60481,-58.90485], [44.58307,-58.82974], [44.56114,-58.75461], [44.53887,-58.67954], [44.51615,-58.60464], [44.49286,-58.53001], [44.46887,-58.45575], [44.44407,-58.38195], [44.41831,-58.30873], [44.39149,-58.23617], [44.36349,-58.16439], [44.33419,-58.09345], [44.30364,-58.02334], [44.27192,-57.95401], [44.23914,-57.88539], [44.20537,-57.81743], [44.17071,-57.75006], [44.13524,-57.68324], [44.09906,-57.61691], [44.06225,-57.55099], [44.02491,-57.48545], [43.98713,-57.42021], [43.94898,-57.35523], [43.91058,-57.29044], [43.87199,-57.22579], [43.83332,-57.16121], [43.79466,-57.09665], [43.75608,-57.03206], [43.71769,-56.96737], [43.67957,-56.90252], [43.64180,-56.83747], [43.60437,-56.77222], [43.56725,-56.70680], [43.53040,-56.64122], [43.49378,-56.57551], [43.45736,-56.50969], [43.42109,-56.44379], [43.38495,-56.37783], [43.34888,-56.31183], [43.31287,-56.24582], [43.27686,-56.17983], [43.24083,-56.11386], [43.20473,-56.04796], [43.16853,-55.98213], [43.13219,-55.91641], [43.09567,-55.85082], [43.05894,-55.78538], [43.02196,-55.72012], [42.98469,-55.65505], [42.94710,-55.59020], [42.90918,-55.52559], [42.87093,-55.46119], [42.83235,-55.39700], [42.79346,-55.33303], [42.75426,-55.26926], [42.71476,-55.20568], [42.67496,-55.14230], [42.63487,-55.07910], [42.59449,-55.01608], [42.55383,-54.95324], [42.51289,-54.89056], [42.47169,-54.82805], [42.43022,-54.76570], [42.38850,-54.70349], [42.34652,-54.64143], [42.30430,-54.57951], [42.26184,-54.51772], [42.21915,-54.45606], [42.17623,-54.39452], [42.13309,-54.33310], [42.08973,-54.27179], [42.04616,-54.21058], [42.00239,-54.14948], [41.95842,-54.08846], [41.91426,-54.02753], [41.86991,-53.96669], [41.82538,-53.90591], [41.78068,-53.84521], [41.73580,-53.78457], [41.69077,-53.72400], [41.64558,-53.66347], [41.60024,-53.60299], [41.55475,-53.54255], [41.50912,-53.48214], [41.46336,-53.42176], [41.41747,-53.36141], [41.37146,-53.30108], [41.32534,-53.24075], [41.27910,-53.18044], [41.23274,-53.12013], [41.18626,-53.05985], [41.13965,-52.99959], [41.09290,-52.93937], [41.04601,-52.87918], [40.99896,-52.81905], [40.95175,-52.75896], [40.90436,-52.69894], [40.85681,-52.63899], [40.80907,-52.57911], [40.76113,-52.51932], [40.71300,-52.45961], [40.66466,-52.40000], [40.61611,-52.34049], [40.56734,-52.28110], [40.51834,-52.22182], [40.46910,-52.16266], [40.41962,-52.10364], [40.36989,-52.04475], [40.31990,-51.98601], [40.26965,-51.92742], [40.21912,-51.86899], [40.16831,-51.81072], [40.11721,-51.75263], [40.06582,-51.69472], [40.01413,-51.63699], [39.96212,-51.57946], [39.90980,-51.52213], [39.85715,-51.46501], [39.80417,-51.40810], [39.75085,-51.35141], [39.69718,-51.29495], [39.64315,-51.23873], [39.58877,-51.18275], [39.53401,-51.12702], [39.47888,-51.07155], [39.42336,-51.01634], [39.36745,-50.96140], [39.31117,-50.90673], [39.25454,-50.85232], [39.19762,-50.79816], [39.14044,-50.74424], [39.08303,-50.69056], [39.02543,-50.63710], [38.96769,-50.58386], [38.90983,-50.53083], [38.85189,-50.47801], [38.79392,-50.42537], [38.73595,-50.37291], [38.67801,-50.32063], [38.62015,-50.26852], [38.56240,-50.21656], [38.50480,-50.16475], [38.44739,-50.11308], [38.39021,-50.06155], [38.33328,-50.01013], [38.27665,-49.95883], [38.22035,-49.90764], [38.16432,-49.85655], [38.10855,-49.80557], [38.05300,-49.75468], [37.99762,-49.70389], [37.94238,-49.65319], [37.88725,-49.60258], [37.83218,-49.55206], [37.77715,-49.50162], [37.72211,-49.45127], [37.66704,-49.40099], [37.61189,-49.35079], [37.55662,-49.30067], [37.50120,-49.25062], [37.44560,-49.20063], [37.38977,-49.15072], [37.33369,-49.10086], [37.27731,-49.05107], [37.22060,-49.00133], [37.16352,-48.95165], [37.10607,-48.90202], [37.04826,-48.85246], [36.99011,-48.80295], [36.93163,-48.75352], [36.87283,-48.70416], [36.81374,-48.65487], [36.75437,-48.60566], [36.69473,-48.55654], [36.63483,-48.50750], [36.57471,-48.45855], [36.51436,-48.40970], [36.45380,-48.36095], [36.39306,-48.31229], [36.33214,-48.26375], [36.27106,-48.21532], [36.20983,-48.16700], [36.14848,-48.11879], [36.08701,-48.07071], [36.02545,-48.02276], [35.96380,-47.97494], [35.90209,-47.92724], [35.84032,-47.87969], [35.77852,-47.83228], [35.71669,-47.78501], [35.65486,-47.73789], [35.59304,-47.69093], [35.53124,-47.64412], [35.46948,-47.59747], [35.40778,-47.55099], [35.34615,-47.50468], [35.28460,-47.45853], [35.22316,-47.41257], [35.16183,-47.36678], [35.10063,-47.32118], [35.03958,-47.27577], [34.97869,-47.23054], [34.91798,-47.18552], [34.85746,-47.14069], [34.79714,-47.09606], [34.73697,-47.05163], [34.67692,-47.00738], [34.61695,-46.96332], [34.55702,-46.91944], [34.49709,-46.87572], [34.43713,-46.83217], [34.37710,-46.78878], [34.31696,-46.74554], [34.25666,-46.70244], [34.19618,-46.65949], [34.13548,-46.61666], [34.07450,-46.57397], [34.01323,-46.53140], [33.95162,-46.48894], [33.88962,-46.44659], [33.82721,-46.40434], [33.76434,-46.36219], [33.70098,-46.32014], [33.63716,-46.27813], [33.57326,-46.23598], [33.50972,-46.19346], [33.44699,-46.15035], [33.38553,-46.10641], [33.32578,-46.06142], [33.26821,-46.01515], [33.21325,-45.96737], [33.16137,-45.91785], [33.11301,-45.86636], [33.06863,-45.81269], [33.02864,-45.75661], [32.99305,-45.69812], [32.96168,-45.63732], [32.93433,-45.57434], [32.91080,-45.50926], [32.89089,-45.44221], [32.87440,-45.37328], [32.86113,-45.30259], [32.85089,-45.23024], [32.84348,-45.15634], [32.83870,-45.08100], [32.83636,-45.00432], [32.83628,-44.92644], [32.83833,-44.84749], [32.84238,-44.76762], [32.84828,-44.68698], [32.85590,-44.60570], [32.86511,-44.52394], [32.87577,-44.44184], [32.88773,-44.35953], [32.90087,-44.27717], [32.91505,-44.19491], [32.93013,-44.11287], [32.94598,-44.03122], [32.96245,-43.95009], [32.97941,-43.86962], [32.99673,-43.78997], [33.01427,-43.71127], [33.03189,-43.63367], [33.04945,-43.55732], [33.06683,-43.48235], [33.08390,-43.40889], [33.10069,-43.33681], [33.11732,-43.26593], [33.13386,-43.19604], [33.15042,-43.12696], [33.16710,-43.05847], [33.18398,-42.99039], [33.20117,-42.92251], [33.21876,-42.85464], [33.23678,-42.78663], [33.25515,-42.71844], [33.27380,-42.65004], [33.29263,-42.58137], [33.31155,-42.51241], [33.33048,-42.44312], [33.34933,-42.37346], [33.36801,-42.30339], [33.38645,-42.23287], [33.40454,-42.16187], [33.42220,-42.09035], [33.43938,-42.01829], [33.45609,-41.94570], [33.47233,-41.87260], [33.48812,-41.79901], [33.50347,-41.72494], [33.51839,-41.65042], [33.53289,-41.57545], [33.54699,-41.50006], [33.56070,-41.42427], [33.57403,-41.34809], [33.58699,-41.27153], [33.59960,-41.19462], [33.61186,-41.11738], [33.62379,-41.03982], [33.63540,-40.96195], [33.64671,-40.88380], [33.65772,-40.80539], [33.66844,-40.72672], [33.67890,-40.64782], [33.68909,-40.56871], [33.69904,-40.48940], [33.70875,-40.40990], [33.71824,-40.33025], [33.72752,-40.25045], [33.73660,-40.17052], [33.74550,-40.09048], [33.75422,-40.01035], [33.76278,-39.93014], [33.77118,-39.84987], [33.77945,-39.76956], [33.78760,-39.68923], [33.79563,-39.60888], [33.80355,-39.52855], [33.81139,-39.44825], [33.81915,-39.36799], [33.82684,-39.28780], [33.83448,-39.20768], [33.84208,-39.12766], [33.84965,-39.04776], [33.85720,-38.96799], [33.86478,-38.88837], [33.87242,-38.80892], [33.88018,-38.72966], [33.88809,-38.65061], [33.89621,-38.57178], [33.90457,-38.49321], [33.91322,-38.41490], [33.92221,-38.33688], [33.93159,-38.25917], [33.94138,-38.18178], [33.95166,-38.10473], [33.96244,-38.02806], [33.97379,-37.95176], [33.98575,-37.87587], [33.99835,-37.80040], [34.01166,-37.72537], [34.02570,-37.65081], [34.04053,-37.57672], [34.05620,-37.50314], [34.07270,-37.43006], [34.08992,-37.35746], [34.10773,-37.28529], [34.12599,-37.21351], [34.14457,-37.14208], [34.16331,-37.07096], [34.18209,-37.00010], [34.20077,-36.92947], [34.21921,-36.85902], [34.23734,-36.78871], [34.25514,-36.71847], [34.27263,-36.64824], [34.28977,-36.57798], [34.30659,-36.50762], [34.32306,-36.43711], [34.33918,-36.36638], [34.35495,-36.29537], [34.37035,-36.22404], [34.38540,-36.15232], [34.40007,-36.08016], [34.41437,-36.00753], [34.42832,-35.93445], [34.44192,-35.86094], [34.45517,-35.78700], [34.46810,-35.71267], [34.48071,-35.63793], [34.49301,-35.56283], [34.50500,-35.48736], [34.51671,-35.41154], [34.52813,-35.33539], [34.53928,-35.25892], [34.55017,-35.18215], [34.56080,-35.10508], [34.57119,-35.02774], [34.58135,-34.95014], [34.59128,-34.87230], [34.60100,-34.79422], [34.61051,-34.71592], [34.61982,-34.63743], [34.62895,-34.55874], [34.63790,-34.47988], [34.64669,-34.40087], [34.65531,-34.32170], [34.66379,-34.24241], [34.67213,-34.16300], [34.68034,-34.08350], [34.68843,-34.00390], [34.69641,-33.92423], [34.70429,-33.84451], [34.71208,-33.76474], [34.71978,-33.68495], [34.72742,-33.60514], [34.73499,-33.52533], [34.74251,-33.44554], [34.74999,-33.36578], [34.75743,-33.28606], [34.76485,-33.20640], [34.77225,-33.12682], [34.77965,-33.04732], [34.78705,-32.96792], [34.79446,-32.88862], [34.80187,-32.80942], [34.80928,-32.73030], [34.81668,-32.65127], [34.82409,-32.57232], [34.83150,-32.49344], [34.83890,-32.41464], [34.84629,-32.33590], [34.85368,-32.25722], [34.86106,-32.17860], [34.86843,-32.10003], [34.87578,-32.02151], [34.88313,-31.94303], [34.89046,-31.86459], [34.89778,-31.78618], [34.90508,-31.70780], [34.91236,-31.62944], [34.91962,-31.55110], [34.92687,-31.47278], [34.93409,-31.39446], [34.94129,-31.31615], [34.94846,-31.23784], [34.95561,-31.15952], [34.96273,-31.08120], [34.96982,-31.00286], [34.97688,-30.92450], [34.98392,-30.84612], [34.99091,-30.76770], [34.99788,-30.68926], [35.00481,-30.61078], [35.01170,-30.53226], [35.01856,-30.45369], [35.02537,-30.37506], [35.03215,-30.29638], [35.03888,-30.21764], [35.04557,-30.13884], [35.05221,-30.05996], [35.05881,-29.98101], [35.06536,-29.90197], [35.07187,-29.82286], [35.07832,-29.74366], [35.08472,-29.66438], [35.09106,-29.58502], [35.09735,-29.50559], [35.10357,-29.42608], [35.10973,-29.34650], [35.11583,-29.26685], [35.12186,-29.18714], [35.12782,-29.10735], [35.13371,-29.02751], [35.13952,-28.94761], [35.14526,-28.86764], [35.15092,-28.78762], [35.15650,-28.70755], [35.16199,-28.62743], [35.16740,-28.54725], [35.17272,-28.46703], [35.17795,-28.38676], [35.18308,-28.30645], [35.18812,-28.22610], [35.19307,-28.14571], [35.19791,-28.06528], [35.20265,-27.98482], [35.20729,-27.90432], [35.21182,-27.82380], [35.21624,-27.74325], [35.22056,-27.66267], [35.22475,-27.58206], [35.22883,-27.50144], [35.23279,-27.42080], [35.23664,-27.34014], [35.24036,-27.25946], [35.24395,-27.17878], [35.24741,-27.09808], [35.25075,-27.01737], [35.25395,-26.93666], [35.25702,-26.85594], [35.25995,-26.77523], [35.26275,-26.69451], [35.26540,-26.61379], [35.26791,-26.53308], [35.27028,-26.45237], [35.27251,-26.37166], [35.27460,-26.29096], [35.27655,-26.21026], [35.27835,-26.12956], [35.28002,-26.04887], [35.28155,-25.96818], [35.28294,-25.88750], [35.28418,-25.80682], [35.28529,-25.72615], [35.28625,-25.64549], [35.28708,-25.56483], [35.28777,-25.48417], [35.28831,-25.40353], [35.28872,-25.32289], [35.28899,-25.24226], [35.28911,-25.16164], [35.28910,-25.08102], [35.28895,-25.00042], [35.28866,-24.91982], [35.28823,-24.83923], [35.28766,-24.75865], [35.28695,-24.67809], [35.28610,-24.59753], [35.28511,-24.51698], [35.28399,-24.43644], [35.28272,-24.35592], [35.28132,-24.27540], [35.27978,-24.19490], [35.27810,-24.11441], [35.27628,-24.03393], [35.27432,-23.95346], [35.27222,-23.87301], [35.26999,-23.79257], [35.26762,-23.71215], [35.26510,-23.63174], [35.26245,-23.55134], [35.25967,-23.47096], [35.25674,-23.39059], [35.25368,-23.31024], [35.25048,-23.22990], [35.24714,-23.14958], [35.24366,-23.06928], [35.24005,-22.98899], [35.23629,-22.90872], [35.23240,-22.82846], [35.22838,-22.74823], [35.22421,-22.66801], [35.21991,-22.58781], [35.21547,-22.50763], [35.21090,-22.42747], [35.20619,-22.34732], [35.20134,-22.26720], [35.19635,-22.18709], [35.19123,-22.10701], [35.18597,-22.02695], [35.18057,-21.94690], [35.17504,-21.86688], [35.16937,-21.78688], [35.16356,-21.70690], [35.15762,-21.62695], [35.15154,-21.54701], [35.14532,-21.46710], [35.13897,-21.38721], [35.13249,-21.30735], [35.12586,-21.22751], [35.11910,-21.14769], [35.11221,-21.06790], [35.10518,-20.98813], [35.09801,-20.90839], [35.09071,-20.82867], [35.08327,-20.74898], [35.07570,-20.66931], [35.06799,-20.58967], [35.06015,-20.51006], [35.05217,-20.43047], [35.04406,-20.35091], [35.03581,-20.27138], [35.02742,-20.19188], [35.01888,-20.11242], [35.01019,-20.03301], [35.00134,-19.95366], [34.99230,-19.87438], [34.98309,-19.79518], [34.97368,-19.71606], [34.96408,-19.63705], [34.95426,-19.55814], [34.94422,-19.47935], [34.93396,-19.40069], [34.92345,-19.32216], [34.91270,-19.24378], [34.90170,-19.16556], [34.89043,-19.08750], [34.87889,-19.00961], [34.86706,-18.93191], [34.85494,-18.85441], [34.84253,-18.77710], [34.82980,-18.70001], [34.81675,-18.62314], [34.80338,-18.54651], [34.78967,-18.47011], [34.77562,-18.39397], [34.76121,-18.31809], [34.74644,-18.24248], [34.73129,-18.16714], [34.71576,-18.09210], [34.69984,-18.01736], [34.68353,-17.94292], [34.66680,-17.86881], [34.64966,-17.79502], [34.63209,-17.72157], [34.61408,-17.64846], [34.59563,-17.57572], [34.57672,-17.50333], [34.55736,-17.43133], [34.53752,-17.35971], [34.51720,-17.28848], [34.49639,-17.21765], [34.47514,-17.14718], [34.45348,-17.07700], [34.43146,-17.00708], [34.40912,-16.93735], [34.38650,-16.86777], [34.36365,-16.79827], [34.34061,-16.72881], [34.31742,-16.65934], [34.29413,-16.58980], [34.27078,-16.52014], [34.24741,-16.45030], [34.22407,-16.38023], [34.20080,-16.30989], [34.17764,-16.23921], [34.15464,-16.16814], [34.13183,-16.09664], [34.10927,-16.02464], [34.08699,-15.95210], [34.06504,-15.87896], [34.04339,-15.80526], [34.02198,-15.73105], [34.00073,-15.65643], [33.97958,-15.58147], [33.95844,-15.50625], [33.93725,-15.43085], [33.91595,-15.35535], [33.89445,-15.27982], [33.87269,-15.20435], [33.85059,-15.12900], [33.82809,-15.05387], [33.80511,-14.97903], [33.78159,-14.90456], [33.75744,-14.83053], [33.73261,-14.75703], [33.70701,-14.68413], [33.68059,-14.61192], [33.65326,-14.54046], [33.62496,-14.46984], [33.59568,-14.40008], [33.56553,-14.33110], [33.53462,-14.26280], [33.50306,-14.19511], [33.47096,-14.12793], [33.43844,-14.06118], [33.40560,-13.99477], [33.37256,-13.92861], [33.33943,-13.86263], [33.30632,-13.79672], [33.27335,-13.73081], [33.24062,-13.66480], [33.20824,-13.59861], [33.17634,-13.53216], [33.14502,-13.46535], [33.11438,-13.39810], [33.08456,-13.33032], [33.05564,-13.26193], [33.02776,-13.19283], [33.00092,-13.12302], [32.97501,-13.05255], [32.94992,-12.98152], [32.92550,-12.91001], [32.90164,-12.83810], [32.87821,-12.76587], [32.85508,-12.69342], [32.83212,-12.62082], [32.80921,-12.54815], [32.78623,-12.47551], [32.76304,-12.40297], [32.73952,-12.33062], [32.71555,-12.25854], [32.69099,-12.18682], [32.66573,-12.11553], [32.63962,-12.04477], [32.61256,-11.97462], [32.58441,-11.90515], [32.55504,-11.83646], [32.52435,-11.76862], [32.49235,-11.70161], [32.45914,-11.63537], [32.42483,-11.56984], [32.38950,-11.50496], [32.35326,-11.44066], [32.31621,-11.37688], [32.27844,-11.31356], [32.24006,-11.25062], [32.20116,-11.18802], [32.16183,-11.12568], [32.12219,-11.06354], [32.08232,-11.00154], [32.04233,-10.93962], [32.00232,-10.87771], [31.96237,-10.81575], [31.92260,-10.75367], [31.88309,-10.69141], [31.84396,-10.62892], [31.80528,-10.56612], [31.76710,-10.50300], [31.72937,-10.43957], [31.69205,-10.37588], [31.65510,-10.31193], [31.61847,-10.24775], [31.58213,-10.18337], [31.54604,-10.11881], [31.51015,-10.05409], [31.47442,-9.98924], [31.43881,-9.92428], [31.40327,-9.85924], [31.36778,-9.79413], [31.33228,-9.72899], [31.29673,-9.66384], [31.26109,-9.59870], [31.22533,-9.53359], [31.18940,-9.46855], [31.15325,-9.40358], [31.11685,-9.33872], [31.08016,-9.27399], [31.04320,-9.20938], [31.00595,-9.14489], [30.96842,-9.08051], [30.93063,-9.01626], [30.89256,-8.95212], [30.85423,-8.88808], [30.81564,-8.82416], [30.77678,-8.76034], [30.73768,-8.69662], [30.69832,-8.63301], [30.65872,-8.56949], [30.61888,-8.50606], [30.57879,-8.44273], [30.53847,-8.37949], [30.49792,-8.31633], [30.45714,-8.25326], [30.41614,-8.19027], [30.37491,-8.12736], [30.33347,-8.06453], [30.29181,-8.00177], [30.24995,-7.93908], [30.20788,-7.87646], [30.16561,-7.81391], [30.12314,-7.75142], [30.08047,-7.68899], [30.03761,-7.62662], [29.99457,-7.56430], [29.95134,-7.50204], [29.90793,-7.43983], [29.86435,-7.37766], [29.82060,-7.31555], [29.77667,-7.25347], [29.73258,-7.19143], [29.68833,-7.12943], [29.64392,-7.06747], [29.59936,-7.00554], [29.55465,-6.94363], [29.50979,-6.88176], [29.46479,-6.81991], [29.41965,-6.75810], [29.37436,-6.69632], [29.32894,-6.63459], [29.28339,-6.57291], [29.23770,-6.51128], [29.19189,-6.44972], [29.14594,-6.38822], [29.09987,-6.32678], [29.05367,-6.26543], [29.00735,-6.20415], [28.96091,-6.14297], [28.91436,-6.08187], [28.86769,-6.02087], [28.82090,-5.95997], [28.77400,-5.89918], [28.72700,-5.83851], [28.67989,-5.77795], [28.63267,-5.71751], [28.58535,-5.65720], [28.53793,-5.59703], [28.49041,-5.53699], [28.44279,-5.47710], [28.39508,-5.41736], [28.34728,-5.35777], [28.29938,-5.29834], [28.25140,-5.23908], [28.20334,-5.17999], [28.15519,-5.12108], [28.10696,-5.06234], [28.05865,-5.00380], [28.01026,-4.94544], [27.96180,-4.88728], [27.91327,-4.82932], [27.86466,-4.77157], [27.81599,-4.71404], [27.76725,-4.65672], [27.71844,-4.59962], [27.66958,-4.54275], [27.62065,-4.48607], [27.57166,-4.42956], [27.52262,-4.37319], [27.47352,-4.31692], [27.42436,-4.26073], [27.37515,-4.20458], [27.32589,-4.14846], [27.27658,-4.09232], [27.22722,-4.03613], [27.17782,-3.97988], [27.12836,-3.92352], [27.07887,-3.86703], [27.02932,-3.81037], [26.97974,-3.75352], [26.93012,-3.69645], [26.88046,-3.63913], [26.83076,-3.58152], [26.78103,-3.52360], [26.73126,-3.46533], [26.68145,-3.40673], [26.63158,-3.34783], [26.58163,-3.28867], [26.53157,-3.22931], [26.48140,-3.16977], [26.43109,-3.11011], [26.38062,-3.05037], [26.32997,-2.99059], [26.27912,-2.93081], [26.22806,-2.87108], [26.17676,-2.81144], [26.12520,-2.75194], [26.07336,-2.69261], [26.02123,-2.63351], [25.96878,-2.57466], [25.91600,-2.51613], [25.86287,-2.45795], [25.80936,-2.40015], [25.75546,-2.34280], [25.70116,-2.28603], [25.64654,-2.23063], [25.59172,-2.17760], [25.53681,-2.12796], [25.48193,-2.08272], [25.42718,-2.04291], [25.37269,-2.00952], [25.31857,-1.98359], [25.26493,-1.96608], [25.21172,-1.95719], [25.15871,-1.95618], [25.10567,-1.96227], [25.05237,-1.97468], [24.99856,-1.99263], [24.94403,-2.01533], [24.88853,-2.04200], [24.83183,-2.07186], [24.77369,-2.10413], [24.71388,-2.13803], [24.65218,-2.17281], [24.58858,-2.20807], [24.52315,-2.24365], [24.45601,-2.27938], [24.38725,-2.31508], [24.31696,-2.35059], [24.24525,-2.38574], [24.17220,-2.42036], [24.09792,-2.45428], [24.02250,-2.48734], [23.94604,-2.51936], [23.86864,-2.55017], [23.79039,-2.57962], [23.71140,-2.60752], [23.63174,-2.63371], [23.55154,-2.65802], [23.47087,-2.68028], [23.38985,-2.70033], [23.30855,-2.71799], [23.22709,-2.73310], [23.14556,-2.74548], [23.06406,-2.75498], [22.98267,-2.76141], [22.90151,-2.76463], [22.82062,-2.76463], [22.74006,-2.76148], [22.65988,-2.75524], [22.58014,-2.74598], [22.50087,-2.73376], [22.42213,-2.71864], [22.34397,-2.70070], [22.26643,-2.68000], [22.18958,-2.65659], [22.11345,-2.63056], [22.03810,-2.60196], [21.96358,-2.57086], [21.88993,-2.53732], [21.81722,-2.50141], [21.74547,-2.46319], [21.67476,-2.42273], [21.60512,-2.38009], [21.53660,-2.33535], [21.46926,-2.28856], [21.40315,-2.23978], [21.33831,-2.18910], [21.27479,-2.13656], [21.21265,-2.08223], [21.15193,-2.02619], [21.09269,-1.96849], [21.03497,-1.90921], [20.97882,-1.84839], [20.92429,-1.78612], [20.87144,-1.72246], [20.82031,-1.65746], [20.77095,-1.59121], [20.72342,-1.52375], [20.67775,-1.45516], [20.63401,-1.38550], [20.59223,-1.31484], [20.55248,-1.24324], [20.51480,-1.17077], [20.47924,-1.09749], [20.44584,-1.02347], [20.41467,-0.94877], [20.38577,-0.87343], [20.35921,-0.79750], [20.33503,-0.72100], [20.31330,-0.64398], [20.29408,-0.56645], [20.27742,-0.48846], [20.26338,-0.41005], [20.25201,-0.33123], [20.24339,-0.25206], [20.23755,-0.17256], [20.23457,-0.09277], [20.23450,-0.01272], [20.23739,0.06756], [20.24331,0.14802], [20.25231,0.22865], [20.26445,0.30940], [20.27979,0.39023], [20.29838,0.47113], [20.32029,0.55204], [20.34554,0.63293], [20.37383,0.71366], [20.40459,0.79398], [20.43723,0.87367], [20.47120,0.95250], [20.50589,1.03022], [20.54075,1.10662], [20.57519,1.18144], [20.60864,1.25447], [20.64052,1.32551], [20.67026,1.39454], [20.69730,1.46157], [20.72107,1.52664], [20.74101,1.58974], [20.75655,1.65091], [20.76711,1.71016], [20.77215,1.76751], [20.77109,1.82297], [20.76336,1.87657], [20.74841,1.92832], [20.72604,1.97833], [20.69685,2.02688], [20.66154,2.07425], [20.62080,2.12075], [20.57533,2.16669], [20.52582,2.21234], [20.47297,2.25802], [20.41748,2.30402], [20.35995,2.35058], [20.30070,2.39766], [20.23998,2.44520], [20.17802,2.49310], [20.11507,2.54130], [20.05137,2.58970], [19.98717,2.63823], [19.92271,2.68681], [19.85822,2.73535], [19.79396,2.78378], [19.73017,2.83202], [19.66707,2.87998], [19.60471,2.92765], [19.54305,2.97503], [19.48201,3.02214], [19.42155,3.06897], [19.36159,3.11555], [19.30207,3.16187], [19.24294,3.20795], [19.18413,3.25380], [19.12559,3.29942], [19.06725,3.34482], [19.00905,3.39002], [18.95093,3.43503], [18.89283,3.47984], [18.83469,3.52447], [18.77645,3.56893], [18.71804,3.61323], [18.65941,3.65738], [18.60050,3.70138], [18.54124,3.74525], [18.48160,3.78899], [18.42158,3.83260], [18.36121,3.87610], [18.30049,3.91948], [18.23946,3.96276], [18.17811,4.00592], [18.11648,4.04899], [18.05457,4.09195], [17.99241,4.13483], [17.93001,4.17761], [17.86739,4.22031], [17.80456,4.26293], [17.74154,4.30548], [17.67835,4.34795], [17.61500,4.39035], [17.55152,4.43269], [17.48791,4.47497], [17.42420,4.51720], [17.36039,4.55937], [17.29652,4.60150], [17.23259,4.64359], [17.16863,4.68563], [17.10464,4.72765], [17.04064,4.76963], [16.97666,4.81159], [16.91271,4.85353], [16.84880,4.89545], [16.78496,4.93736], [16.72119,4.97926], [16.65752,5.02116], [16.59396,5.06306], [16.53053,5.10496], [16.46725,5.14687], [16.40413,5.18879], [16.34119,5.23073], [16.27844,5.27269], [16.21591,5.31468], [16.15361,5.35670], [16.09155,5.39875], [16.02971,5.44083], [15.96808,5.48292], [15.90663,5.52501], [15.84532,5.56710], [15.78414,5.60916], [15.72306,5.65120], [15.66206,5.69319], [15.60111,5.73513], [15.54018,5.77701], [15.47925,5.81881], [15.41829,5.86052], [15.35728,5.90214], [15.29620,5.94365], [15.23501,5.98504], [15.17369,6.02630], [15.11222,6.06741], [15.05057,6.10837], [14.98872,6.14917], [14.92664,6.18980], [14.86433,6.23024], [14.80179,6.27052], [14.73905,6.31064], [14.67612,6.35061], [14.61301,6.39043], [14.54975,6.43013], [14.48634,6.46970], [14.42279,6.50917], [14.35914,6.54852], [14.29538,6.58778], [14.23153,6.62696], [14.16762,6.66606], [14.10365,6.70509], [14.03964,6.74406], [13.97561,6.78298], [13.91157,6.82186], [13.84753,6.86071], [13.78351,6.89954], [13.71953,6.93835], [13.65559,6.97716], [13.59170,7.01596], [13.52784,7.05474], [13.46401,7.09351], [13.40022,7.13225], [13.33644,7.17096], [13.27268,7.20964], [13.20894,7.24828], [13.14520,7.28689], [13.08147,7.32544], [13.01773,7.36395], [12.95399,7.40240], [12.89023,7.44079], [12.82646,7.47912], [12.76267,7.51738], [12.69884,7.55557], [12.63499,7.59368], [12.57109,7.63171], [12.50716,7.66965], [12.44318,7.70751], [12.37914,7.74526], [12.31505,7.78292], [12.25090,7.82048], [12.18667,7.85793], [12.12238,7.89526], [12.05801,7.93248], [11.99356,7.96957], [11.92902,8.00654], [11.86438,8.04338], [11.79965,8.08008], [11.73482,8.11665], [11.66988,8.15307], [11.60483,8.18934], [11.53966,8.22546], [11.47436,8.26142], [11.40895,8.29722], [11.34339,8.33285], [11.27771,8.36832], [11.21187,8.40361], [11.14590,8.43872], [11.07979,8.47366], [11.01354,8.50844], [10.94717,8.54307], [10.88068,8.57754], [10.81408,8.61188], [10.74737,8.64609], [10.68057,8.68017], [10.61367,8.71413], [10.54668,8.74798], [10.47962,8.78174], [10.41248,8.81539], [10.34527,8.84896], [10.27801,8.88244], [10.21069,8.91586], [10.14332,8.94921], [10.07591,8.98249], [10.00847,9.01573], [9.94100,9.04893], [9.87351,9.08209], [9.80600,9.11522], [9.73849,9.14833], [9.67097,9.18143], [9.60346,9.21452], [9.53596,9.24761], [9.46848,9.28071], [9.40102,9.31382], [9.33359,9.34696], [9.26620,9.38013], [9.19885,9.41334], [9.13155,9.44659], [9.06431,9.47990], [8.99713,9.51327], [8.93002,9.54670], [8.86299,9.58021], [8.79604,9.61381], [8.72918,9.64749], [8.66241,9.68127], [8.59575,9.71516], [8.52918,9.74915], [8.46271,9.78323], [8.39633,9.81741], [8.33004,9.85166], [8.26381,9.88598], [8.19766,9.92036], [8.13158,9.95480], [8.06555,9.98929], [7.99957,10.02382], [7.93364,10.05838], [7.86775,10.09296], [7.80190,10.12756], [7.73607,10.16216], [7.67026,10.19676], [7.60447,10.23136], [7.53869,10.26594], [7.47291,10.30049], [7.40713,10.33501], [7.34134,10.36949], [7.27553,10.40393], [7.20970,10.43830], [7.14385,10.47261], [7.07796,10.50685], [7.01204,10.54101], [6.94607,10.57508], [6.88004,10.60905], [6.81396,10.64292], [6.74782,10.67667], [6.68160,10.71031], [6.61531,10.74382], [6.54894,10.77719], [6.48248,10.81041], [6.41592,10.84348], [6.34927,10.87640], [6.28251,10.90914], [6.21563,10.94171], [6.14864,10.97409], [6.08153,11.00628], [6.01428,11.03828], [5.94693,11.07011], [5.87949,11.10178], [5.81197,11.13332], [5.74439,11.16475], [5.67677,11.19608], [5.60911,11.22734], [5.54145,11.25855], [5.47379,11.28973], [5.40616,11.32090], [5.33856,11.35208], [5.27101,11.38329], [5.20354,11.41454], [5.13615,11.44587], [5.06887,11.47729], [5.00171,11.50882], [4.93468,11.54048], [4.86781,11.57229], [4.80110,11.60427], [4.73458,11.63645], [4.66822,11.66880], [4.60200,11.70131], [4.53587,11.73393], [4.46979,11.76664], [4.40373,11.79939], [4.33764,11.83217], [4.27149,11.86493], [4.20523,11.89764], [4.13884,11.93027], [4.07226,11.96279], [4.00546,11.99516], [3.93840,12.02736], [3.87105,12.05934], [3.80336,12.09107], [3.73530,12.12253], [3.66682,12.15368], [3.59788,12.18449], [3.52846,12.21492], [3.45850,12.24494], [3.38803,12.27456], [3.31709,12.30380], [3.24573,12.33268], [3.17398,12.36124], [3.10191,12.38950], [3.02956,12.41748], [2.95698,12.44522], [2.88420,12.47274], [2.81129,12.50006], [2.73829,12.52722], [2.66525,12.55423], [2.59220,12.58113], [2.51921,12.60795], [2.44632,12.63470], [2.37357,12.66142], [2.30102,12.68812], [2.22870,12.71485], [2.15668,12.74162], [2.08499,12.76846], [2.01366,12.79540], [1.94269,12.82243], [1.87205,12.84955], [1.80172,12.87677], [1.73169,12.90409], [1.66193,12.93150], [1.59241,12.95901], [1.52313,12.98662], [1.45406,13.01433], [1.38518,13.04214], [1.31647,13.07006], [1.24791,13.09807], [1.17947,13.12618], [1.11115,13.15440], [1.04291,13.18272], [0.97474,13.21115], [0.90662,13.23968], [0.83853,13.26832], [0.77044,13.29706], [0.70234,13.32591], [0.63423,13.35485], [0.56609,13.38388], [0.49793,13.41300], [0.42975,13.44217], [0.36153,13.47141], [0.29328,13.50070], [0.22499,13.53002], [0.15666,13.55938], [0.08828,13.58875], [0.01986,13.61814], [-0.04861,13.64752], [-0.11714,13.67690], [-0.18573,13.70626], [-0.25438,13.73559], [-0.32310,13.76488], [-0.39189,13.79412], [-0.46075,13.82331], [-0.52968,13.85243], [-0.59870,13.88147], [-0.66780,13.91043], [-0.73698,13.93929], [-0.80626,13.96804], [-0.87563,13.99668], [-0.94509,14.02520], [-1.01466,14.05358], [-1.08433,14.08181], [-1.15411,14.10990], [-1.22400,14.13782], [-1.29401,14.16556], [-1.36413,14.19313], [-1.43438,14.22050], [-1.50475,14.24767], [-1.57525,14.27462], [-1.64588,14.30136], [-1.71665,14.32786], [-1.78756,14.35413], [-1.85861,14.38014], [-1.92980,14.40589], [-2.00113,14.43141], [-2.07256,14.45672], [-2.14405,14.48188], [-2.21559,14.50692], [-2.28713,14.53190], [-2.35865,14.55684], [-2.43011,14.58180], [-2.50149,14.60682], [-2.57275,14.63194], [-2.64385,14.65721], [-2.71478,14.68266], [-2.78550,14.70835], [-2.85598,14.73430], [-2.92618,14.76058], [-2.99608,14.78721], [-3.06564,14.81425], [-3.13483,14.84173], [-3.20362,14.86970], [-3.27199,14.89820], [-3.33991,14.92724], [-3.40745,14.95677], [-3.47466,14.98669], [-3.54160,15.01691], [-3.60835,15.04736], [-3.67496,15.07795], [-3.74150,15.10859], [-3.80803,15.13920], [-3.87461,15.16970], [-3.94131,15.19999], [-4.00819,15.23000], [-4.07531,15.25964], [-4.14274,15.28882], [-4.21054,15.31747], [-4.27877,15.34549], [-4.34750,15.37280], [-4.41679,15.39931], [-4.48670,15.42495], [-4.55730,15.44962], [-4.62862,15.47327], [-4.70064,15.49600], [-4.77329,15.51795], [-4.84651,15.53923], [-4.92023,15.55999], [-4.99440,15.58036], [-5.06895,15.60048], [-5.14382,15.62047], [-5.21895,15.64048], [-5.29427,15.66063], [-5.36973,15.68106], [-5.44526,15.70190], [-5.52080,15.72329], [-5.59629,15.74536], [-5.67167,15.76824], [-5.74687,15.79207], [-5.82183,15.81697], [-5.89650,15.84309], [-5.97080,15.87056], [-6.04468,15.89951], [-6.11802,15.92975], [-6.19065,15.96061], [-6.26238,15.99135], [-6.33301,16.02125], [-6.40235,16.04958], [-6.47023,16.07561], [-6.53644,16.09862], [-6.60080,16.11786], [-6.66304,16.13276], [-6.72264,16.14313], [-6.77905,16.14890], [-6.83168,16.14999], [-6.87997,16.14633], [-6.92335,16.13785], [-6.96124,16.12445], [-6.99309,16.10607], [-7.01832,16.08264], [-7.03637,16.05406], [-7.04698,16.02040], [-7.05055,15.98193], [-7.04753,15.93898], [-7.03838,15.89186], [-7.02356,15.84088], [-7.00353,15.78636], [-6.97874,15.72861], [-6.94965,15.66796], [-6.91672,15.60471], [-6.88041,15.53918], [-6.84118,15.47168], [-6.79948,15.40254], [-6.75578,15.33206], [-6.71052,15.26056], [-6.66418,15.18836], [-6.61720,15.11577], [-6.57004,15.04311], [-6.52317,14.97069], [-6.47704,14.89883], [-6.43209,14.82783], [-6.38845,14.75779], [-6.34604,14.68865], [-6.30474,14.62037], [-6.26447,14.55289], [-6.22512,14.48615], [-6.18659,14.42009], [-6.14879,14.35466], [-6.11160,14.28980], [-6.07494,14.22547], [-6.03871,14.16159], [-6.00279,14.09812], [-5.96710,14.03500], [-5.93154,13.97217], [-5.89600,13.90958], [-5.86038,13.84718], [-5.82459,13.78490], [-5.78853,13.72269], [-5.75209,13.66049], [-5.71517,13.59825], [-5.67773,13.53594], [-5.63976,13.47355], [-5.60130,13.41109], [-5.56235,13.34856], [-5.52294,13.28597], [-5.48309,13.22332], [-5.44282,13.16060], [-5.40214,13.09784], [-5.36107,13.03502], [-5.31964,12.97216], [-5.27786,12.90925], [-5.23575,12.84630], [-5.19333,12.78332], [-5.15063,12.72031], [-5.10765,12.65727], [-5.06442,12.59420], [-5.02095,12.53111], [-4.97727,12.46800], [-4.93340,12.40488], [-4.88935,12.34175], [-4.84515,12.27861], [-4.80080,12.21547], [-4.75634,12.15233], [-4.71178,12.08920], [-4.66714,12.02607], [-4.62243,11.96295], [-4.57769,11.89985], [-4.53292,11.83676], [-4.48815,11.77370], [-4.44339,11.71066], [-4.39866,11.64766], [-4.35399,11.58469], [-4.30939,11.52175], [-4.26489,11.45885], [-4.22049,11.39600], [-4.17622,11.33320], [-4.13210,11.27044], [-4.08815,11.20774], [-4.04438,11.14510], [-4.00079,11.08251], [-3.95737,11.01997], [-3.91412,10.95748], [-3.87103,10.89502], [-3.82810,10.83260], [-3.78532,10.77021], [-3.74267,10.70784], [-3.70017,10.64550], [-3.65780,10.58316], [-3.61555,10.52085], [-3.57342,10.45853], [-3.53141,10.39622], [-3.48950,10.33391], [-3.44769,10.27158], [-3.40598,10.20925], [-3.36436,10.14690], [-3.32282,10.08452], [-3.28136,10.02212], [-3.23998,9.95969], [-3.19865,9.89722], [-3.15739,9.83472], [-3.11618,9.77216], [-3.07501,9.70956], [-3.03389,9.64690], [-2.99281,9.58418], [-2.95175,9.52140], [-2.91072,9.45855], [-2.86970,9.39563], [-2.82870,9.33263], [-2.78770,9.26954], [-2.74670,9.20637], [-2.70570,9.14311], [-2.66468,9.07975], [-2.62364,9.01628], [-2.58258,8.95271], [-2.54149,8.88903], [-2.50037,8.82524], [-2.45920,8.76132], [-2.41800,8.69730], [-2.37678,8.63318], [-2.33554,8.56898], [-2.29431,8.50471], [-2.25308,8.44038], [-2.21188,8.37600], [-2.17070,8.31160], [-2.12957,8.24718], [-2.08850,8.18276], [-2.04748,8.11835], [-2.00655,8.05396], [-1.96569,7.98960], [-1.92494,7.92530], [-1.88429,7.86106], [-1.84376,7.79689], [-1.80337,7.73281], [-1.76311,7.66883], [-1.72300,7.60497], [-1.68305,7.54124], [-1.64325,7.47764], [-1.60356,7.41416], [-1.56395,7.35082], [-1.52439,7.28760], [-1.48485,7.22451], [-1.44530,7.16154], [-1.40571,7.09869], [-1.36605,7.03596], [-1.32629,6.97335], [-1.28638,6.91085], [-1.24632,6.84847], [-1.20606,6.78620], [-1.16557,6.72405], [-1.12482,6.66200], [-1.08378,6.60006], [-1.04242,6.53823], [-1.00071,6.47651], [-0.95862,6.41488], [-0.91611,6.35336], [-0.87320,6.29193], [-0.82990,6.23059], [-0.78625,6.16931], [-0.74230,6.10809], [-0.69806,6.04692], [-0.65358,5.98578], [-0.60889,5.92466], [-0.56402,5.86355], [-0.51902,5.80243], [-0.47390,5.74129], [-0.42871,5.68012], [-0.38349,5.61892], [-0.33825,5.55765], [-0.29305,5.49632], [-0.24791,5.43491], [-0.20286,5.37340], [-0.15795,5.31179], [-0.11321,5.25007], [-0.06866,5.18821], [-0.02435,5.12621], [0.01970,5.06405], [0.06344,5.00173], [0.10685,4.93923], [0.14988,4.87653], [0.19251,4.81363], [0.23471,4.75051], [0.27642,4.68716], [0.31764,4.62357], [0.35831,4.55973], [0.39840,4.49561], [0.43789,4.43122], [0.47673,4.36653], [0.51489,4.30154], [0.55234,4.23623], [0.58905,4.17059], [0.62498,4.10461], [0.66009,4.03827], [0.69435,3.97156], [0.72763,3.90455], [0.75916,3.83777], [0.78786,3.77198], [0.81268,3.70794], [0.83256,3.64640], [0.84642,3.58811], [0.85322,3.53384], [0.85188,3.48433], [0.84136,3.44033], [0.82132,3.40212], [0.79231,3.36941], [0.75493,3.34186], [0.70979,3.31913], [0.65749,3.30089], [0.59864,3.28680], [0.53385,3.27653], [0.46372,3.26974], [0.38886,3.26610], [0.30987,3.26526], [0.22736,3.26689], [0.14193,3.27059], [0.05418,3.27586], [-0.03531,3.28223], [-0.12592,3.28922], [-0.21708,3.29635], [-0.30817,3.30313], [-0.39862,3.30909], [-0.48781,3.31373], [-0.57525,3.31667], [-0.66097,3.31793], [-0.74512,3.31767], [-0.82790,3.31606], [-0.90947,3.31326], [-0.99002,3.30944], [-1.06972,3.30477], [-1.14875,3.29940], [-1.22729,3.29351], [-1.30552,3.28725], [-1.38361,3.28081], [-1.46174,3.27432], [-1.54000,3.26789], [-1.61840,3.26152], [-1.69691,3.25520], [-1.77555,3.24892], [-1.85429,3.24269], [-1.93314,3.23651], [-2.01209,3.23036], [-2.09114,3.22424], [-2.17027,3.21815], [-2.24948,3.21210], [-2.32877,3.20606], [-2.40813,3.20005], [-2.48755,3.19405], [-2.56703,3.18807], [-2.64656,3.18210], [-2.72614,3.17614], [-2.80575,3.17017], [-2.88539,3.16421], [-2.96507,3.15825], [-3.04476,3.15228], [-3.12447,3.14629], [-3.20418,3.14030], [-3.28390,3.13428], [-3.36361,3.12825], [-3.44332,3.12219], [-3.52300,3.11611], [-3.60267,3.10999], [-3.68231,3.10384], [-3.76191,3.09765], [-3.84147,3.09142], [-3.92099,3.08515], [-4.00045,3.07883], [-4.07985,3.07245], [-4.15919,3.06603], [-4.23846,3.05954], [-4.31765,3.05299], [-4.39676,3.04638], [-4.47577,3.03969], [-4.55470,3.03294], [-4.63352,3.02611], [-4.71224,3.01921], [-4.79087,3.01223], [-4.86941,3.00518], [-4.94788,2.99806], [-5.02626,2.99087], [-5.10458,2.98362], [-5.18283,2.97630], [-5.26103,2.96892], [-5.33918,2.96148], [-5.41728,2.95398], [-5.49534,2.94642], [-5.57336,2.93881], [-5.65136,2.93115], [-5.72934,2.92343], [-5.80730,2.91567], [-5.88525,2.90785], [-5.96319,2.90000], [-6.04114,2.89209], [-6.11910,2.88415], [-6.19707,2.87616], [-6.27506,2.86814], [-6.35307,2.86007], [-6.43112,2.85198], [-6.50920,2.84385], [-6.58733,2.83569], [-6.66551,2.82750], [-6.74374,2.81928], [-6.82203,2.81103], [-6.90039,2.80277], [-6.97882,2.79447], [-7.05734,2.78616], [-7.13593,2.77783], [-7.21462,2.76949], [-7.29340,2.76113], [-7.37229,2.75275], [-7.45129,2.74437], [-7.53039,2.73597], [-7.60962,2.72757], [-7.68898,2.71916], [-7.76846,2.71074], [-7.84802,2.70225], [-7.92759,2.69364], [-8.00713,2.68484], [-8.08657,2.67578], [-8.16585,2.66640], [-8.24491,2.65663], [-8.32370,2.64642], [-8.40216,2.63570], [-8.48023,2.62441], [-8.55784,2.61247], [-8.63495,2.59984], [-8.71149,2.58643], [-8.78741,2.57220], [-8.86264,2.55707], [-8.93712,2.54099], [-9.01081,2.52388], [-9.08363,2.50569], [-9.15554,2.48634], [-9.22646,2.46579], [-9.29643,2.44406], [-9.36560,2.42137], [-9.43415,2.39798], [-9.50225,2.37414], [-9.57010,2.35009], [-9.63786,2.32608], [-9.70572,2.30237], [-9.77385,2.27919], [-9.84241,2.25675], [-9.91143,2.23507], [-9.98091,2.21410], [-10.05088,2.19382], [-10.12134,2.17418], [-10.19230,2.15517], [-10.26377,2.13674], [-10.33575,2.11886], [-10.40827,2.10150], [-10.48132,2.08462], [-10.55491,2.06819], [-10.62906,2.05218], [-10.70373,2.03655], [-10.77888,2.02126], [-10.85447,2.00627], [-10.93045,1.99154], [-11.00680,1.97704], [-11.08347,1.96271], [-11.16041,1.94854], [-11.23760,1.93447], [-11.31498,1.92046], [-11.39251,1.90649], [-11.47016,1.89250], [-11.54789,1.87846], [-11.62565,1.86433], [-11.70341,1.85008], [-11.78112,1.83566], [-11.85874,1.82103], [-11.93624,1.80616], [-12.01357,1.79100], [-12.09068,1.77552], [-12.16755,1.75968], [-12.24413,1.74343], [-12.32038,1.72675], [-12.39626,1.70959], [-12.47173,1.69190], [-12.54674,1.67367], [-12.62127,1.65483], [-12.69526,1.63536], [-12.76867,1.61522], [-12.84147,1.59436], [-12.91362,1.57275], [-12.98507,1.55035], [-13.05579,1.52712], [-13.12573,1.50302], [-13.19485,1.47801], [-13.26311,1.45206], [-13.33048,1.42512], [-13.39691,1.39715], [-13.46236,1.36812], [-13.52683,1.33803], [-13.59059,1.30720], [-13.65405,1.27605], [-13.71759,1.24504], [-13.78160,1.21460], [-13.84647,1.18517], [-13.91260,1.15719], [-13.98038,1.13109], [-14.05017,1.10729], [-14.12200,1.08581], [-14.19558,1.06631], [-14.27062,1.04846], [-14.34684,1.03192], [-14.42394,1.01634], [-14.50164,1.00139], [-14.57963,0.98672], [-14.65763,0.97200], [-14.73535,0.95689], [-14.81250,0.94105], [-14.88878,0.92414], [-14.96403,0.90594], [-15.03830,0.88652], [-15.11164,0.86593], [-15.18414,0.84425], [-15.25586,0.82155], [-15.32687,0.79790], [-15.39725,0.77336], [-15.46707,0.74802], [-15.53639,0.72194], [-15.60529,0.69519], [-15.67383,0.66784], [-15.74209,0.63996], [-15.81014,0.61163], [-15.87805,0.58291], [-15.94589,0.55387], [-16.01373,0.52459], [-16.08164,0.49514], [-16.14970,0.46558], [-16.21796,0.43599], [-16.28650,0.40643], [-16.35533,0.37692], [-16.42443,0.34746], [-16.49378,0.31803], [-16.56338,0.28865], [-16.63321,0.25930], [-16.70325,0.22997], [-16.77349,0.20067], [-16.84392,0.17139], [-16.91451,0.14212], [-16.98526,0.11287], [-17.05615,0.08362], [-17.12716,0.05438], [-17.19828,0.02513], [-17.26950,-0.00412], [-17.34080,-0.03338], [-17.41217,-0.06266], [-17.48359,-0.09196], [-17.55504,-0.12127], [-17.62652,-0.15062], [-17.69800,-0.18000], [-17.76948,-0.20941], [-17.84093,-0.23887], [-17.91235,-0.26837], [-17.98372,-0.29792], [-18.05502,-0.32752], [-18.12624,-0.35718], [-18.19736,-0.38690], [-18.26838,-0.41668], [-18.33927,-0.44654], [-18.41001,-0.47647], [-18.48061,-0.50648], [-18.55103,-0.53658], [-18.62128,-0.56676], [-18.69132,-0.59704], [-18.76115,-0.62741], [-18.83075,-0.65788], [-18.90011,-0.68845], [-18.96921,-0.71914], [-19.03806,-0.74998], [-19.10666,-0.78100], [-19.17502,-0.81227], [-19.24315,-0.84383], [-19.31104,-0.87571], [-19.37872,-0.90797], [-19.44618,-0.94066], [-19.51343,-0.97381], [-19.58048,-1.00748], [-19.64733,-1.04170], [-19.71399,-1.07654], [-19.78048,-1.11202], [-19.84678,-1.14820], [-19.91292,-1.18513], [-19.97889,-1.22285], [-20.04471,-1.26140], [-20.11038,-1.30083], [-20.17591,-1.34119], [-20.24130,-1.38251], [-20.30657,-1.42474], [-20.37175,-1.46778], [-20.43686,-1.51154], [-20.50192,-1.55592], [-20.56695,-1.60082], [-20.63197,-1.64616], [-20.69701,-1.69183], [-20.76209,-1.73775], [-20.82722,-1.78380], [-20.89245,-1.82991], [-20.95778,-1.87596], [-21.02323,-1.92188], [-21.08884,-1.96756], [-21.15462,-2.01290], [-21.22059,-2.05782], [-21.28678,-2.10221], [-21.35322,-2.14599], [-21.41991,-2.18905], [-21.48689,-2.23129], [-21.55415,-2.27268], [-21.62167,-2.31326], [-21.68938,-2.35312], [-21.75725,-2.39231], [-21.82523,-2.43092], [-21.89328,-2.46903], [-21.96133,-2.50670], [-22.02936,-2.54401], [-22.09730,-2.58103], [-22.16512,-2.61785], [-22.23277,-2.65452], [-22.30020,-2.69113], [-22.36737,-2.72775], [-22.43422,-2.76445], [-22.50071,-2.80131], [-22.56680,-2.83840], [-22.63243,-2.87580], [-22.69757,-2.91358], [-22.76216,-2.95181], [-22.82616,-2.99057], [-22.88955,-3.02989], [-22.95237,-3.06976], [-23.01467,-3.11016], [-23.07649,-3.15106], [-23.13786,-3.19245], [-23.19884,-3.23429], [-23.25946,-3.27657], [-23.31977,-3.31927], [-23.37981,-3.36235], [-23.43962,-3.40581], [-23.49924,-3.44962], [-23.55872,-3.49376], [-23.61810,-3.53820], [-23.67742,-3.58292], [-23.73672,-3.62791], [-23.79604,-3.67313], [-23.85544,-3.71857], [-23.91494,-3.76420], [-23.97460,-3.81001], [-24.03444,-3.85597], [-24.09448,-3.90207], [-24.15468,-3.94833], [-24.21503,-3.99474], [-24.27552,-4.04131], [-24.33612,-4.08804], [-24.39682,-4.13494], [-24.45759,-4.18200], [-24.51842,-4.22922], [-24.57928,-4.27662], [-24.64017,-4.32420], [-24.70106,-4.37195], [-24.76194,-4.41989], [-24.82278,-4.46801], [-24.88356,-4.51631], [-24.94428,-4.56481], [-25.00490,-4.61349], [-25.06541,-4.66238], [-25.12580,-4.71146], [-25.18603,-4.76074], [-25.24611,-4.81023], [-25.30600,-4.85992], [-25.36568,-4.90983], [-25.42515,-4.95995], [-25.48437,-5.01029], [-25.54334,-5.06084], [-25.60203,-5.11162], [-25.66043,-5.16262], [-25.71851,-5.21385], [-25.77626,-5.26532], [-25.83366,-5.31701], [-25.89069,-5.36895], [-25.94733,-5.42112], [-26.00356,-5.47354], [-26.05937,-5.52620], [-26.11473,-5.57911], [-26.16963,-5.63228], [-26.22405,-5.68570], [-26.27797,-5.73937], [-26.33139,-5.79331], [-26.38433,-5.84751], [-26.43682,-5.90197], [-26.48888,-5.95669], [-26.54055,-6.01168], [-26.59185,-6.06693], [-26.64280,-6.12245], [-26.69344,-6.17823], [-26.74378,-6.23429], [-26.79386,-6.29061], [-26.84371,-6.34720], [-26.89334,-6.40406], [-26.94278,-6.46120], [-26.99207,-6.51861], [-27.04122,-6.57629], [-27.09027,-6.63425], [-27.13925,-6.69248], [-27.18816,-6.75099], [-27.23706,-6.80978], [-27.28595,-6.86884], [-27.33482,-6.92814], [-27.38369,-6.98767], [-27.43253,-7.04739], [-27.48134,-7.10727], [-27.53011,-7.16729], [-27.57885,-7.22742], [-27.62753,-7.28762], [-27.67616,-7.34788], [-27.72473,-7.40817], [-27.77323,-7.46845], [-27.82166,-7.52869], [-27.87000,-7.58888], [-27.91826,-7.64898], [-27.96642,-7.70897], [-28.01448,-7.76881], [-28.06243,-7.82848], [-28.11027,-7.88795], [-28.15799,-7.94720], [-28.20558,-8.00619], [-28.25304,-8.06493], [-28.30038,-8.12346], [-28.34761,-8.18181], [-28.39473,-8.23999], [-28.44175,-8.29805], [-28.48867,-8.35602], [-28.53549,-8.41392], [-28.58223,-8.47178], [-28.62889,-8.52963], [-28.67548,-8.58751], [-28.72199,-8.64545], [-28.76844,-8.70346], [-28.81483,-8.76159], [-28.86117,-8.81987], [-28.90746,-8.87831], [-28.95371,-8.93697], [-28.99993,-8.99585], [-29.04611,-9.05500], [-29.09227,-9.11444], [-29.13839,-9.17418], [-29.18444,-9.23424], [-29.23039,-9.29461], [-29.27621,-9.35528], [-29.32185,-9.41627], [-29.36730,-9.47756], [-29.41251,-9.53917], [-29.45745,-9.60108], [-29.50210,-9.66331], [-29.54642,-9.72585], [-29.59038,-9.78870], [-29.63394,-9.85186], [-29.67707,-9.91533], [-29.71975,-9.97912], [-29.76193,-10.04321], [-29.80358,-10.10763], [-29.84468,-10.17235], [-29.88519,-10.23739], [-29.92507,-10.30274], [-29.96433,-10.36840], [-30.00299,-10.43434], [-30.04108,-10.50057], [-30.07863,-10.56704], [-30.11567,-10.63376], [-30.15221,-10.70070], [-30.18830,-10.76786], [-30.22395,-10.83520], [-30.25921,-10.90272],
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
