kuato781/spirit-wave-stand/documentation/product-images/02-assembled.jpg

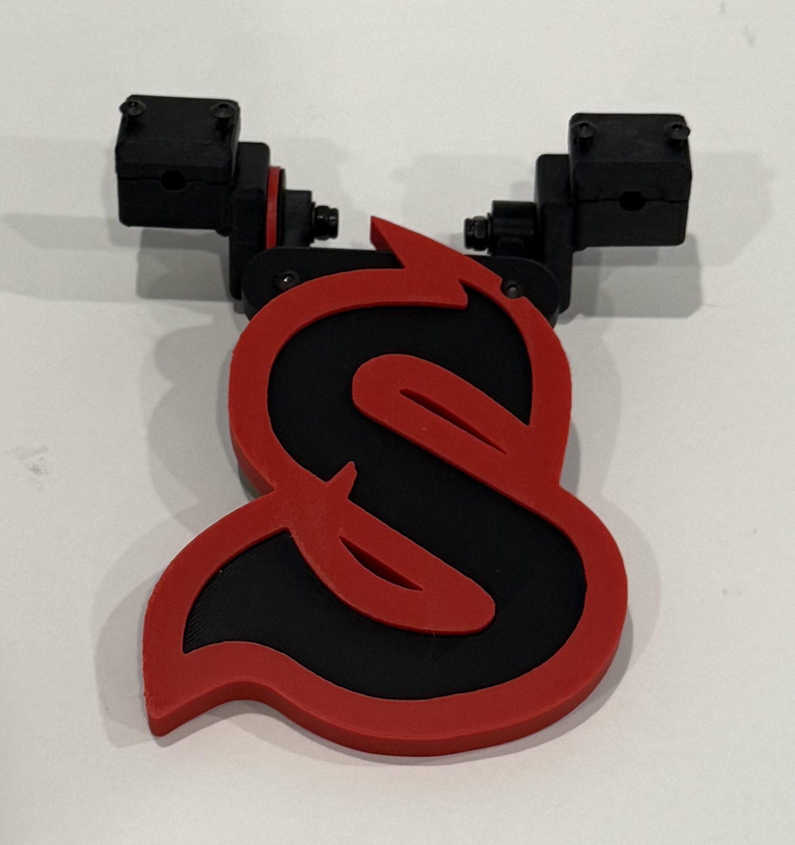
documentation/product-images/02-assembled.jpg
